astromik/SQM/SQM_verze411/hw/katalogove_listy/čočka-OEHW2030GF.pdf

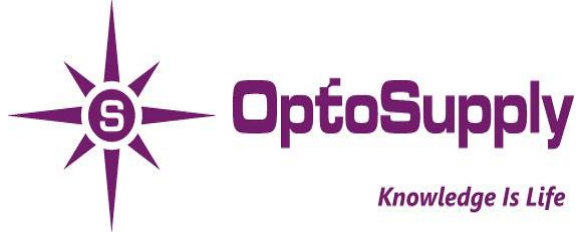
[picture p48: figure]
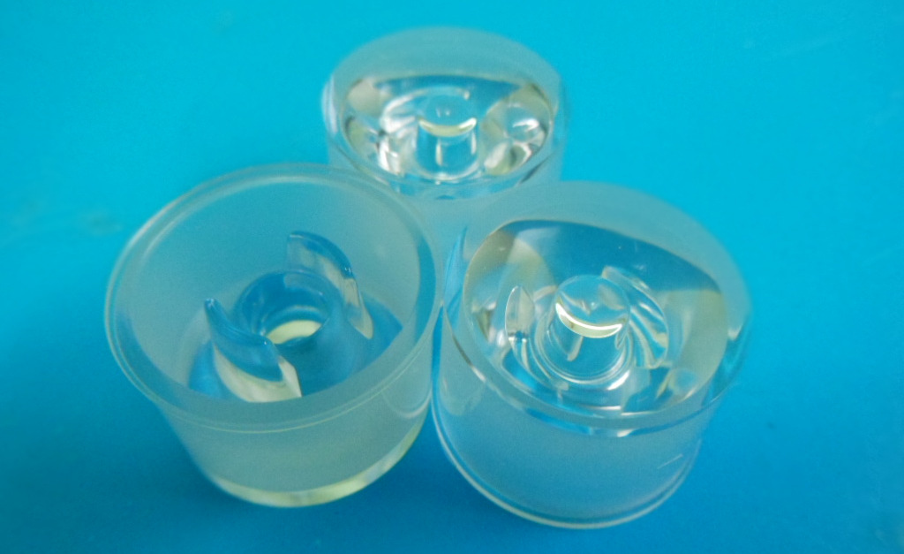
[picture p49: figure]
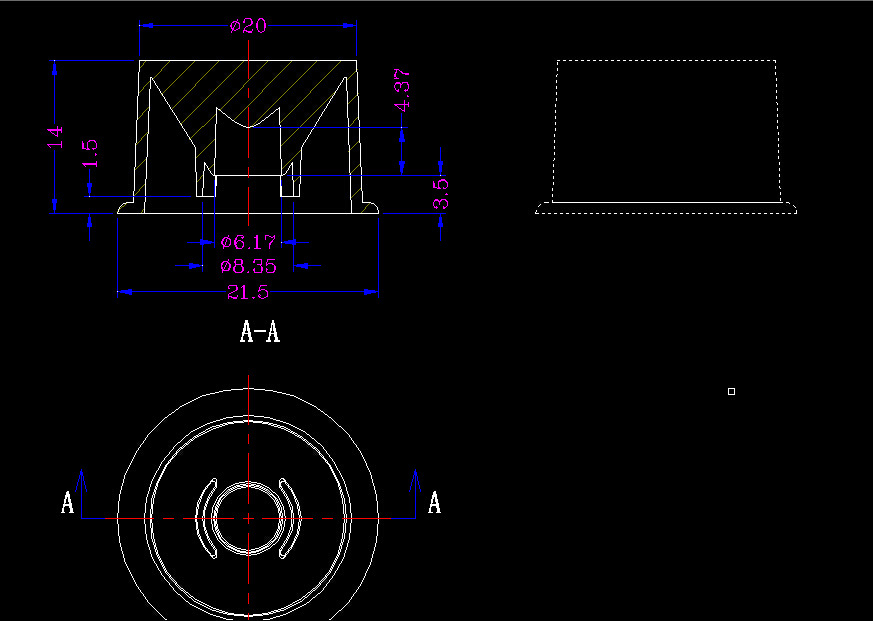
[picture p50: figure]

www.optosupply.hk | 1 | ver.1

Unit:mm
| Tolerance:±0.3mm
Descriptions: | 1
Models | OEHW2030GF
Specification | φ21.5*14mm
Perspective | 30
Wick | 1
Material | PMMA
Transmittance | 93%
Temperature | -35℃-90℃
Tolerance | ±0.3mm
Standard | SGS/ROHS
Surface Treatment | Transparent
Product Picture and Dimensions | s
Model No. | OEHW2030GF
VER. | 1
