astromik/SQM/SQM_verze411/hw/katalogove_listy/KL-switch-ss-12d06l5.pdf

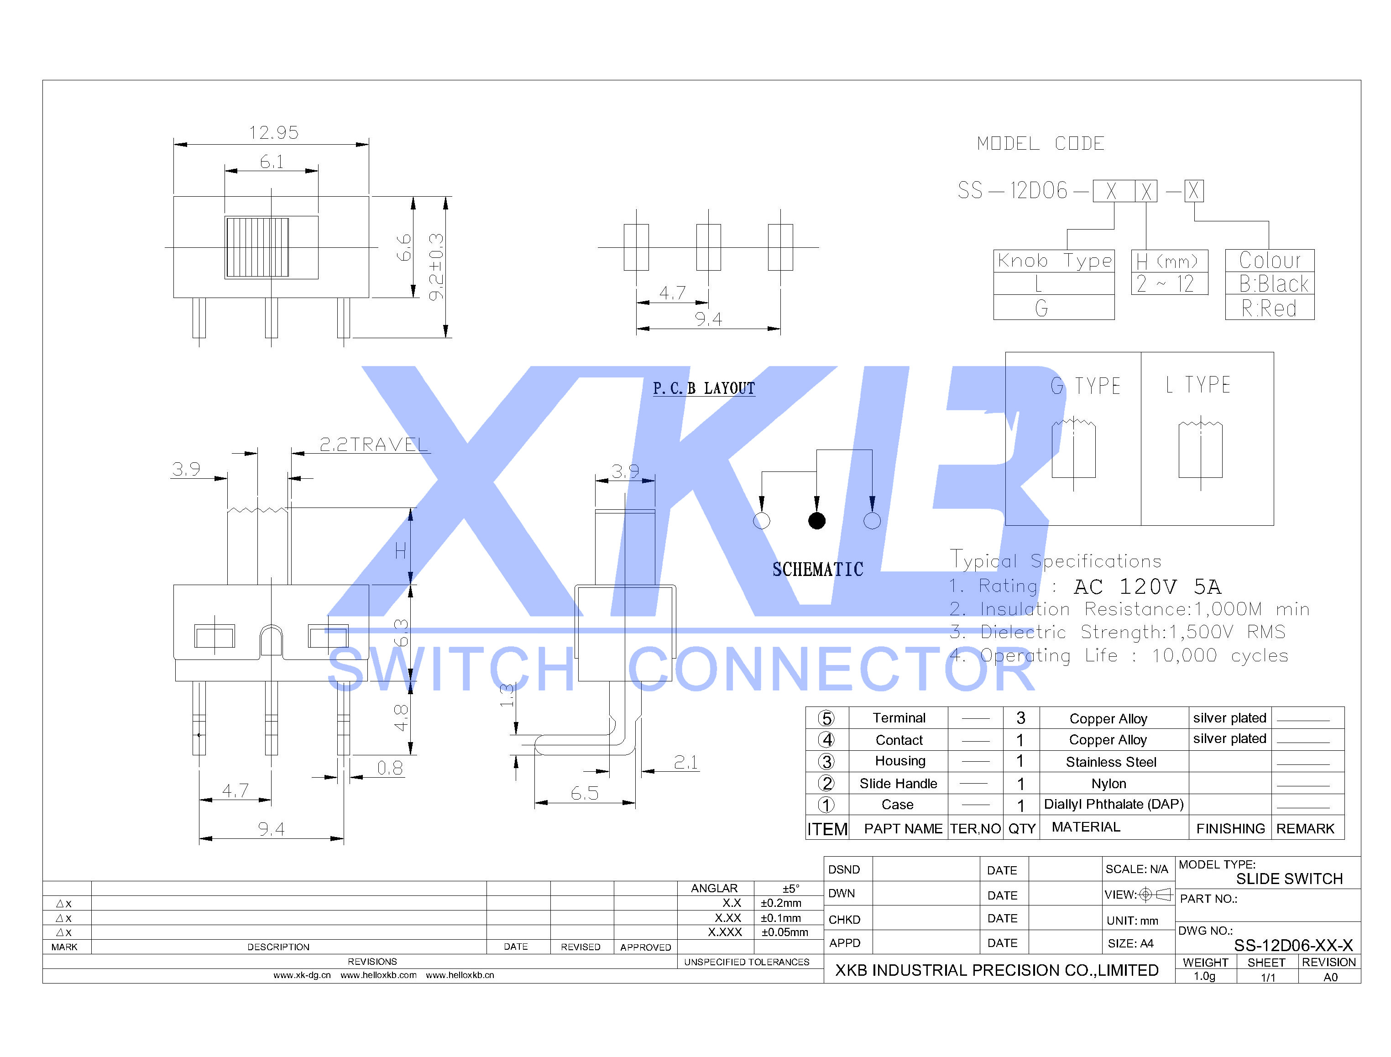
[picture p112: page 1]
