astromik/SQM/SQM_verze411/hw/krabicka/detaily_jlcpcb.gif

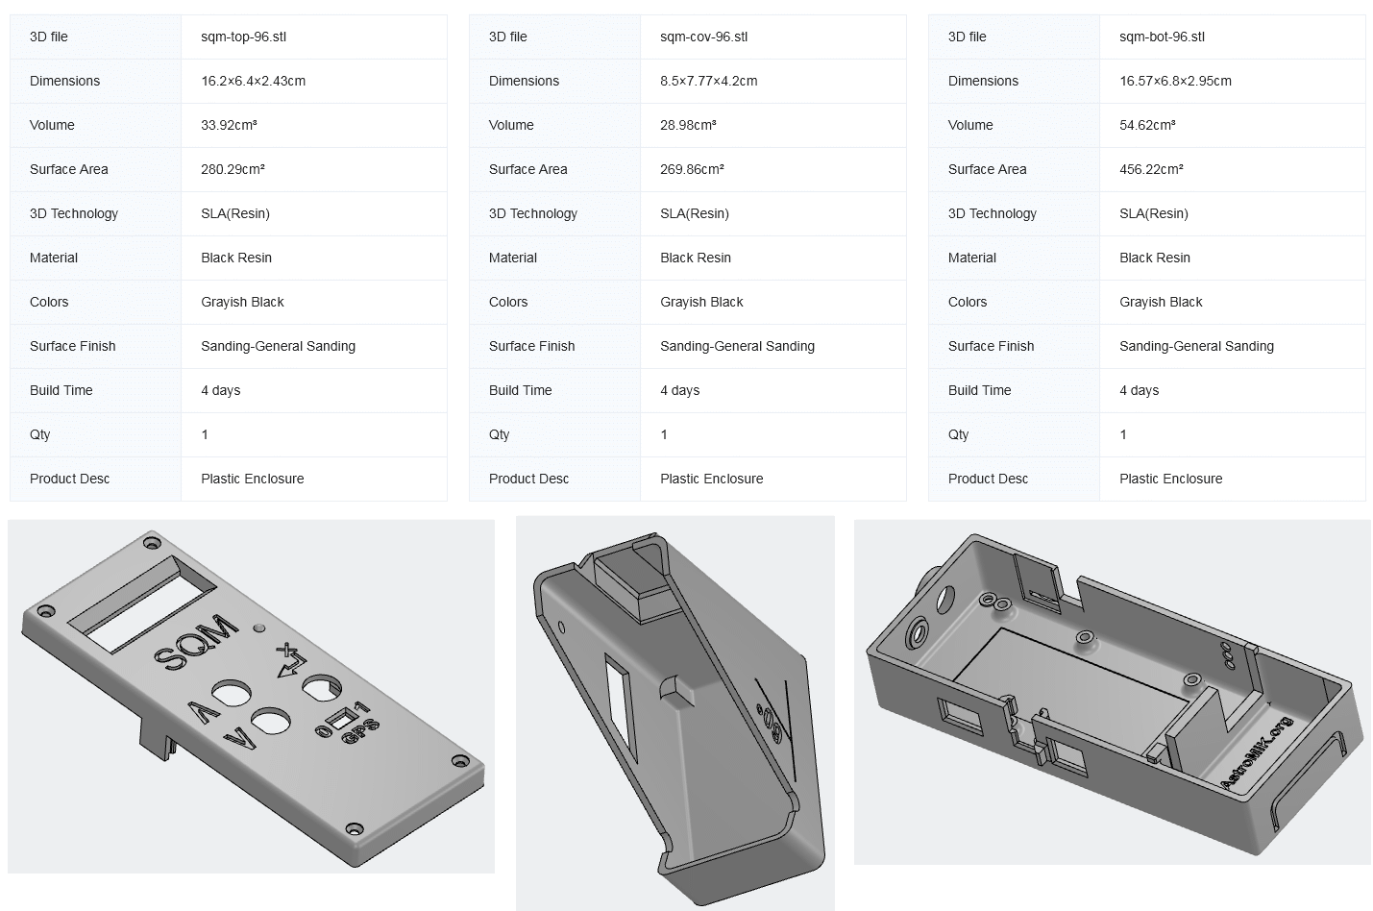
SQM_verze411/hw/krabicka/detaily_jlcpcb.gif
