astromik/SQM/SQM_verze411/hw/krabicka/krabicka_obr1.gif

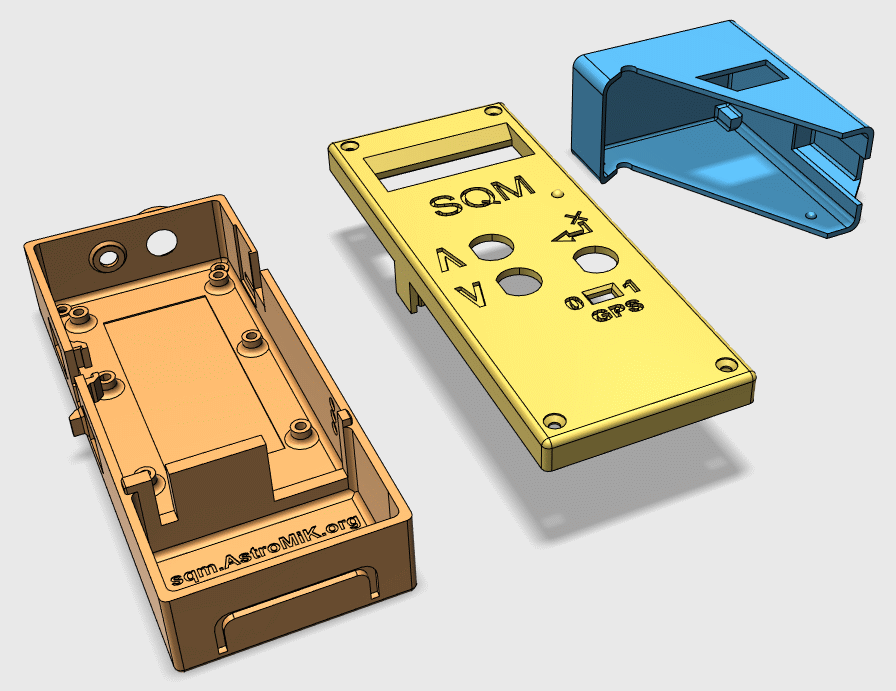
SQM_verze411/hw/krabicka/krabicka_obr1.gif
