astromik/SQM/SQM_verze411/hw/krabicka/krabicka_obr2.gif

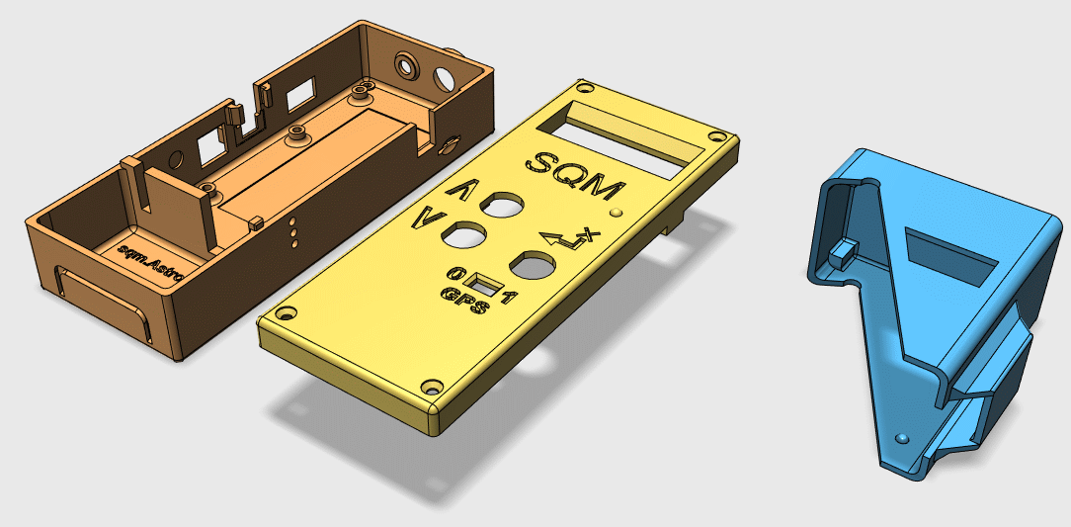
SQM_verze411/hw/krabicka/krabicka_obr2.gif
