astromik/SQM/SQM_verze411/hw/krabicka/krabicka_obr3.gif

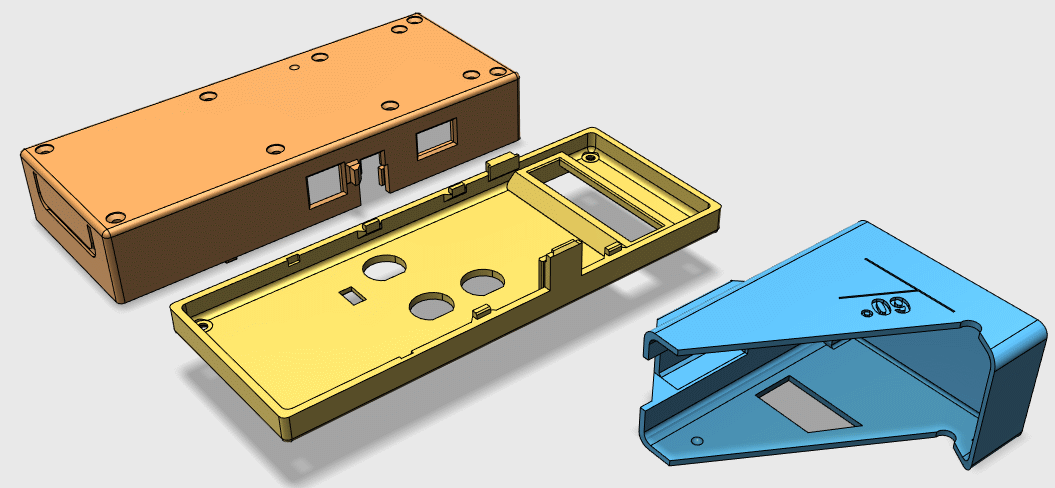
SQM_verze411/hw/krabicka/krabicka_obr3.gif
