astromik/SQM/SQM_verze411/programy/STM32_CubeProgrammer/CubeProg_screen.gif

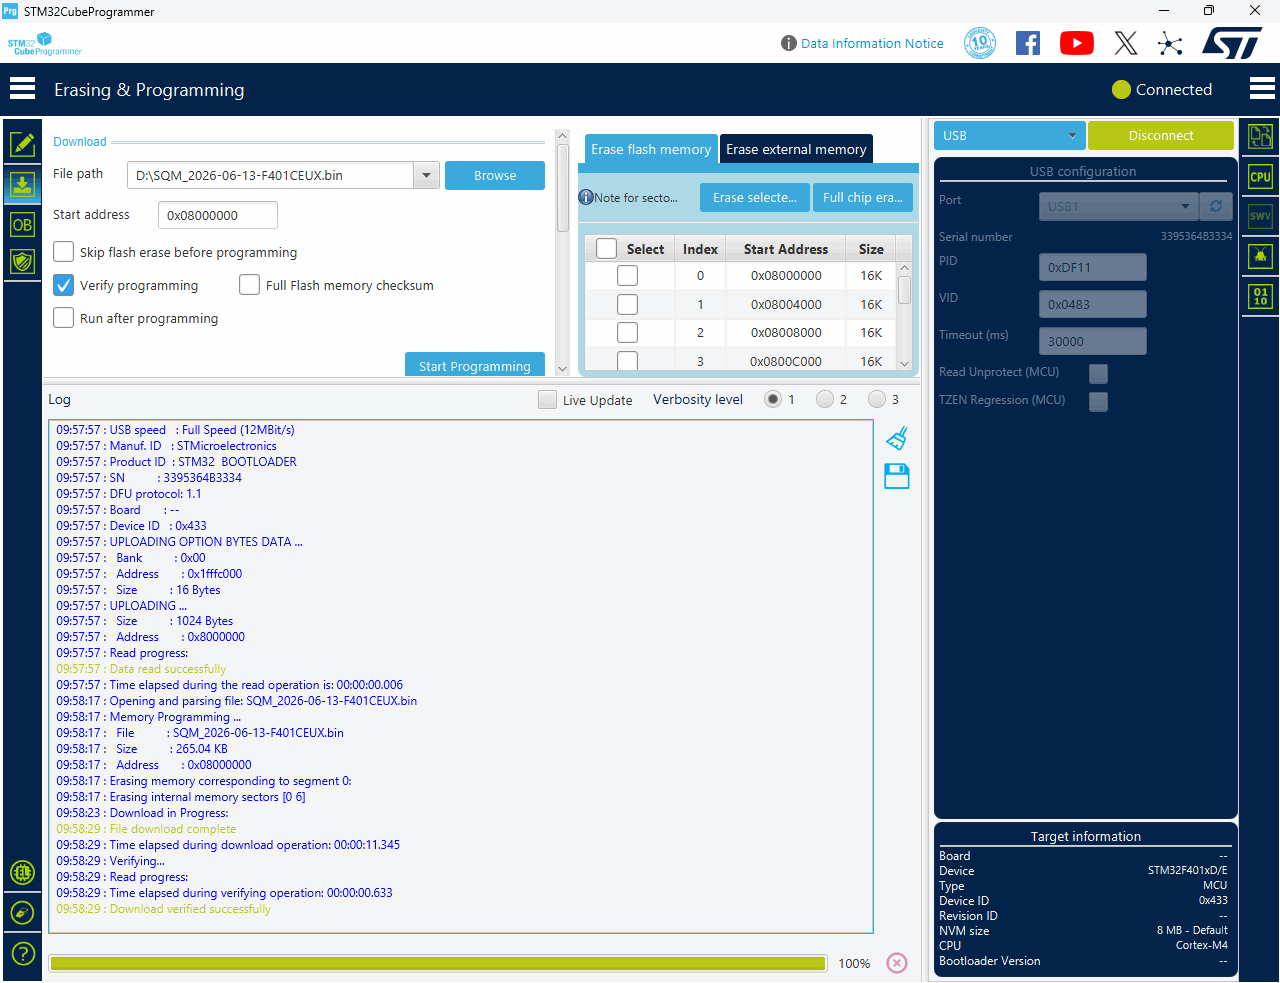
SQM_verze411/programy/STM32_CubeProgrammer/CubeProg_screen.gif
