astromik/SQM/SQM_verze411/webconfig/baterie_top.gif

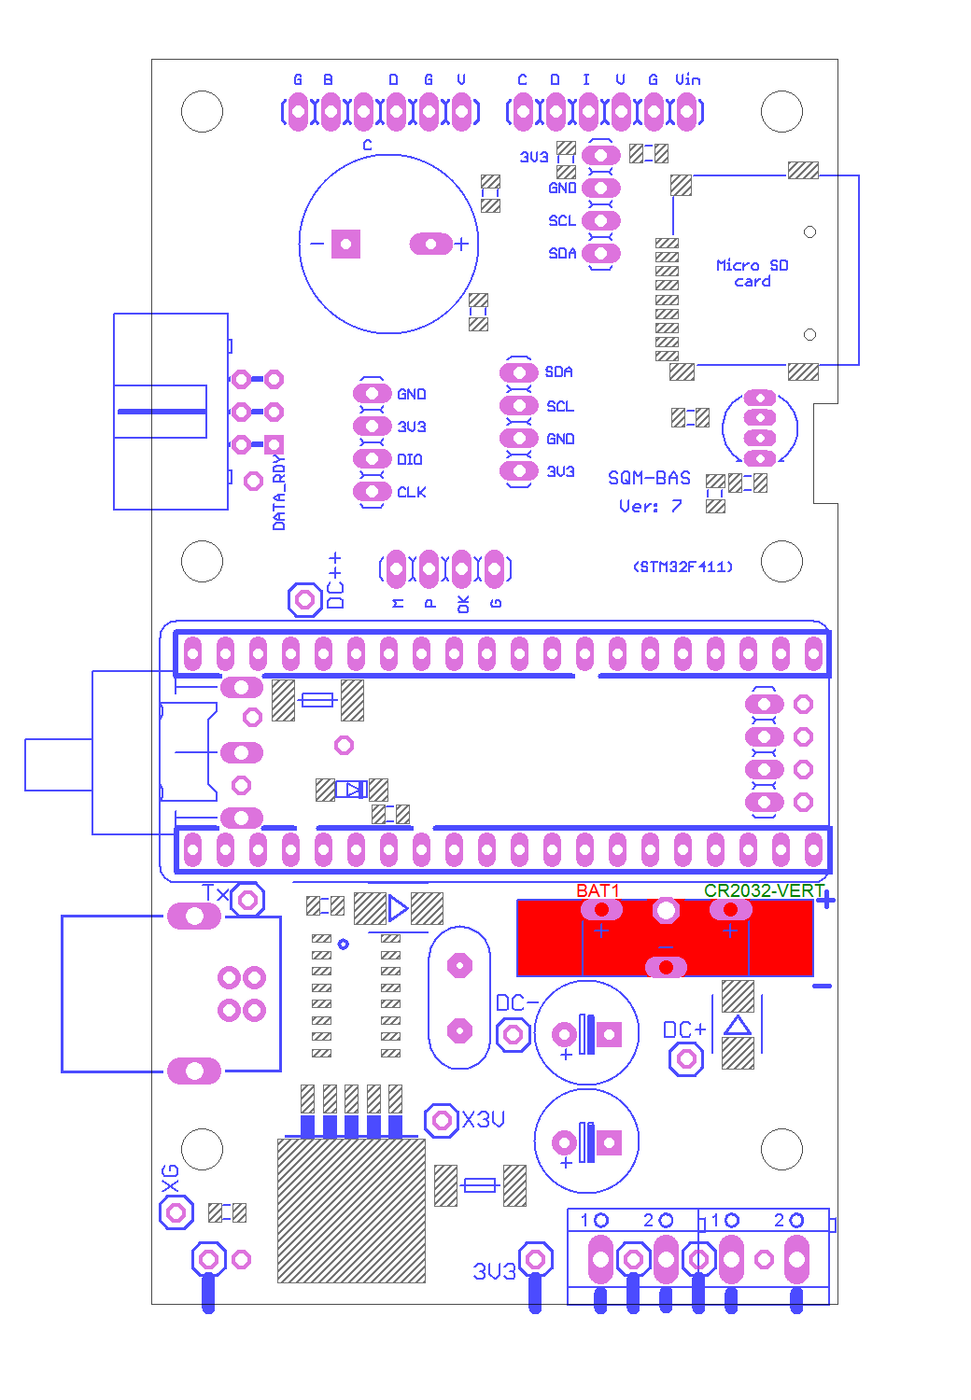
SQM_verze411/webconfig/baterie_top.gif
