astromik/SQM/SQM_verze411/webconfig/batkap_iko.jpg

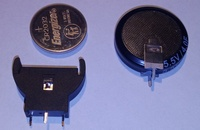
SQM_verze411/webconfig/batkap_iko.jpg
