astromik/SQM/SQM_verze411/webconfig/bme280_bot.gif

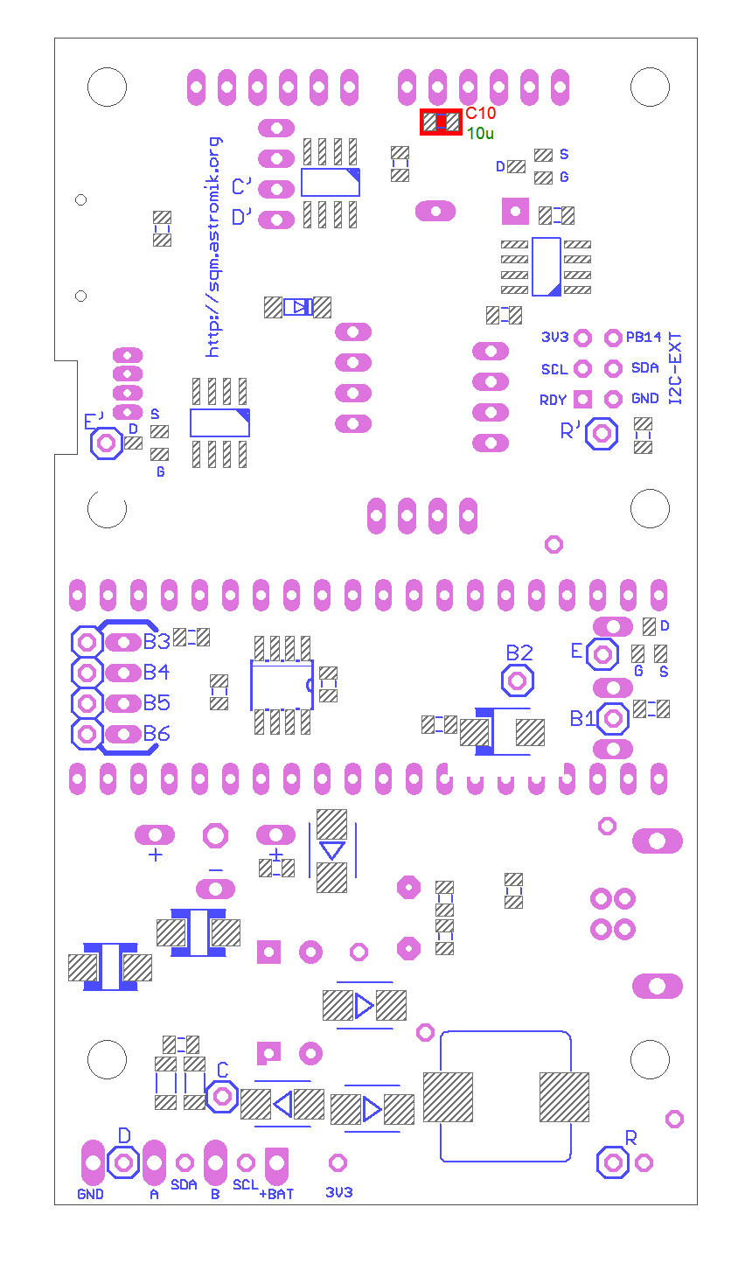
SQM_verze411/webconfig/bme280_bot.gif
