astromik/SQM/SQM_verze411/webconfig/bme280_top.gif

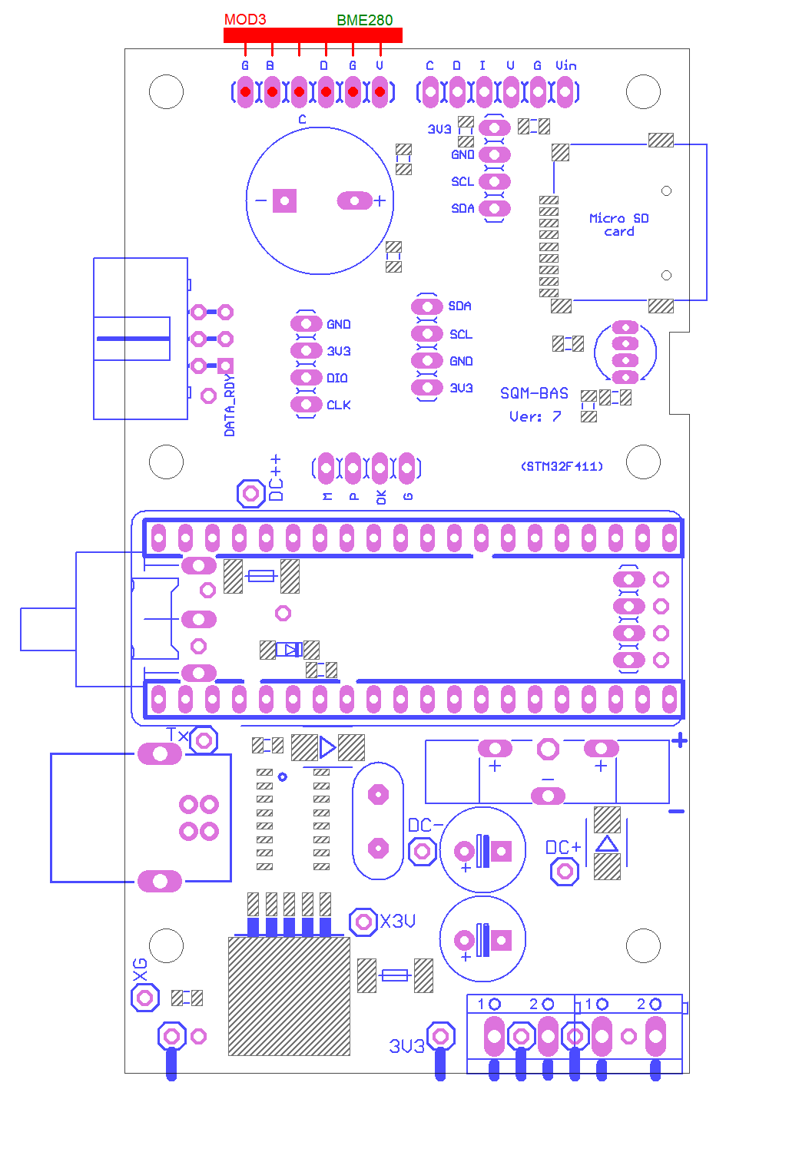
SQM_verze411/webconfig/bme280_top.gif
