astromik/SQM/SQM_verze411/webconfig/bme_iko.jpg

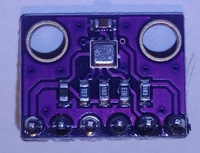
SQM_verze411/webconfig/bme_iko.jpg
