astromik/SQM/SQM_verze411/webconfig/bzuk_iko.jpg

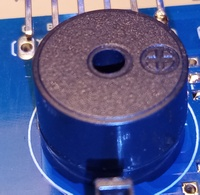
SQM_verze411/webconfig/bzuk_iko.jpg
