astromik/SQM/SQM_verze411/webconfig/bzuk_top.gif

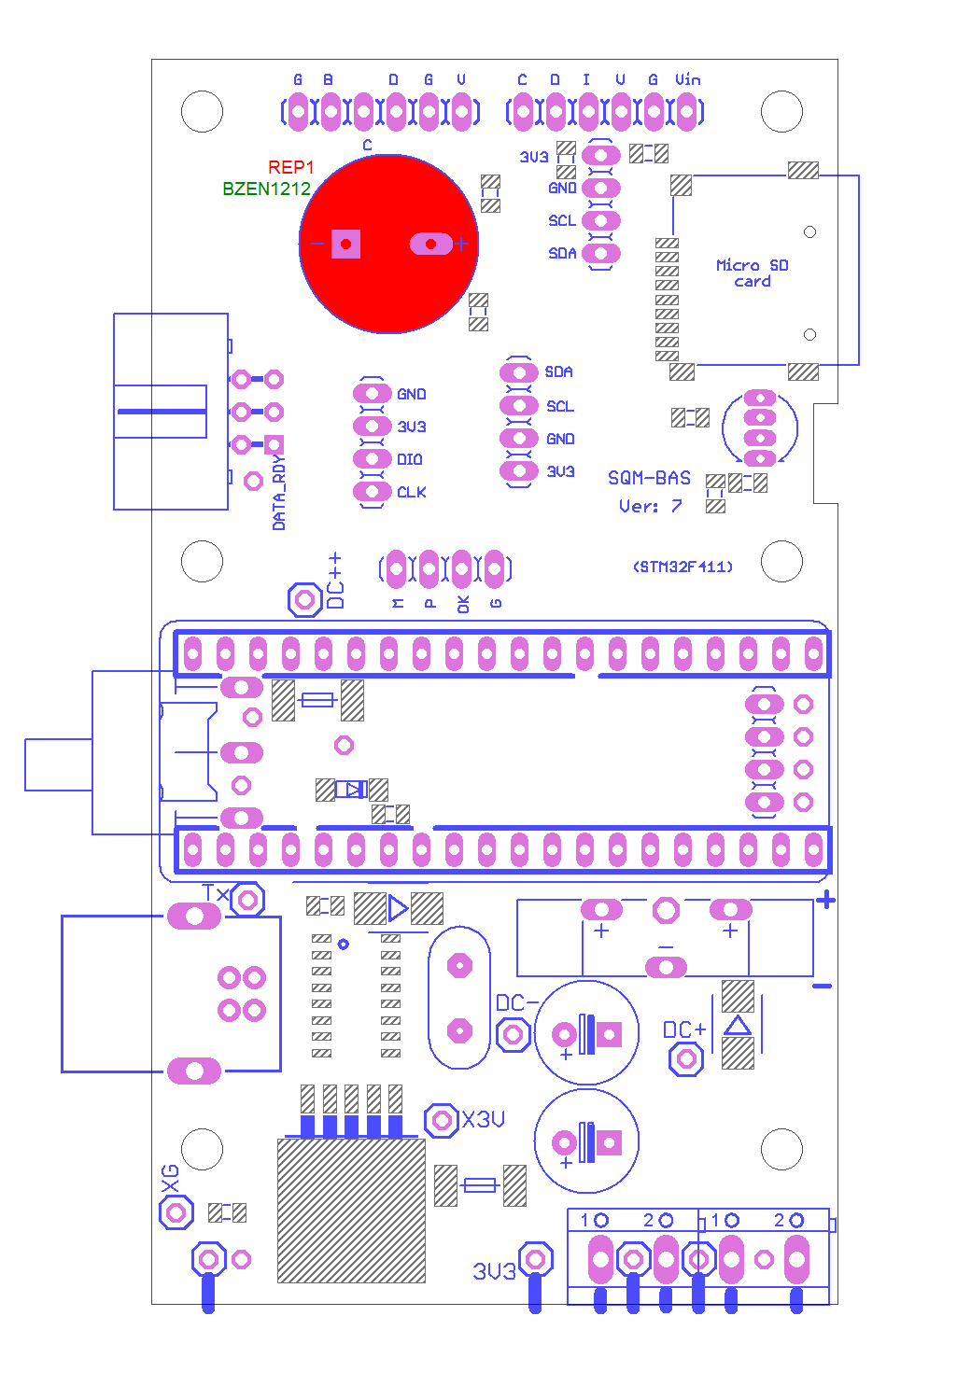
SQM_verze411/webconfig/bzuk_top.gif
