astromik/SQM/SQM_verze411/webconfig/dis_iko.jpg

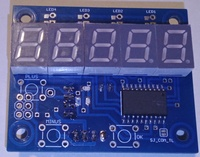
SQM_verze411/webconfig/dis_iko.jpg
