astromik/SQM/SQM_verze411/webconfig/displej_top.gif

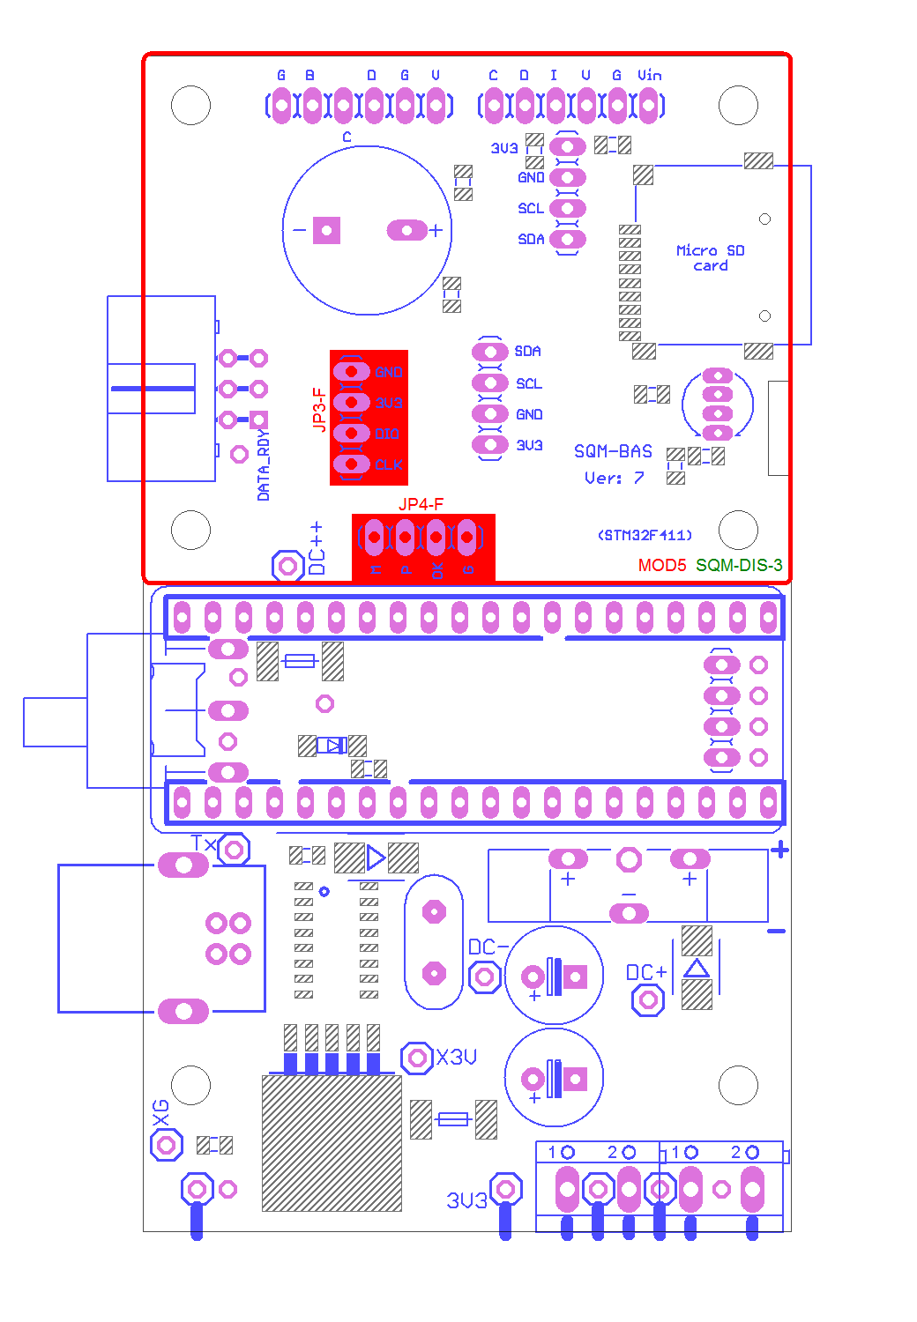
SQM_verze411/webconfig/displej_top.gif
