astromik/SQM/SQM_verze411/webconfig/ext_iko.jpg

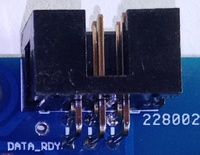
SQM_verze411/webconfig/ext_iko.jpg
