astromik/SQM/SQM_verze411/webconfig/fot_bme_cin.jpg

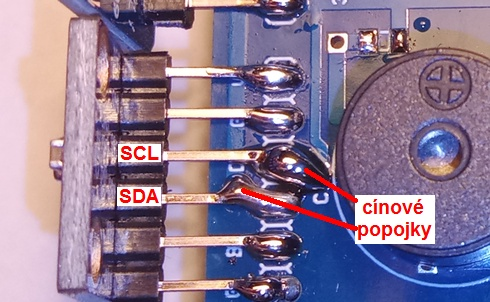
SQM_verze411/webconfig/fot_bme_cin.jpg
