astromik/SQM/SQM_verze411/webconfig/fot_propoj_lsm.jpg

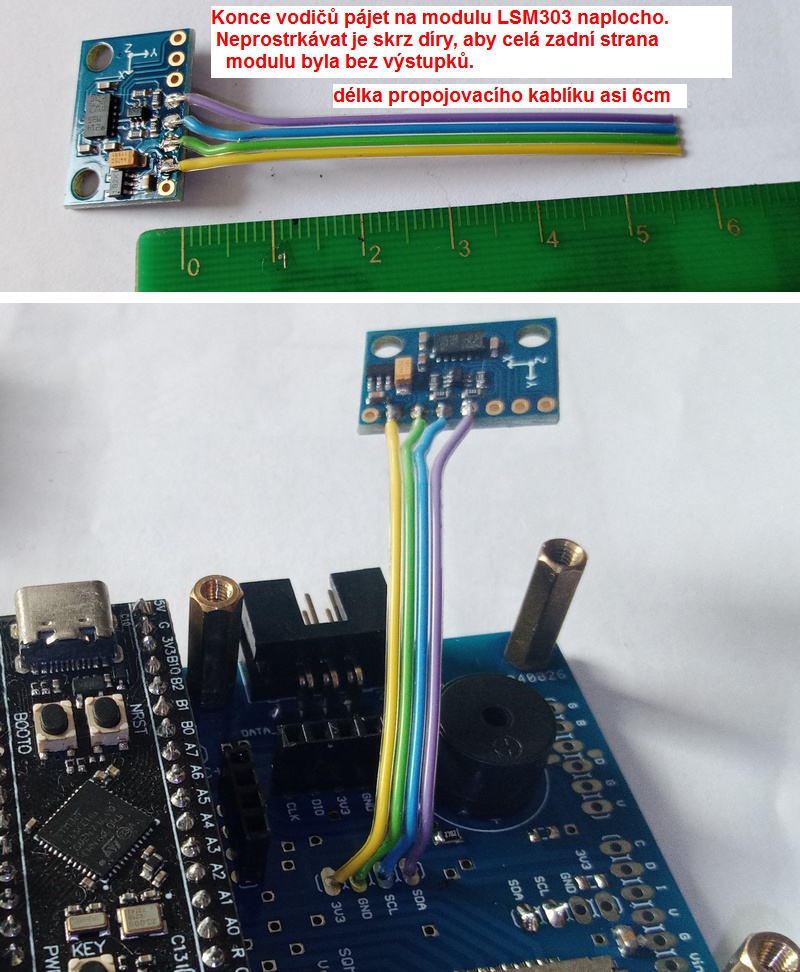
SQM_verze411/webconfig/fot_propoj_lsm.jpg
