astromik/SQM/SQM_verze411/webconfig/fot_propoj_tl_dis.jpg

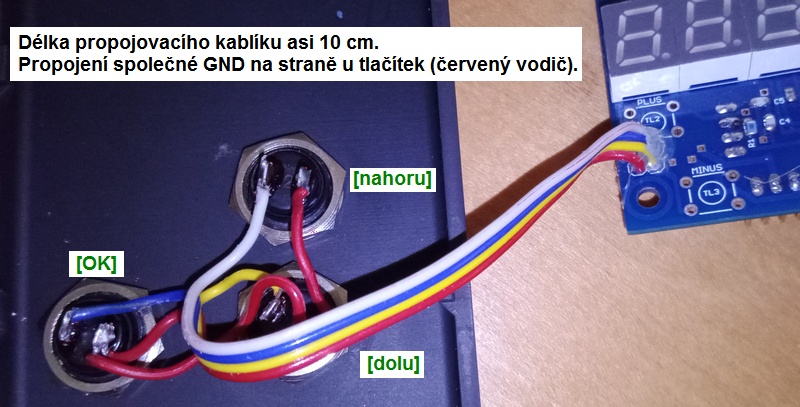
SQM_verze411/webconfig/fot_propoj_tl_dis.jpg
