astromik/SQM/SQM_verze411/webconfig/fot_ts_propoj.jpg

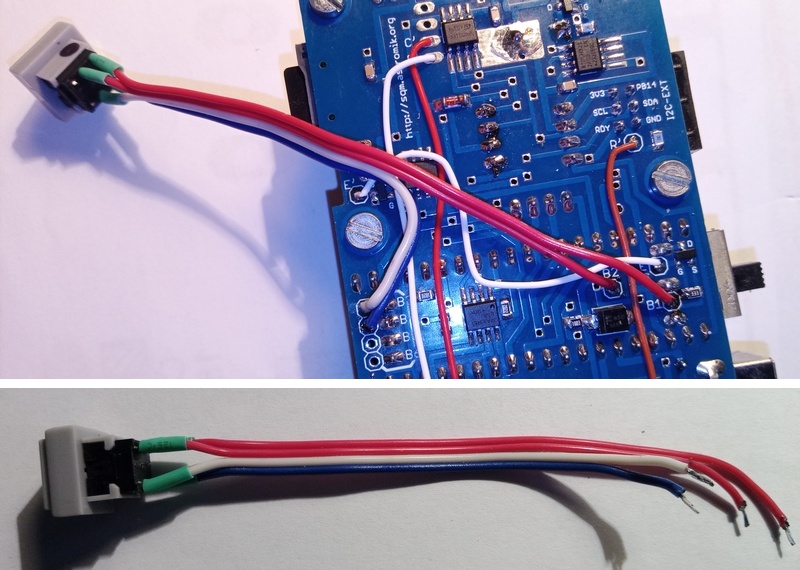
SQM_verze411/webconfig/fot_ts_propoj.jpg
