astromik/SQM/SQM_verze411/webconfig/gps1_iko.jpg

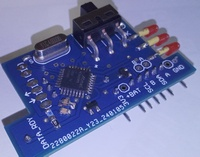
SQM_verze411/webconfig/gps1_iko.jpg
