astromik/SQM/SQM_verze411/webconfig/gps2_iko.jpg

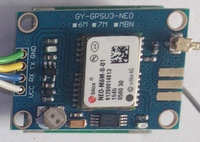
SQM_verze411/webconfig/gps2_iko.jpg
