astromik/SQM/SQM_verze411/webconfig/lsm303_top.gif

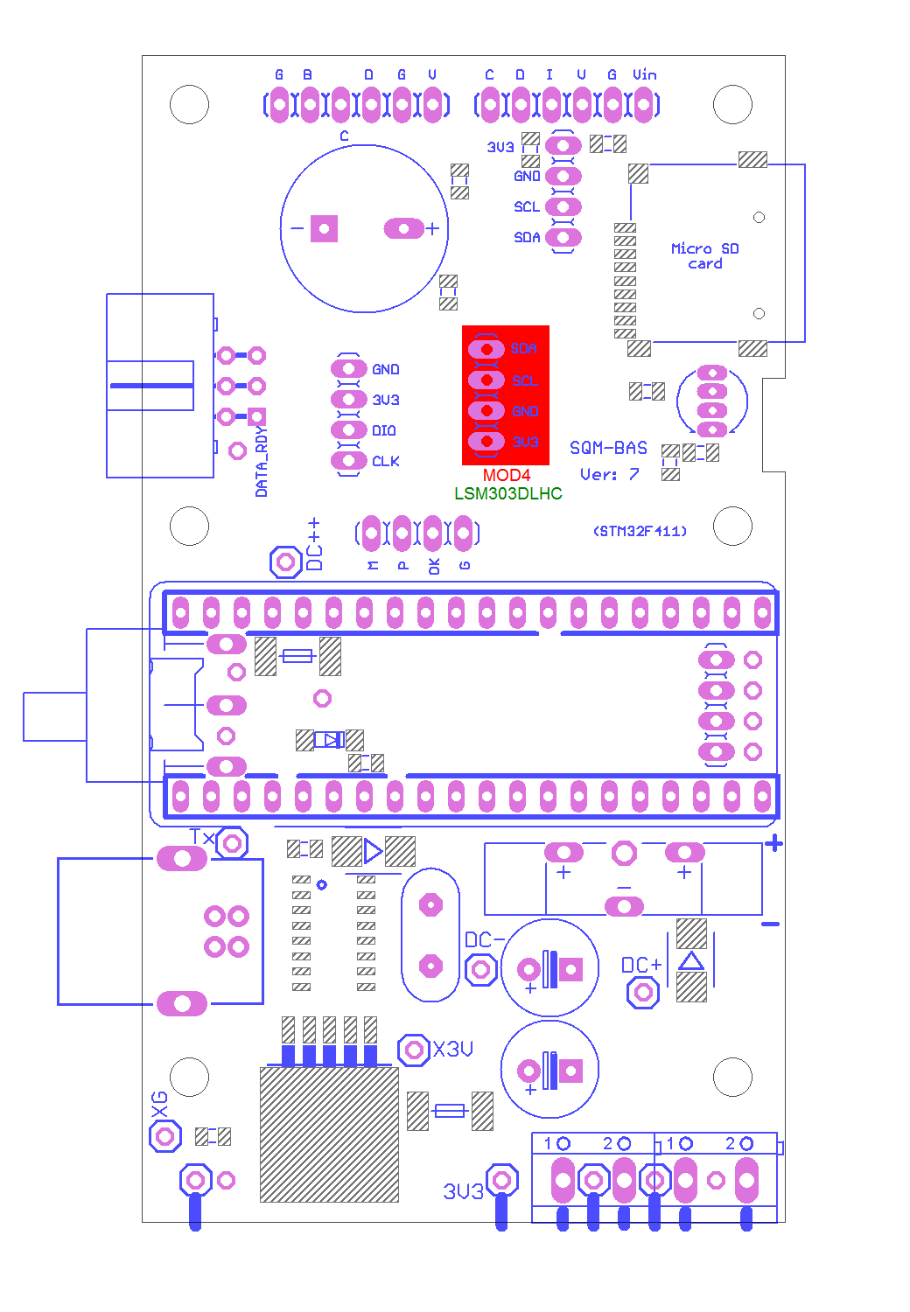
SQM_verze411/webconfig/lsm303_top.gif
