astromik/SQM/SQM_verze411/webconfig/pevne_schema.gif

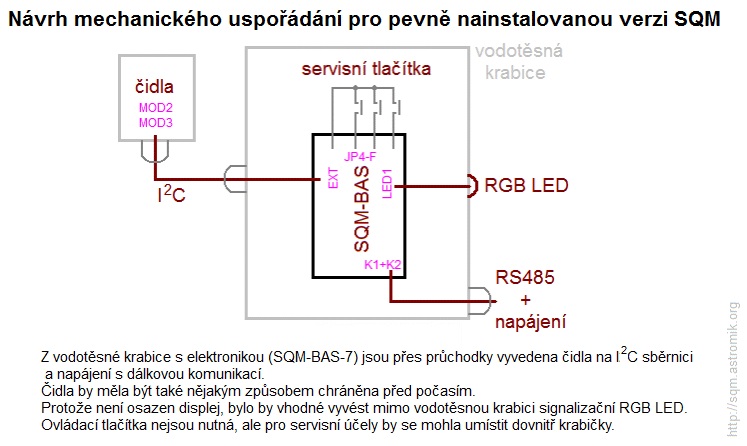
SQM_verze411/webconfig/pevne_schema.gif
