astromik/SQM/SQM_verze411/webconfig/propoj_485_gps.gif

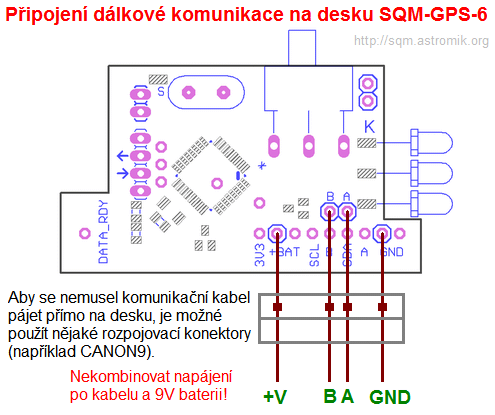
SQM_verze411/webconfig/propoj_485_gps.gif
