astromik/SQM/SQM_verze411/webconfig/propoj_bat_bas.gif

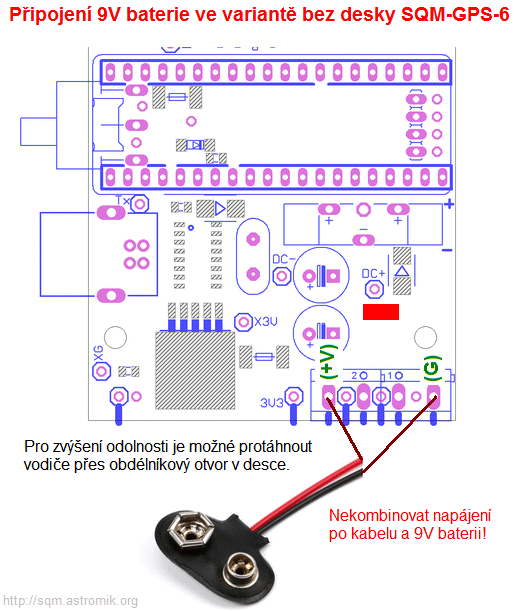
SQM_verze411/webconfig/propoj_bat_bas.gif
