astromik/SQM/SQM_verze411/webconfig/propoj_bat_gps.gif

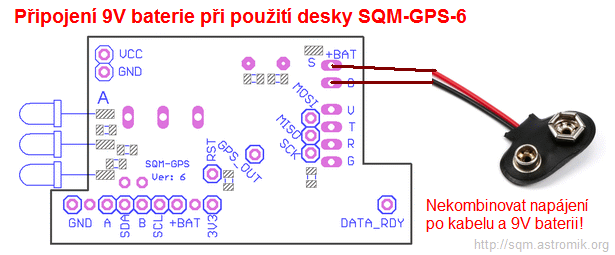
SQM_verze411/webconfig/propoj_bat_gps.gif
