astromik/SQM/SQM_verze411/webconfig/propoj_jack_bas.gif

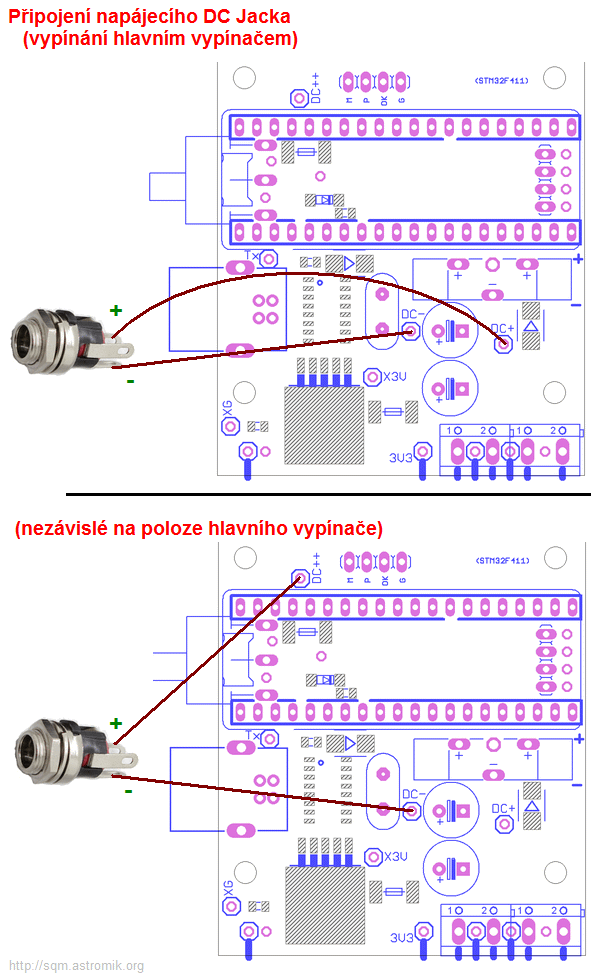
SQM_verze411/webconfig/propoj_jack_bas.gif
