astromik/SQM/SQM_verze411/webconfig/propoj_lsm_bas.gif

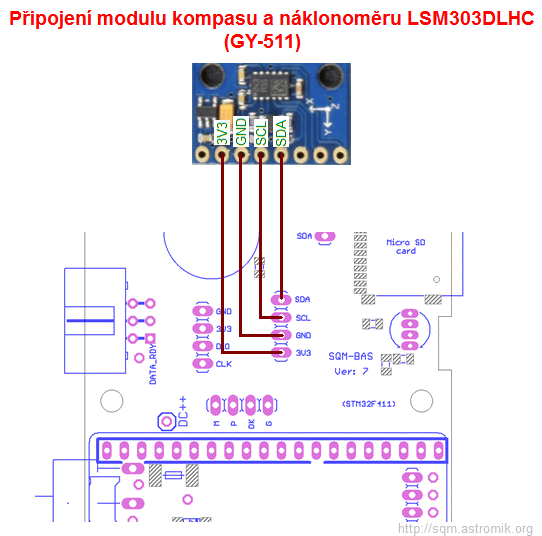
SQM_verze411/webconfig/propoj_lsm_bas.gif
