astromik/SQM/SQM_verze411/webconfig/propoj_neo_gps.gif

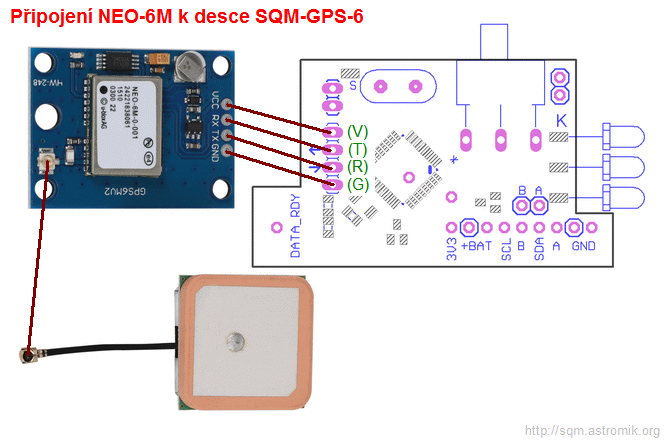
SQM_verze411/webconfig/propoj_neo_gps.gif
