astromik/SQM/SQM_verze411/webconfig/propoj_tl_bas.gif

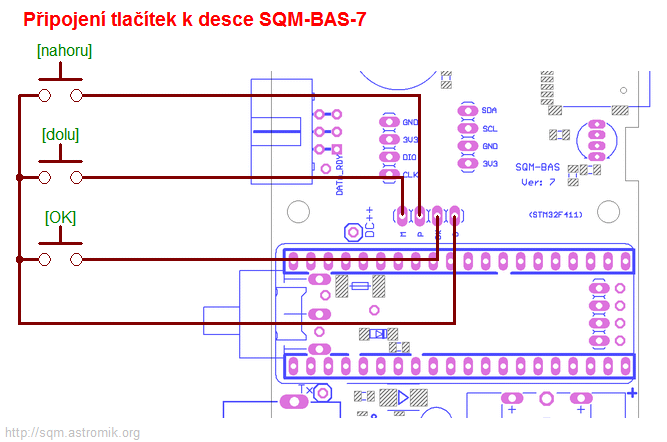
SQM_verze411/webconfig/propoj_tl_bas.gif
