astromik/SQM/SQM_verze411/webconfig/propoj_tl_dis.gif

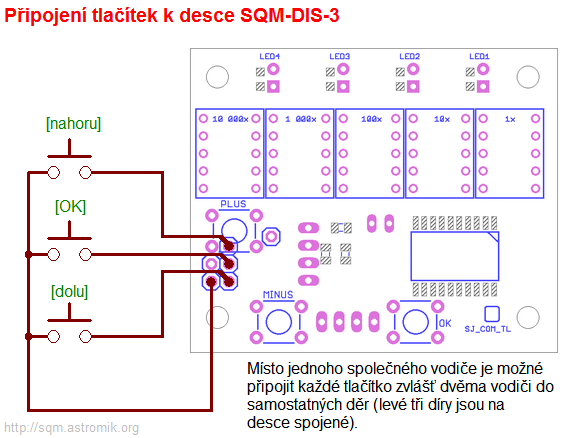
SQM_verze411/webconfig/propoj_tl_dis.gif
