astromik/SQM/SQM_verze411/webconfig/propoj_ts_bas.gif

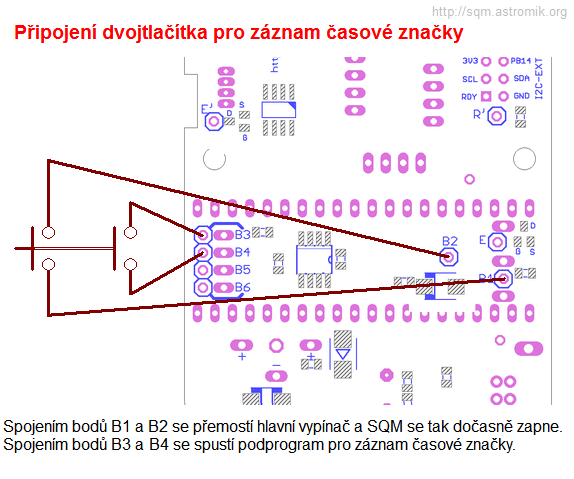
SQM_verze411/webconfig/propoj_ts_bas.gif
