astromik/SQM/SQM_verze411/webconfig/sd_iko.jpg

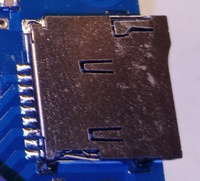
SQM_verze411/webconfig/sd_iko.jpg
