astromik/SQM/SQM_verze411/webconfig/sd_top.gif

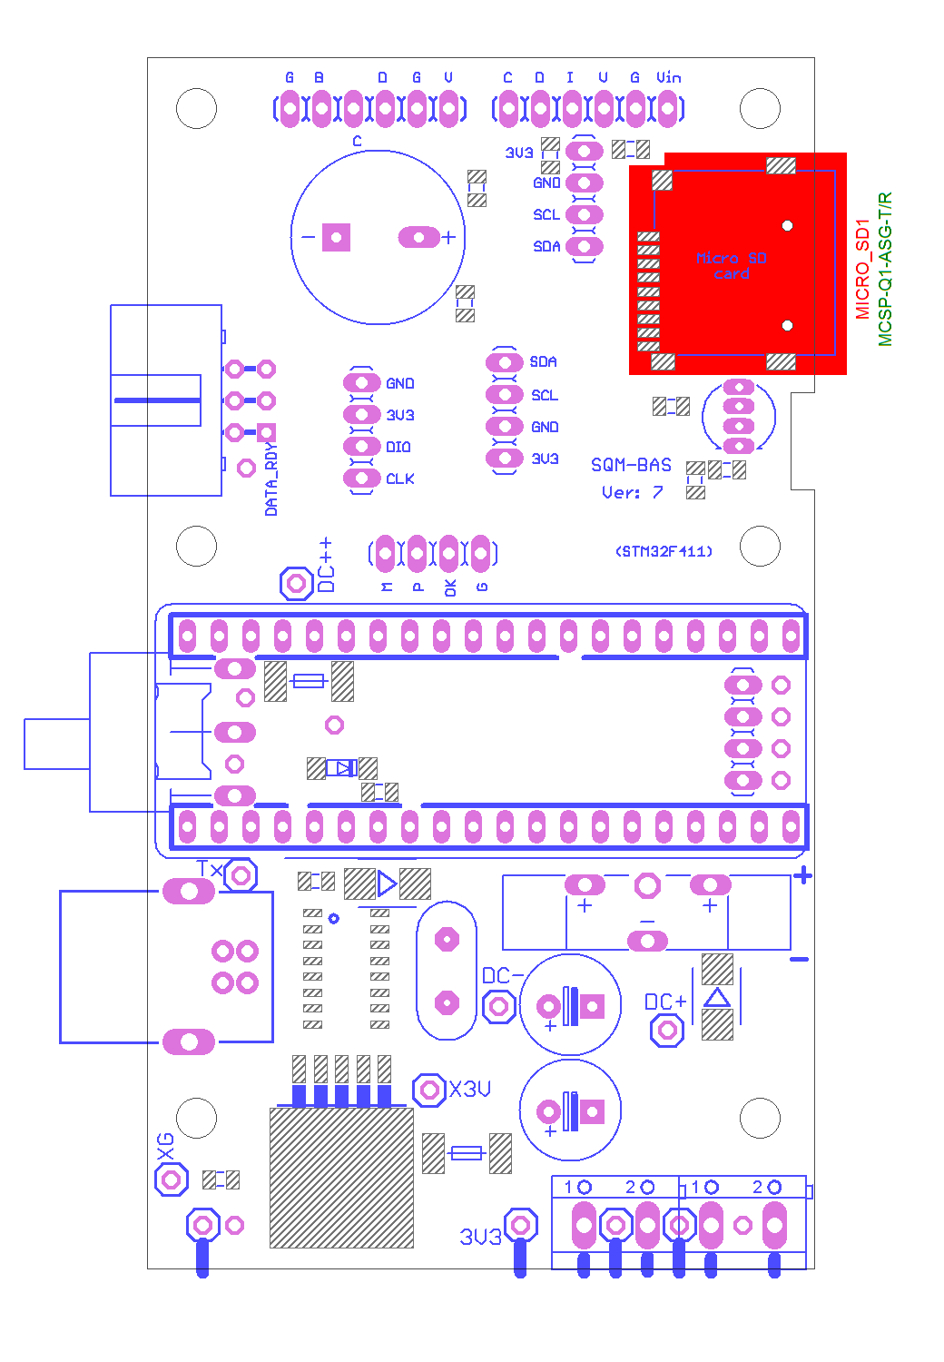
SQM_verze411/webconfig/sd_top.gif
