astromik/SQM/SQM_verze411/webconfig/sqm-dis-3_bot.gif

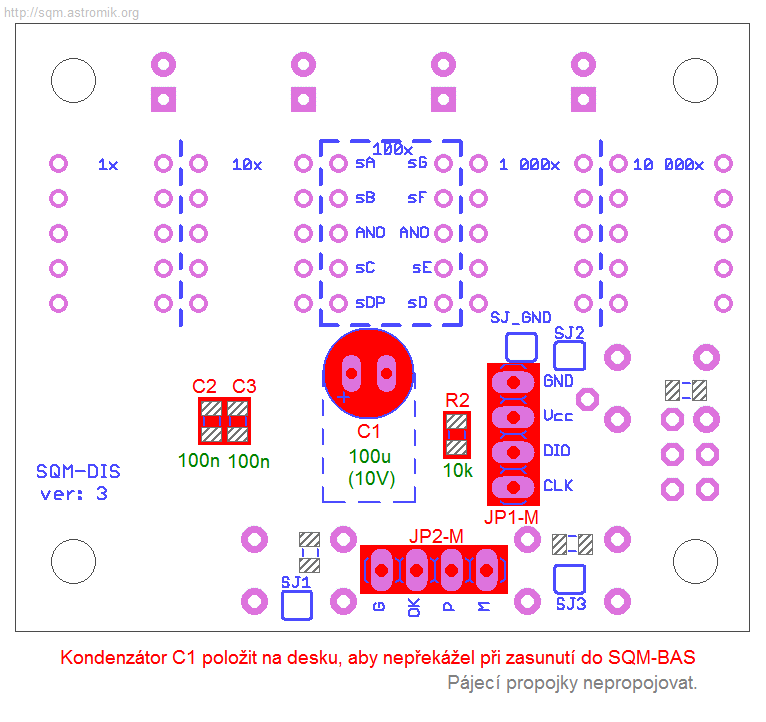
SQM_verze411/webconfig/sqm-dis-3_bot.gif
