astromik/SQM/SQM_verze411/webconfig/sqm-dis-3_top.gif

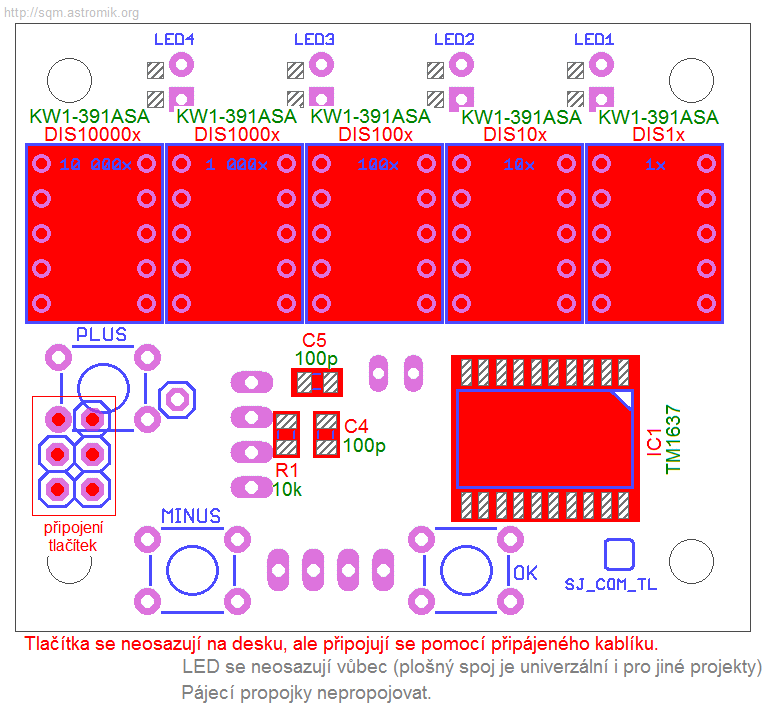
SQM_verze411/webconfig/sqm-dis-3_top.gif
