astromik/SQM/SQM_verze411/webconfig/sqm-gps-6_bot.gif

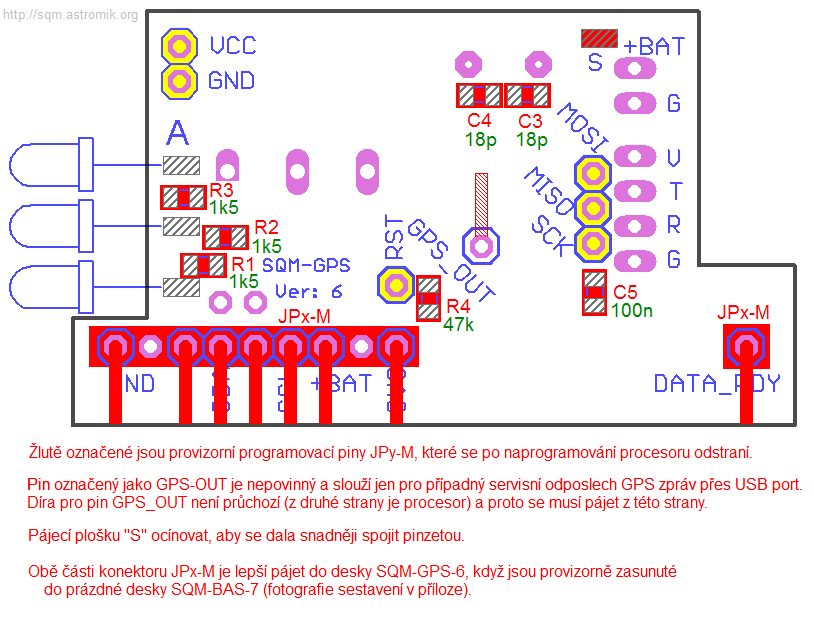
SQM_verze411/webconfig/sqm-gps-6_bot.gif
