astromik/SQM/SQM_verze411/webconfig/sqm-gps-6_top.gif

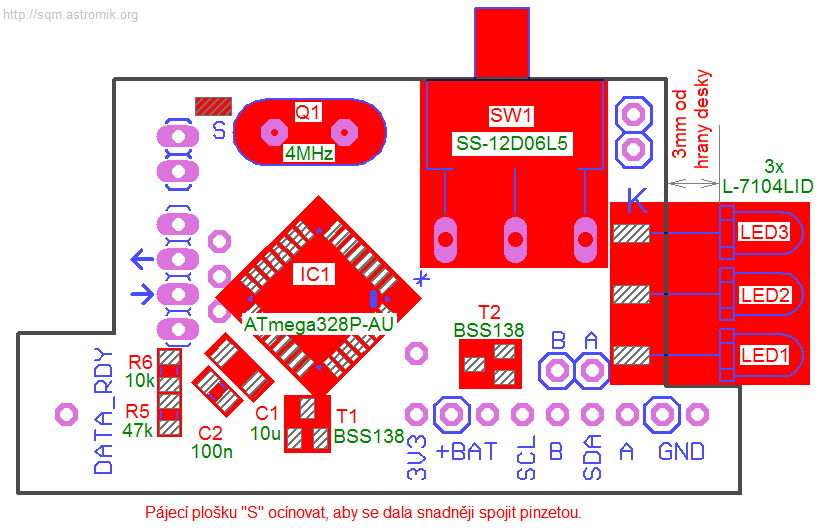
SQM_verze411/webconfig/sqm-gps-6_top.gif
