astromik/SQM/SQM_verze411/webconfig/ts_tl_delky.gif

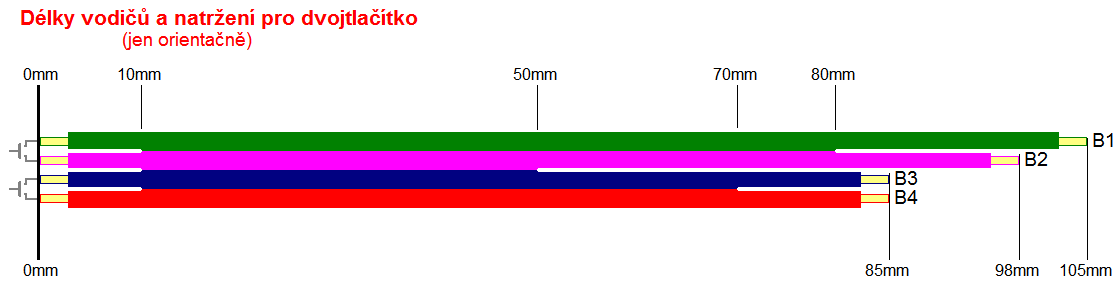
SQM_verze411/webconfig/ts_tl_delky.gif
