astromik/SQM/SQM_verze411/webconfig/vysledek.gif

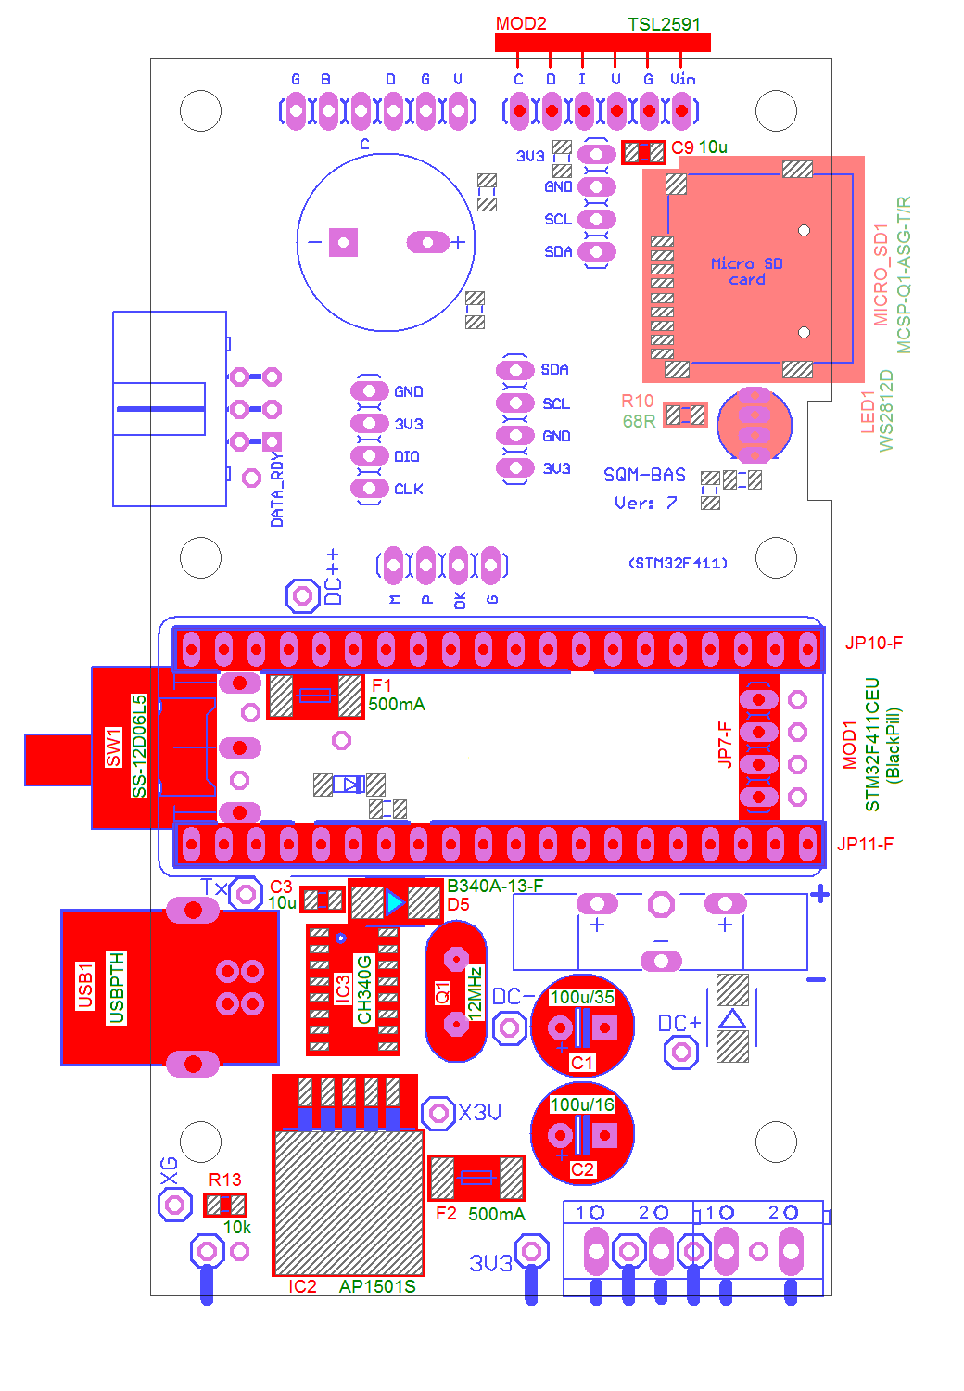
SQM_verze411/webconfig/vysledek.gif
