astromik/SQM/SQM_verze411/webconfig/vysledek_bot.gif

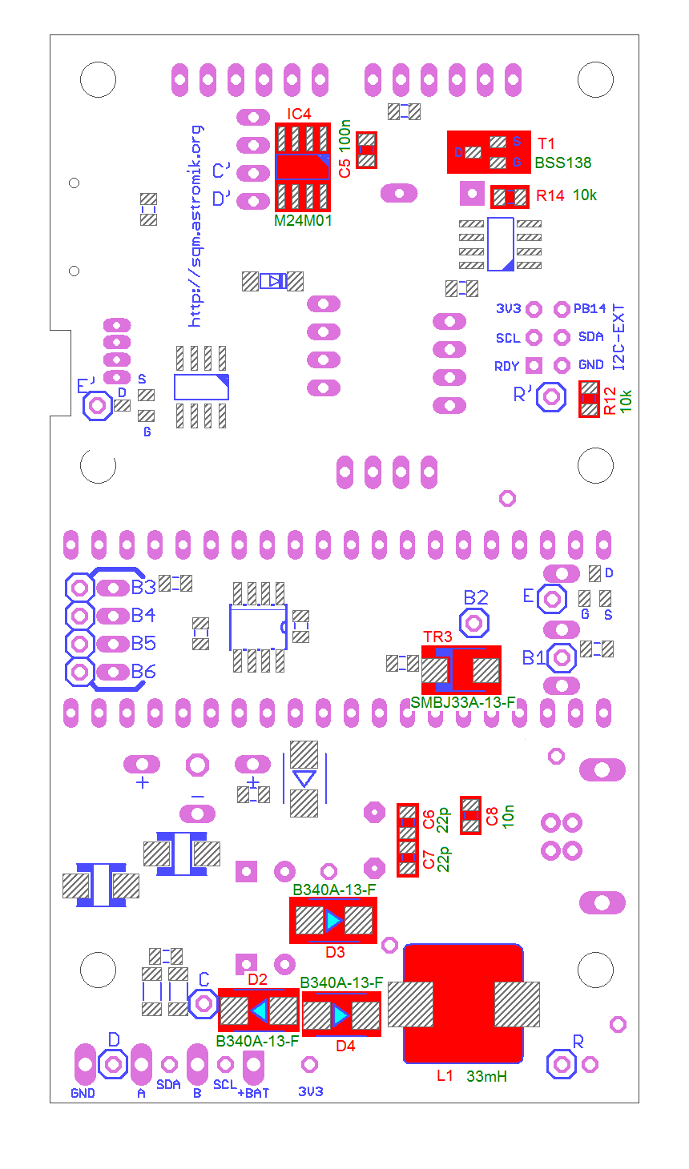
SQM_verze411/webconfig/vysledek_bot.gif
