astromik/SQM/SQM_verze411/webconfig/vysledek_top.gif

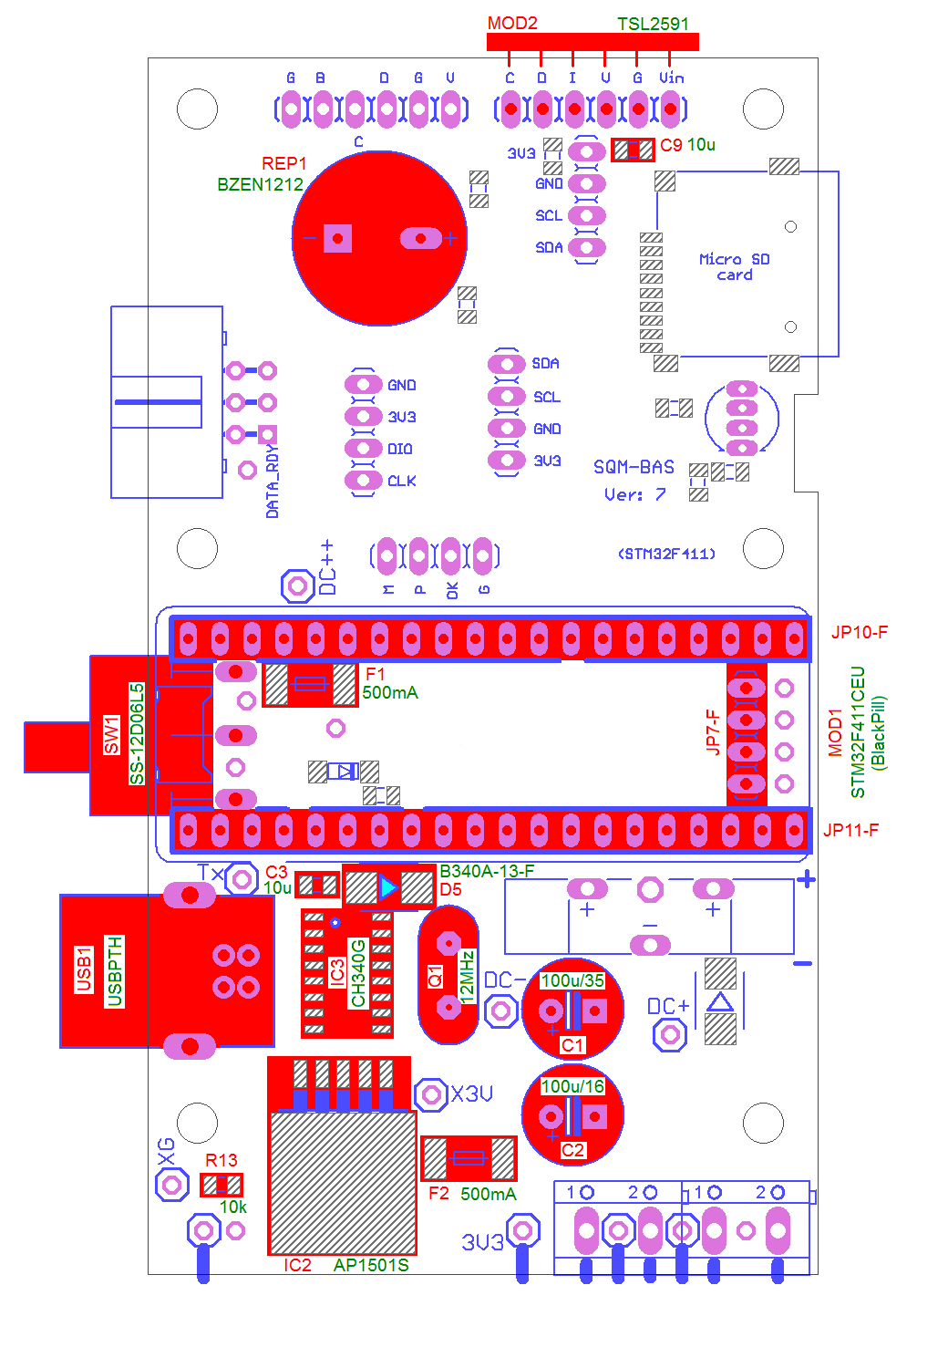
SQM_verze411/webconfig/vysledek_top.gif
