astromik/SQM/SQM_verze411/hw/pcb/sqm-bas/schema_bas.pdf

Nikdy se neosazují všechny součástky najednou. Varianty osazení v přiložených dokumentech.

# Základní deska SQM-BAS-7

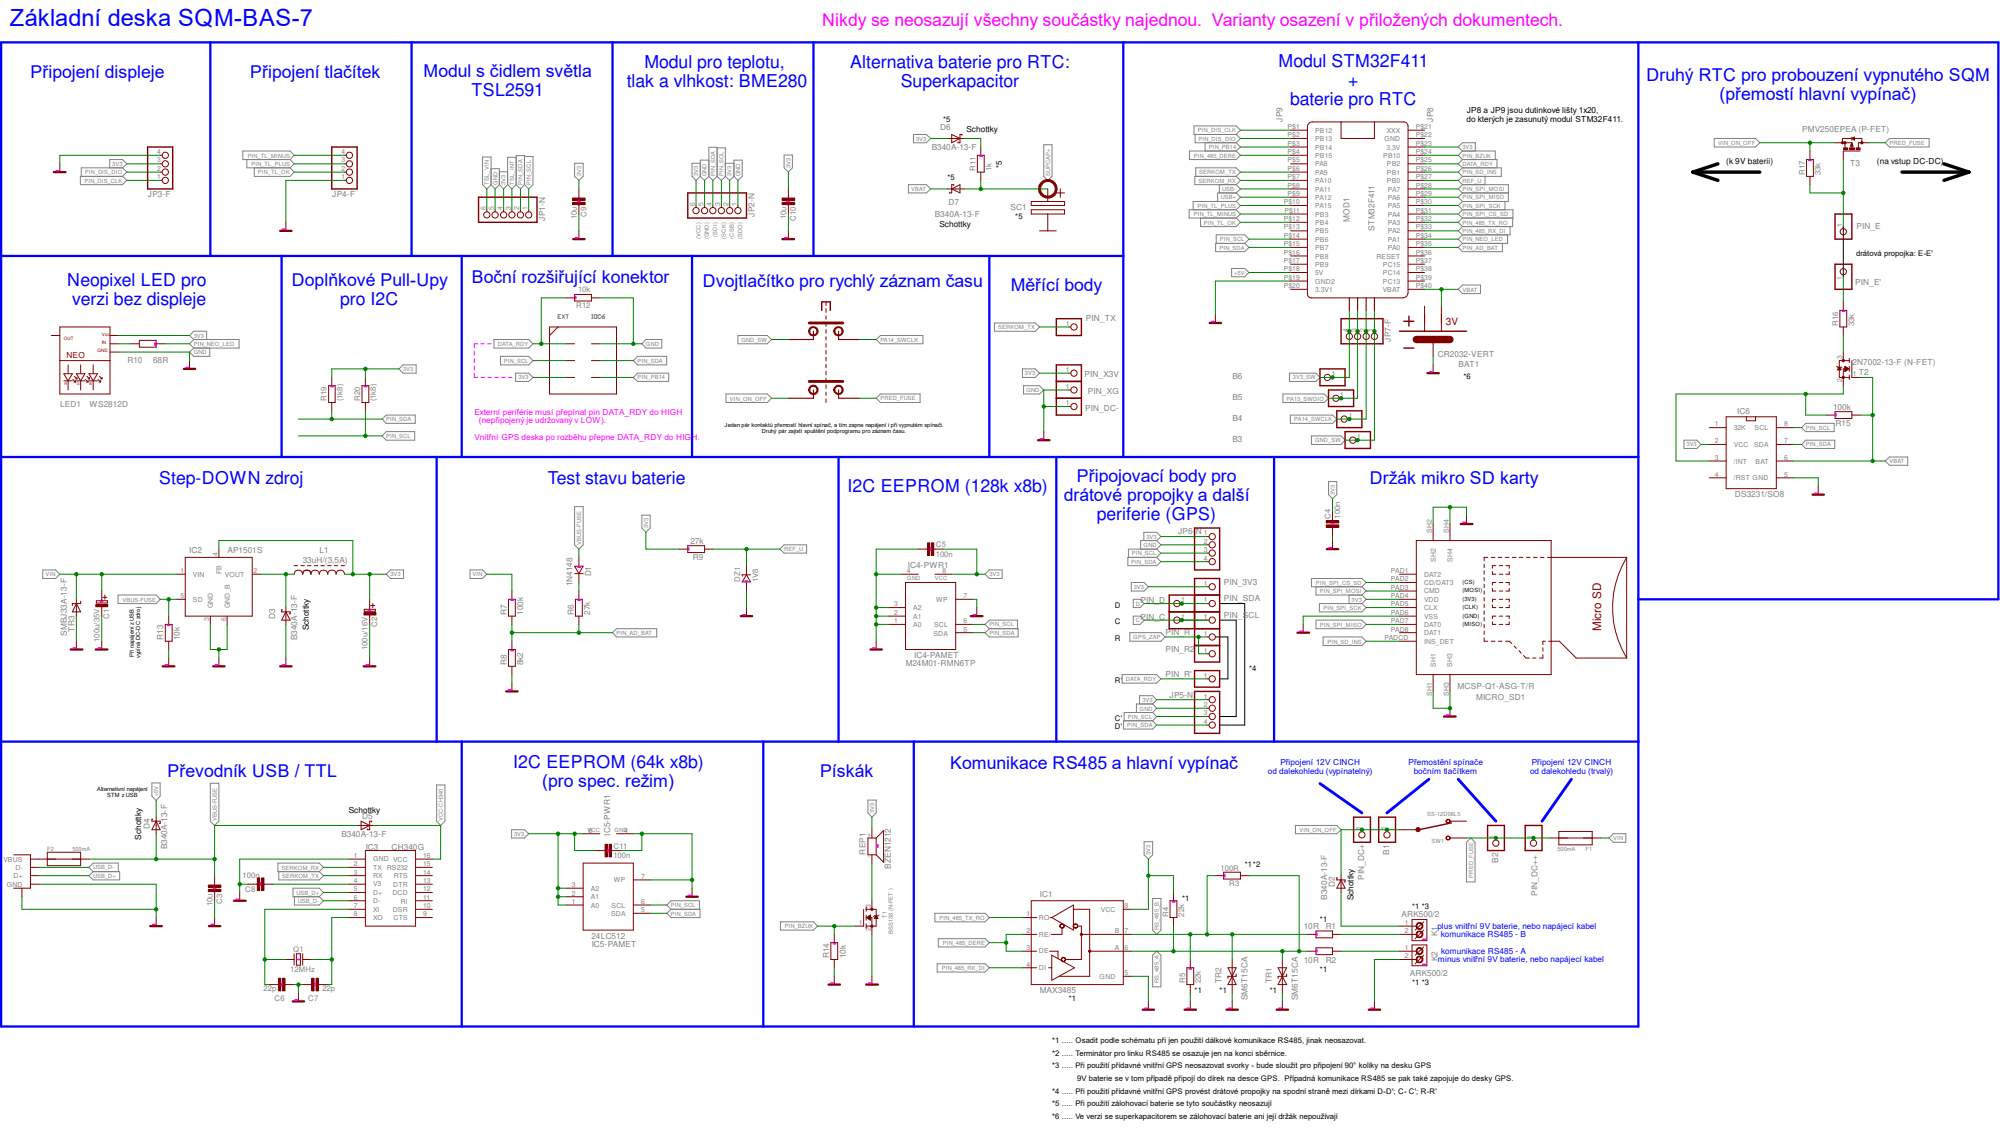
[picture p161: page 1]

Alternativa baterie pro RTC:
Superkapacitor

Druhý RTC pro probouzení vypnutého SQM

Externí periférie musí přepínat pin DATA_RDY do HIGH
(nepřipojený je udržovaný v LOW).

Vnitřní GPS deska po rozběhu přepne DATA_RDY do HIGH.

Jeden pár kontaktů přemostí hlavní spínač, a tím zapne napájení i při vypnutém spínači.

Druhý pár zajistí spuštění podprogramu pro záznam času.

vypíná DC-DC zdroj

plus vnitřní 9V baterie, nebo napájecí kabel
komunikace RS485 - B

komunikace RS485 - A
minus vnitřní 9V baterie, nebo napájecí kabel

*1 ..... Osadit podle schématu při jen použití dálkové komunikace RS485, jinak neosazovat.
*2 ..... Terminátor pro linku RS485 se osazuje jen na konci sběrnice.
*3 ..... Při použití přídavné vnitřní GPS neosazovat svorky - bude sloužit pro připojení 90° kolíky na desku GPS

9V baterie se v tom případě připojí do dírek na desce GPS. Případná komunikace RS485 se pak také zapojuje do desky GPS.

*4 ..... Při použití přídavné vnitřní GPS provést drátové propojky na spodní straně mezi dírkami D-D'; C- C'; R-R'
*5 ..... Při použití zálohovací baterie se tyto součástky neosazují
*6 ..... Ve verzi se superkapacitorem se zálohovací baterie ani její držák nepoužívají
