astromik/SQM/SQM_verze411/hw/pcb/sqm-dis/schema_dis.pdf

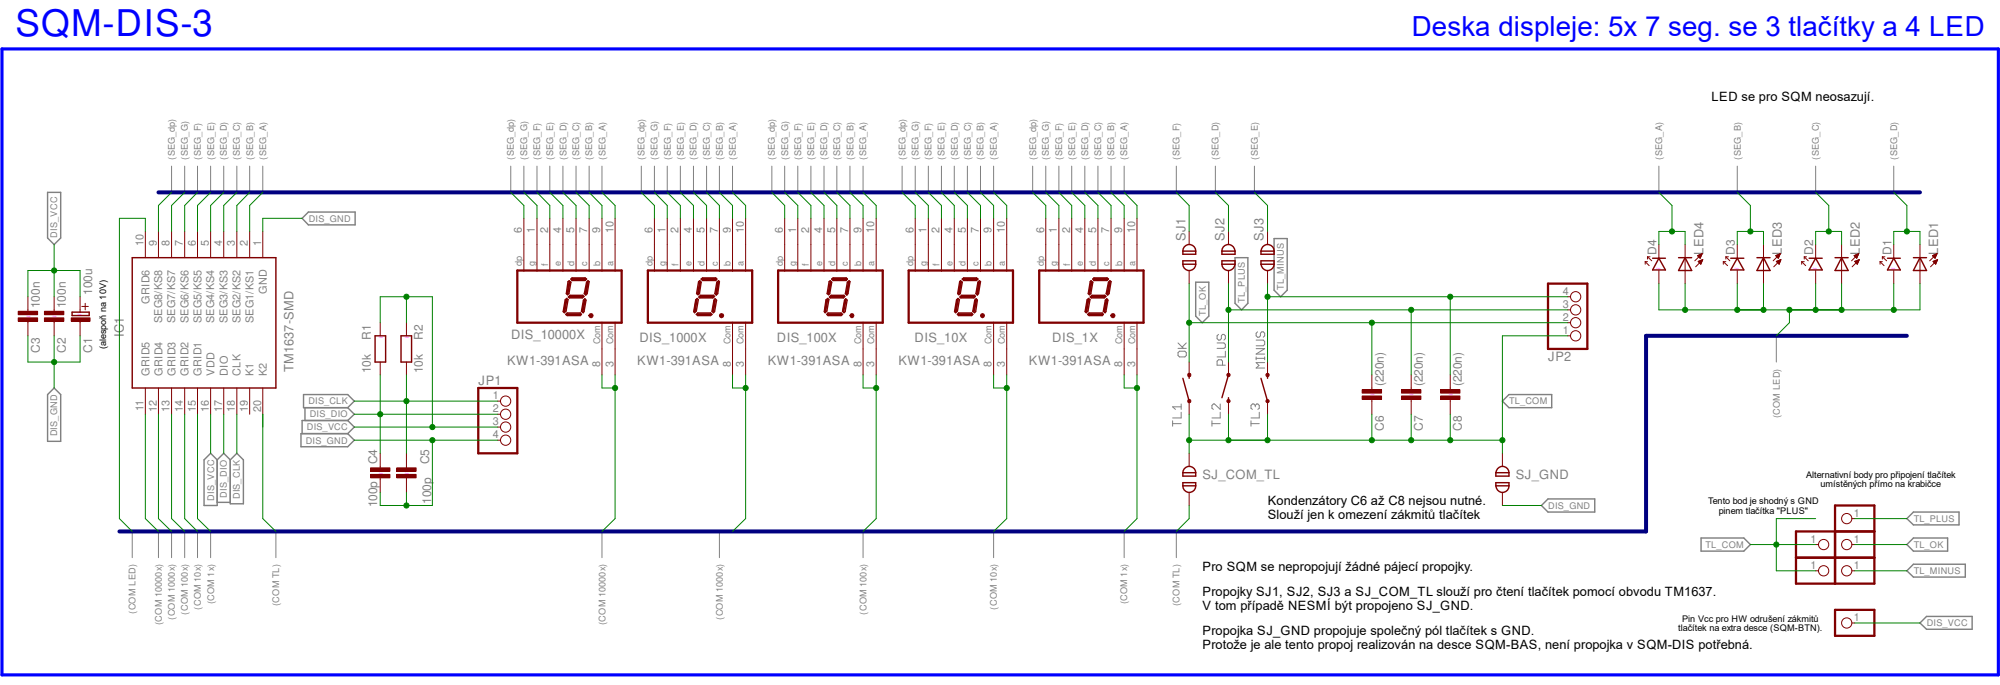
[picture p162: page 1]

LED se pro SQM neosazují.

Alternativní body pro připojení tlačítek
umístěných přímo na krabičce

Kondenzátory C6 až C8 nejsou nutné.
Slouží jen k omezení zákmitů tlačítek

Tento bod je shodný s GND
pinem tlačítka "PLUS"

(COM TL)
Propojky SJ1, SJ2, SJ3 a SJ_COM_TL slouží pro čtení tlačítek pomocí obvodu TM1637. V tom případě NESMÍ být propojeno SJ_GND.

Pro SQM se nepropojují žádné pájecí propojky.

Propojka SJ_GND propojuje společný pól tlačítek s GND.
Protože je ale tento propoj realizován na desce SQM-BAS, není propojka v SQM-DIS potřebná.

Pin Vcc pro HW odrušení zákmitů
tlačítek na extra desce (SQM-BTN).
