astromik/SQM/SQM_verze411/hw/pcb/sqm-gps/schema_gps.pdf

## VCC = 3,3V

SQM-GPS-6 | Vnitřní rozšiřující deska k SQM pro měření GPS souřadnic.

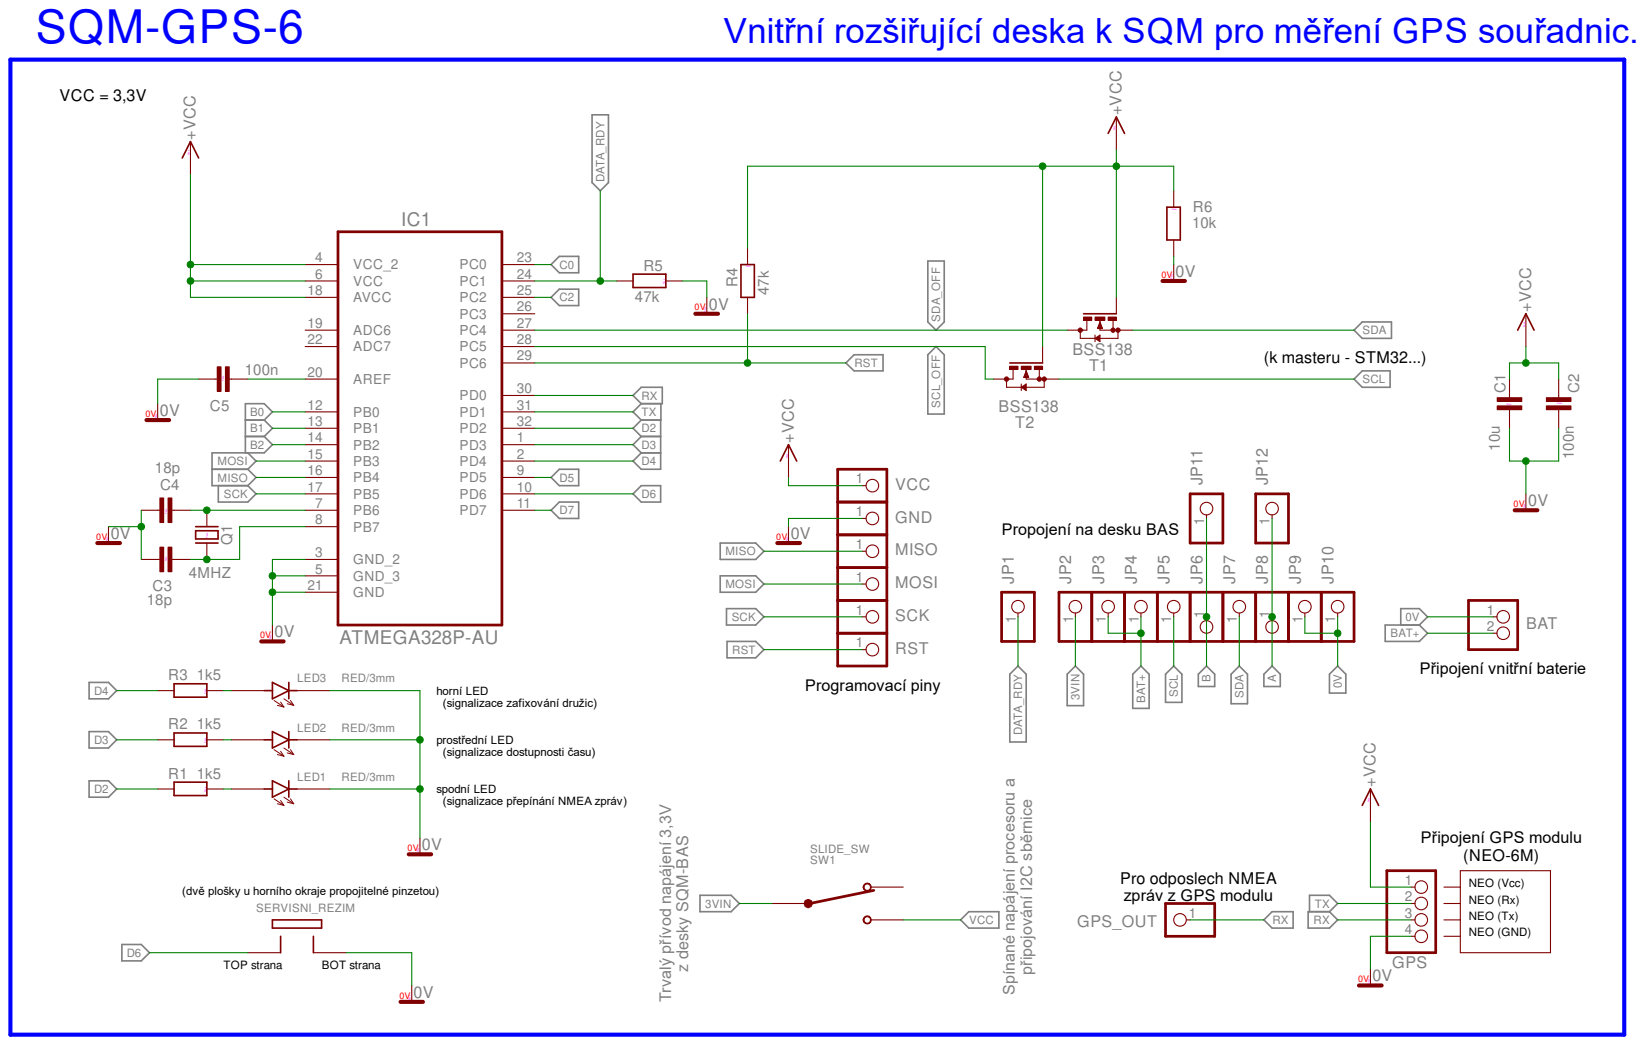
[picture p163: page 1]

Propojení na desku BAS

spodní LED
(signalizace přepínání NMEA zpráv)
