astromik/SQM/SQM_verze411/hw/katalogove_listy/KL-bat_holder.pdf

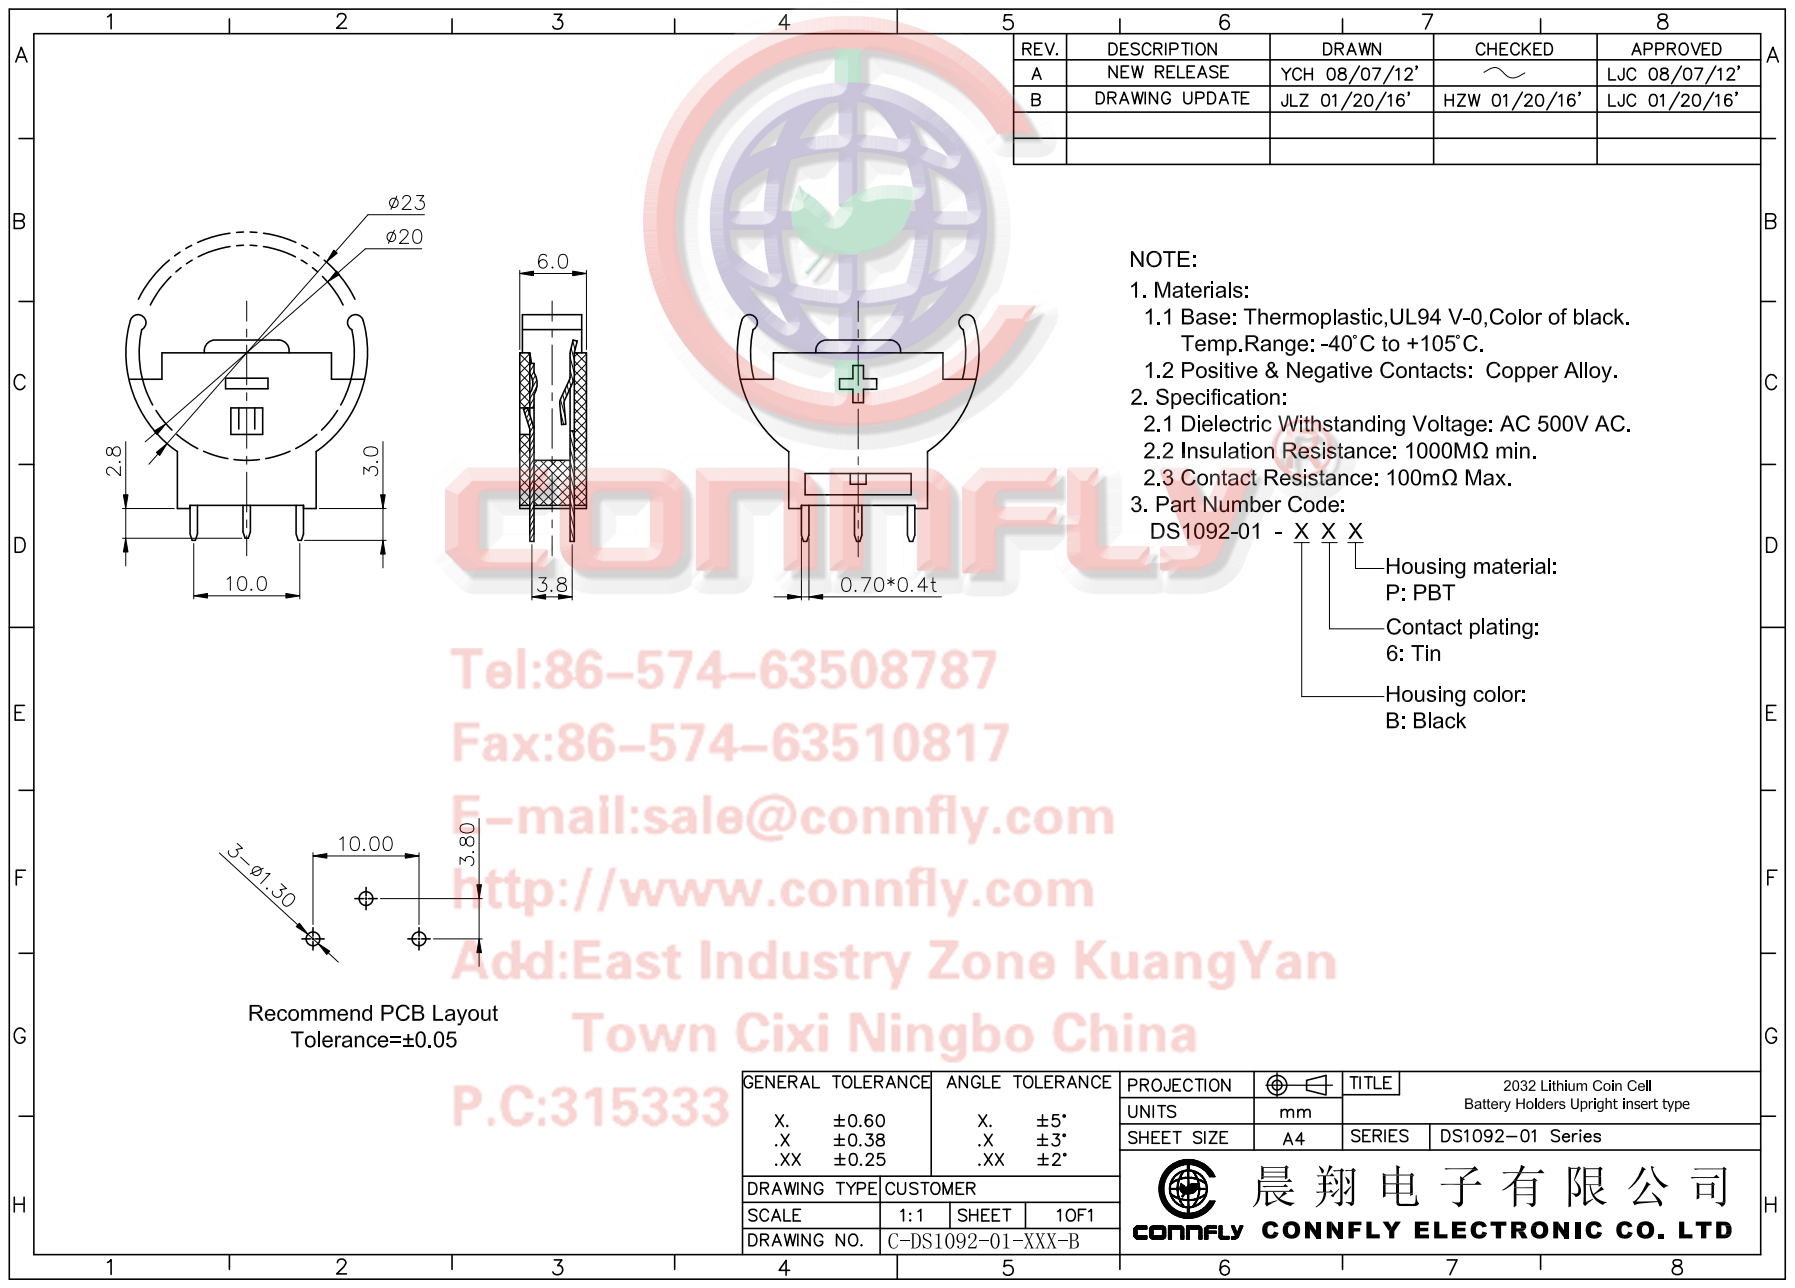
[picture p165: page 1]
