astromik/SQM/SQM_verze411/hw/katalogove_listy/KL-drzak_SD+MCC-SDMICRO3.pdf

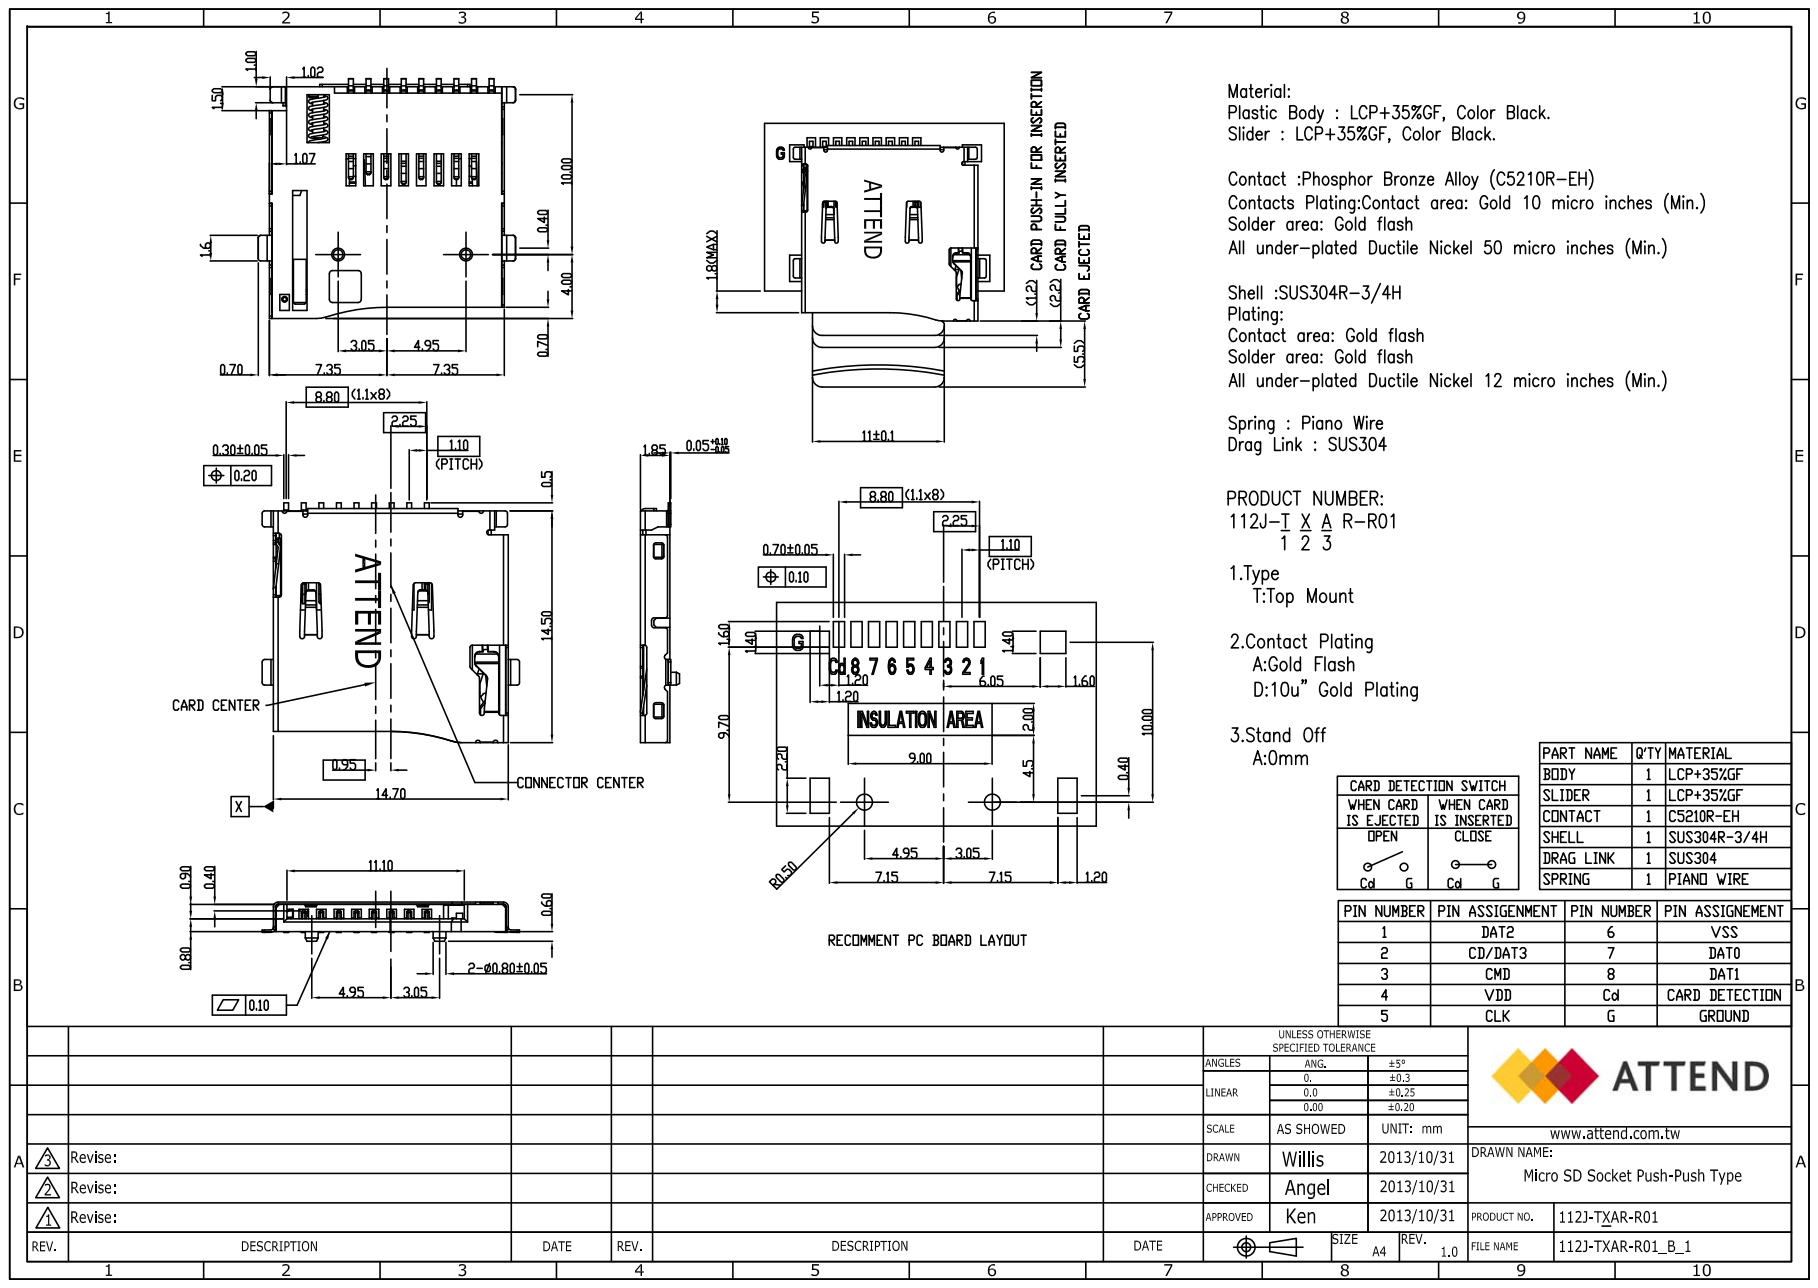
[picture p166: page 1]
