astromik/SQM/SQM_verze411/hw/katalogove_listy/KL-drzak_SD_karty-MCSP-Q1-08-A-SG-TR (20131216)-1.pdf

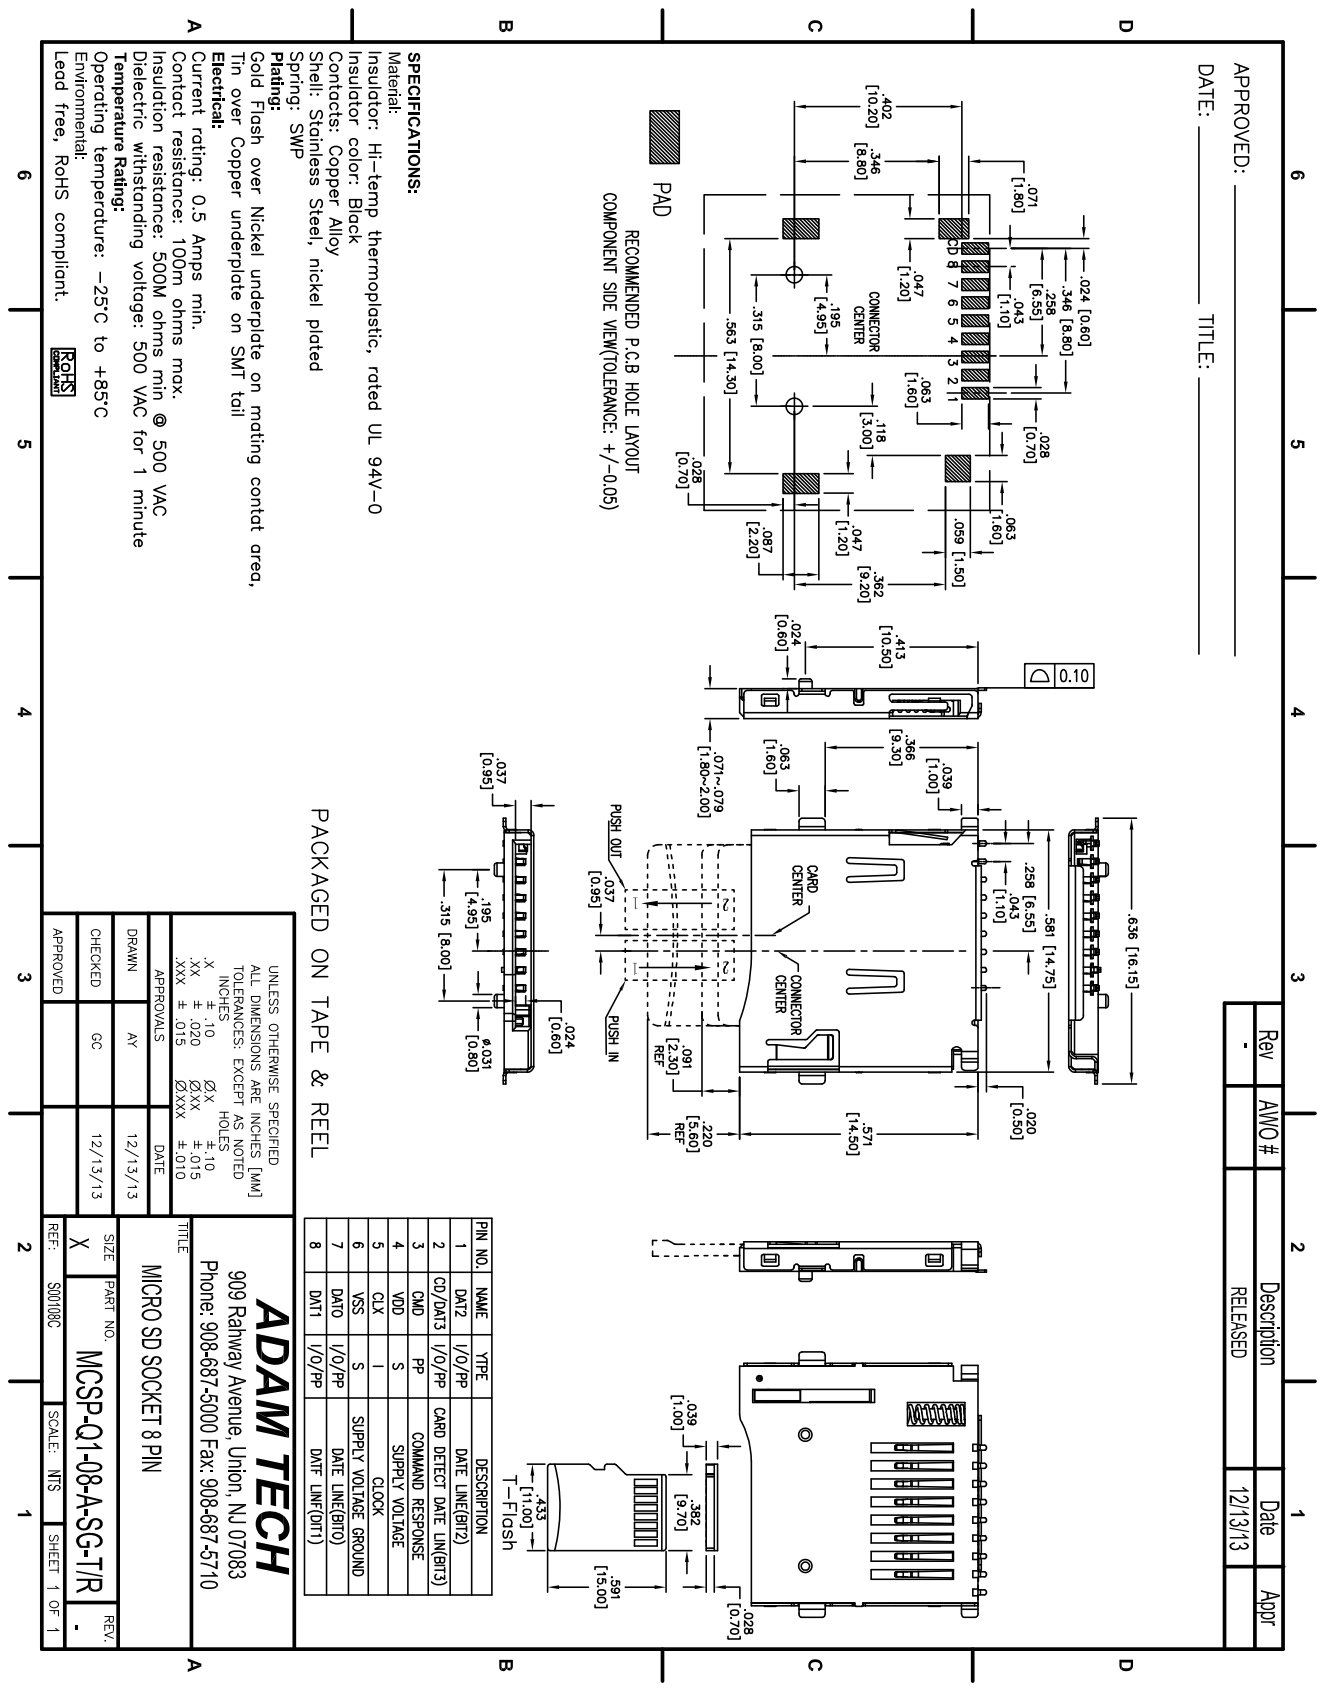
[picture p167: page 1]
