astromik/SQM/SQM_verze411/hw/katalogove_listy/KL-IDC6.pdf

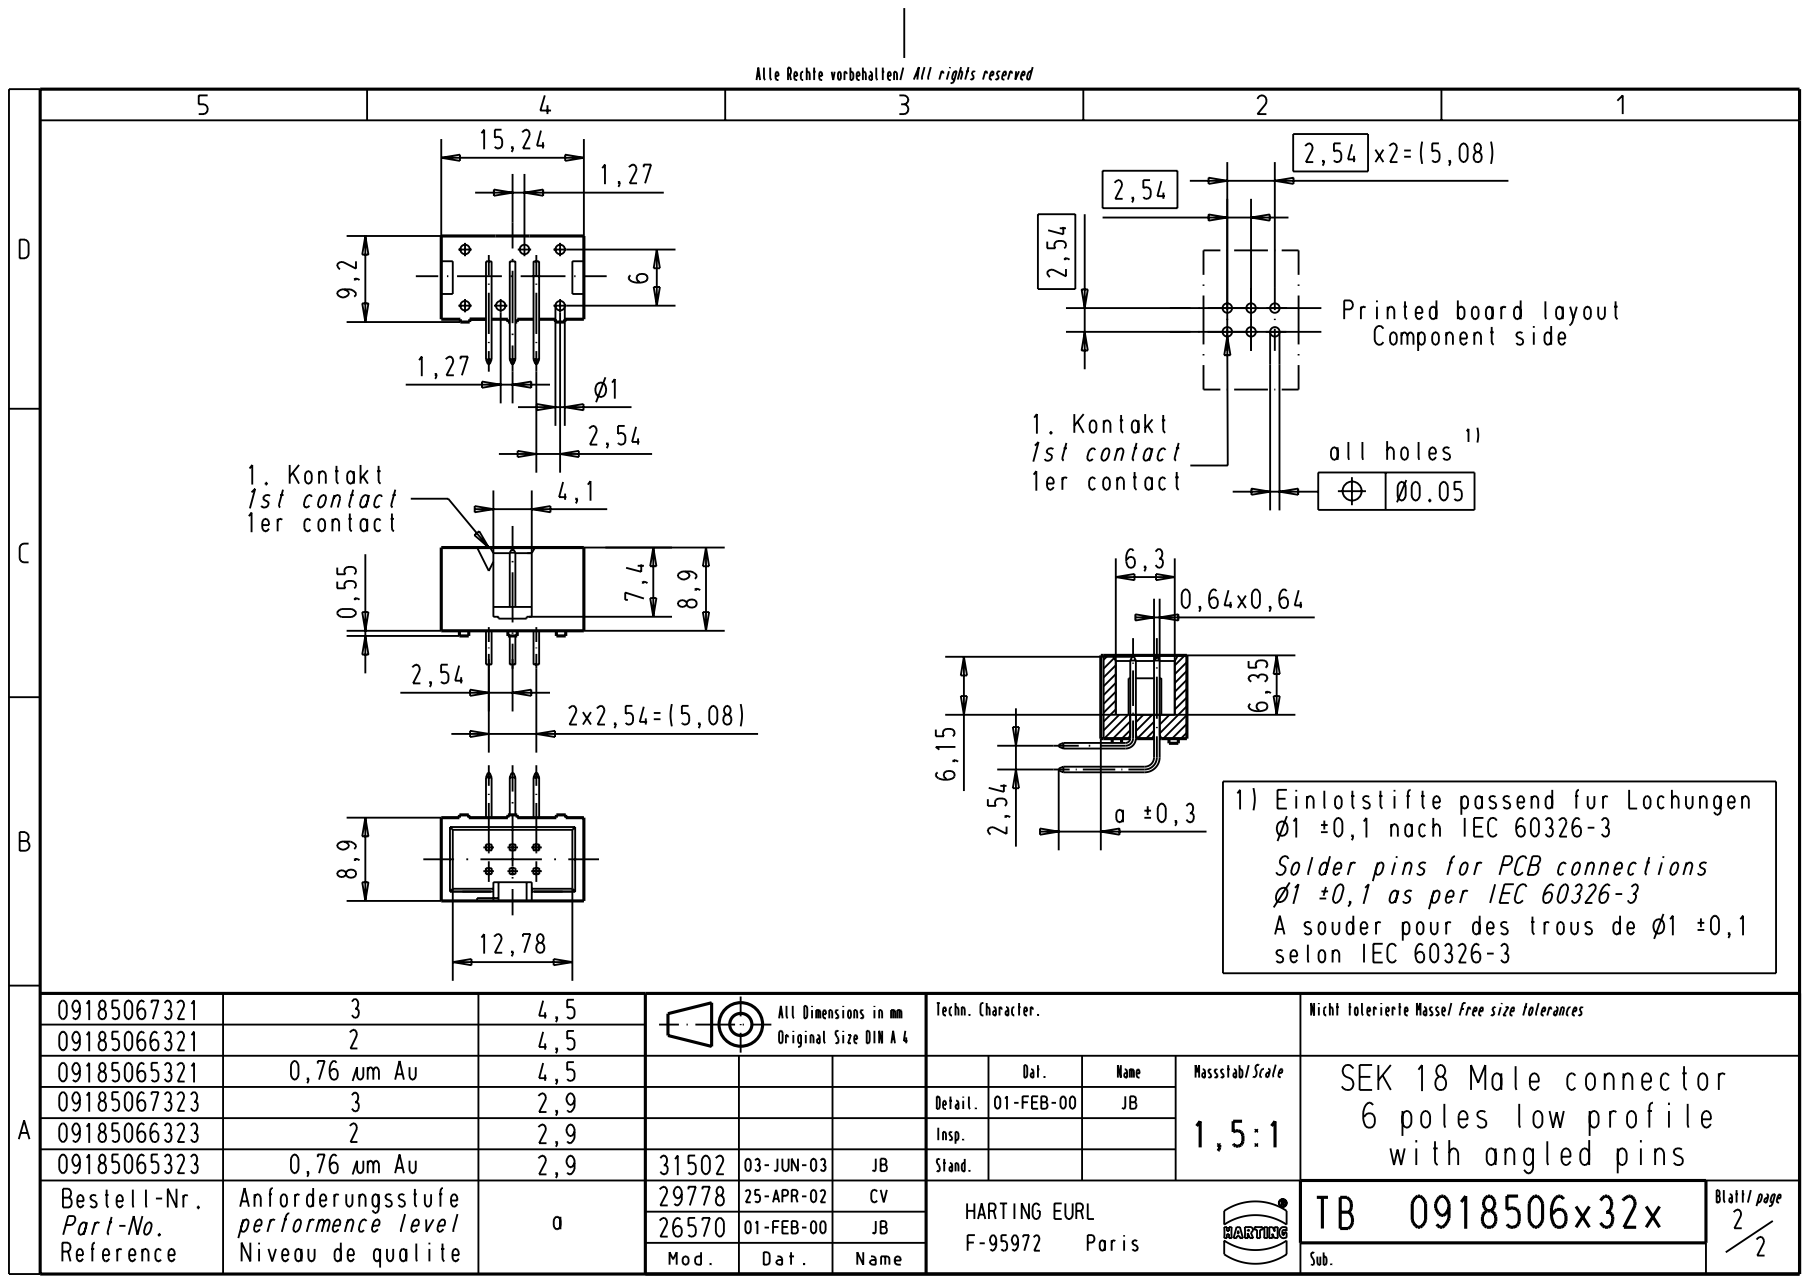
[picture p168: page 1]
