astromik/SQM/SQM_verze411/hw/katalogove_listy/KL-SMD_tlumivka-HPI1040.pdf

# WIFI-ANT405 HPI1040 series

# HIGH POWER INDUCTOR

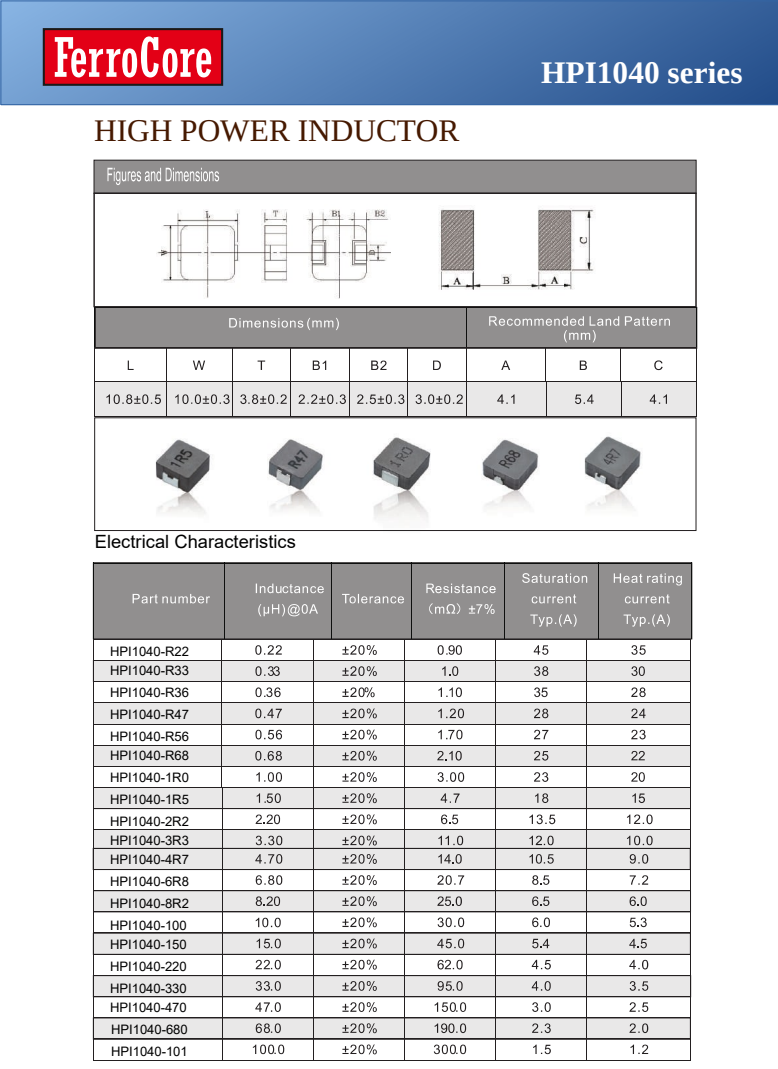
[picture p169: page 1]
Electrical Characteristics

HPI1040-R22
HPI1040-R33
HPI1040-R36
HPI1040-R47
HPI1040-R56
HPI1040-R68
HPI1040-1R0
HPI1040-1R5
HPI1040-2R2
HPI1040-3R3
HPI1040-4R7
HPI1040-6R8
HPI1040-8R2
HPI1040-100
HPI1040-150
HPI1040-220
HPI1040-330
HPI1040-470
HPI1040-680
HPI1040-101

# WIFI-ANT405 HPI1040 series

## Package

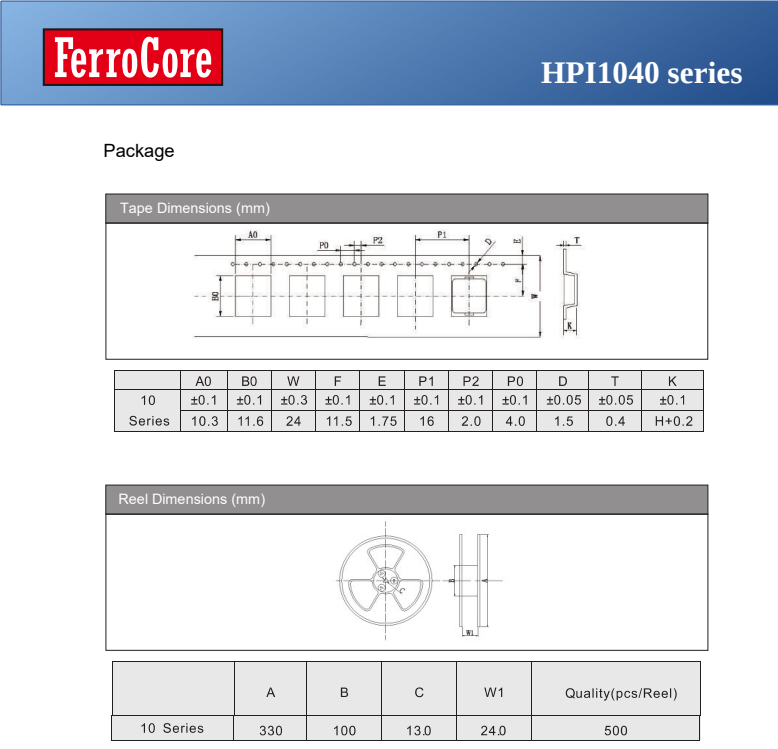
[picture p170: page 2]

Tape Dimensions (mm)

Reel Dimensions (mm)
