astromik/SQM/SQM_verze411/hw/katalogove_listy/KL-USB-B-zasuvka.PDF

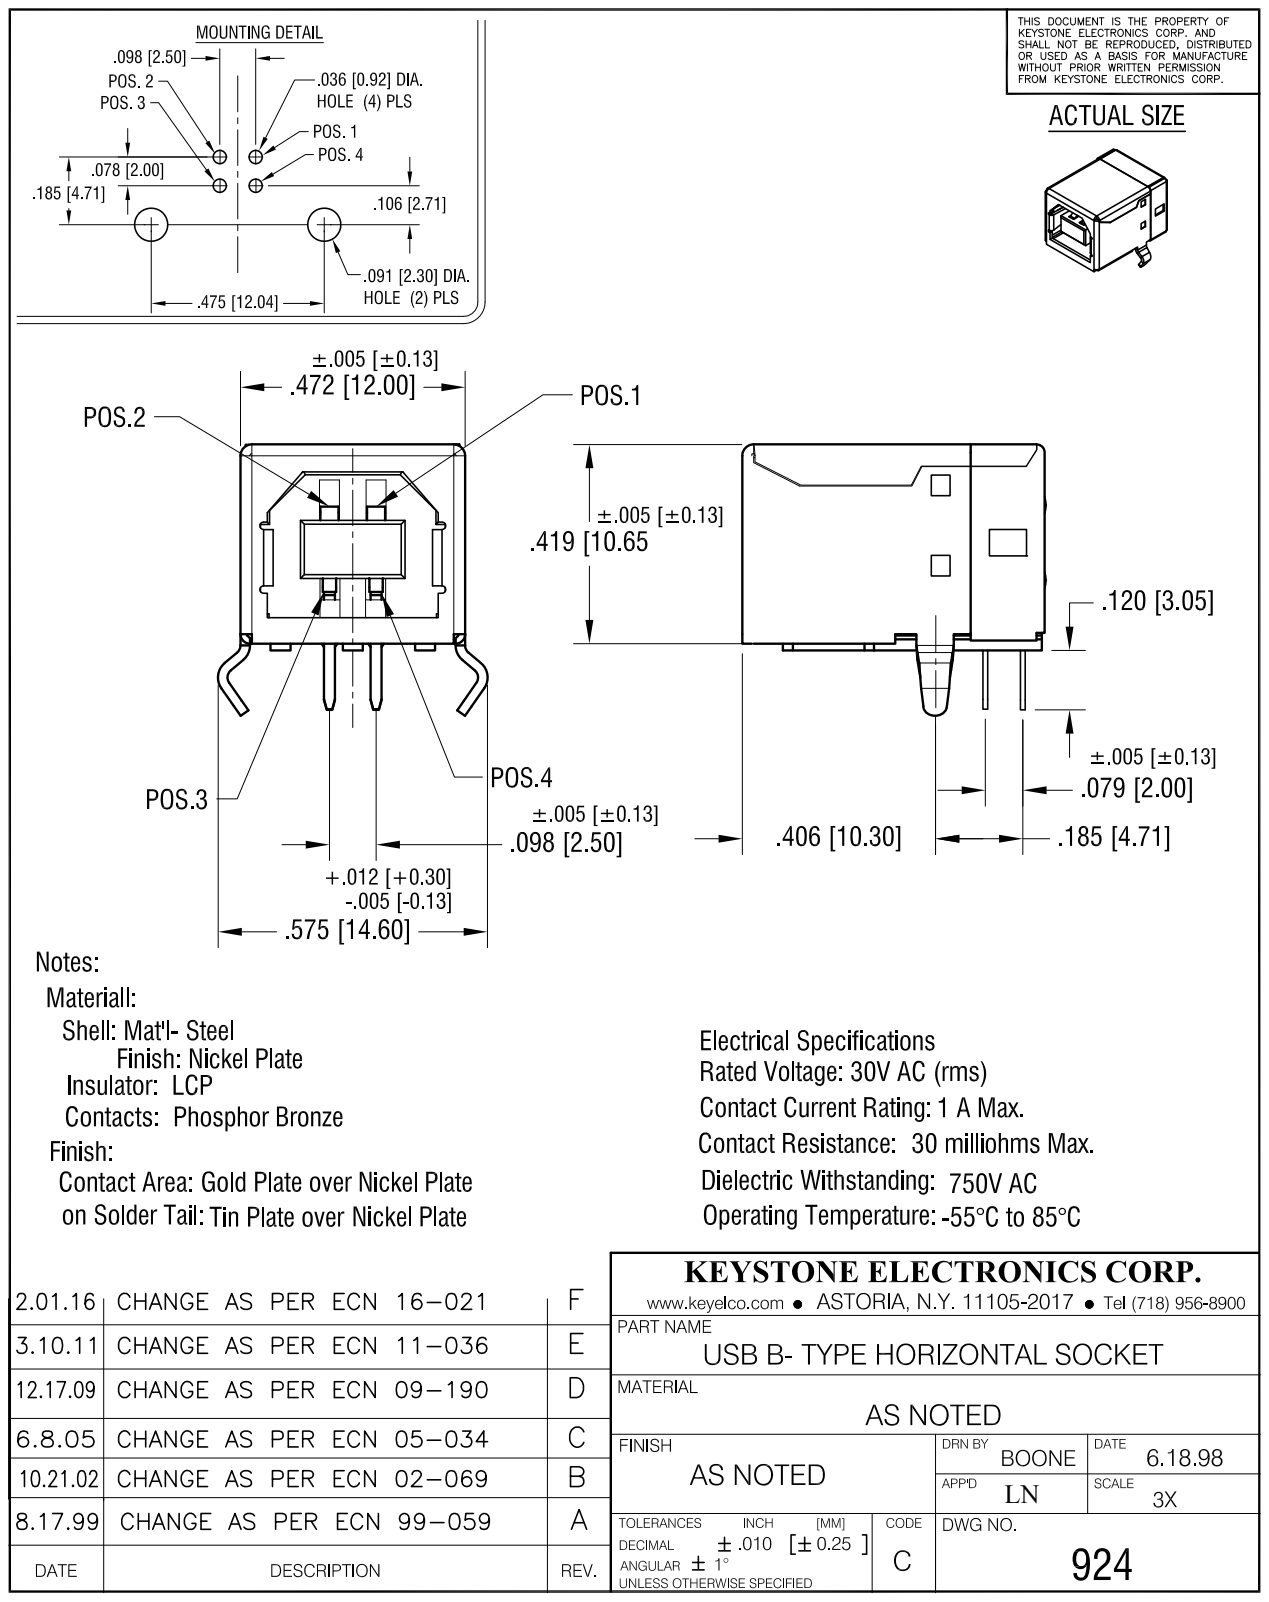
[picture p171: page 1]
