astromik/SQM/SQM_verze411/hw/katalogove_listy/KL-USB-MX-67068-9000.pdf

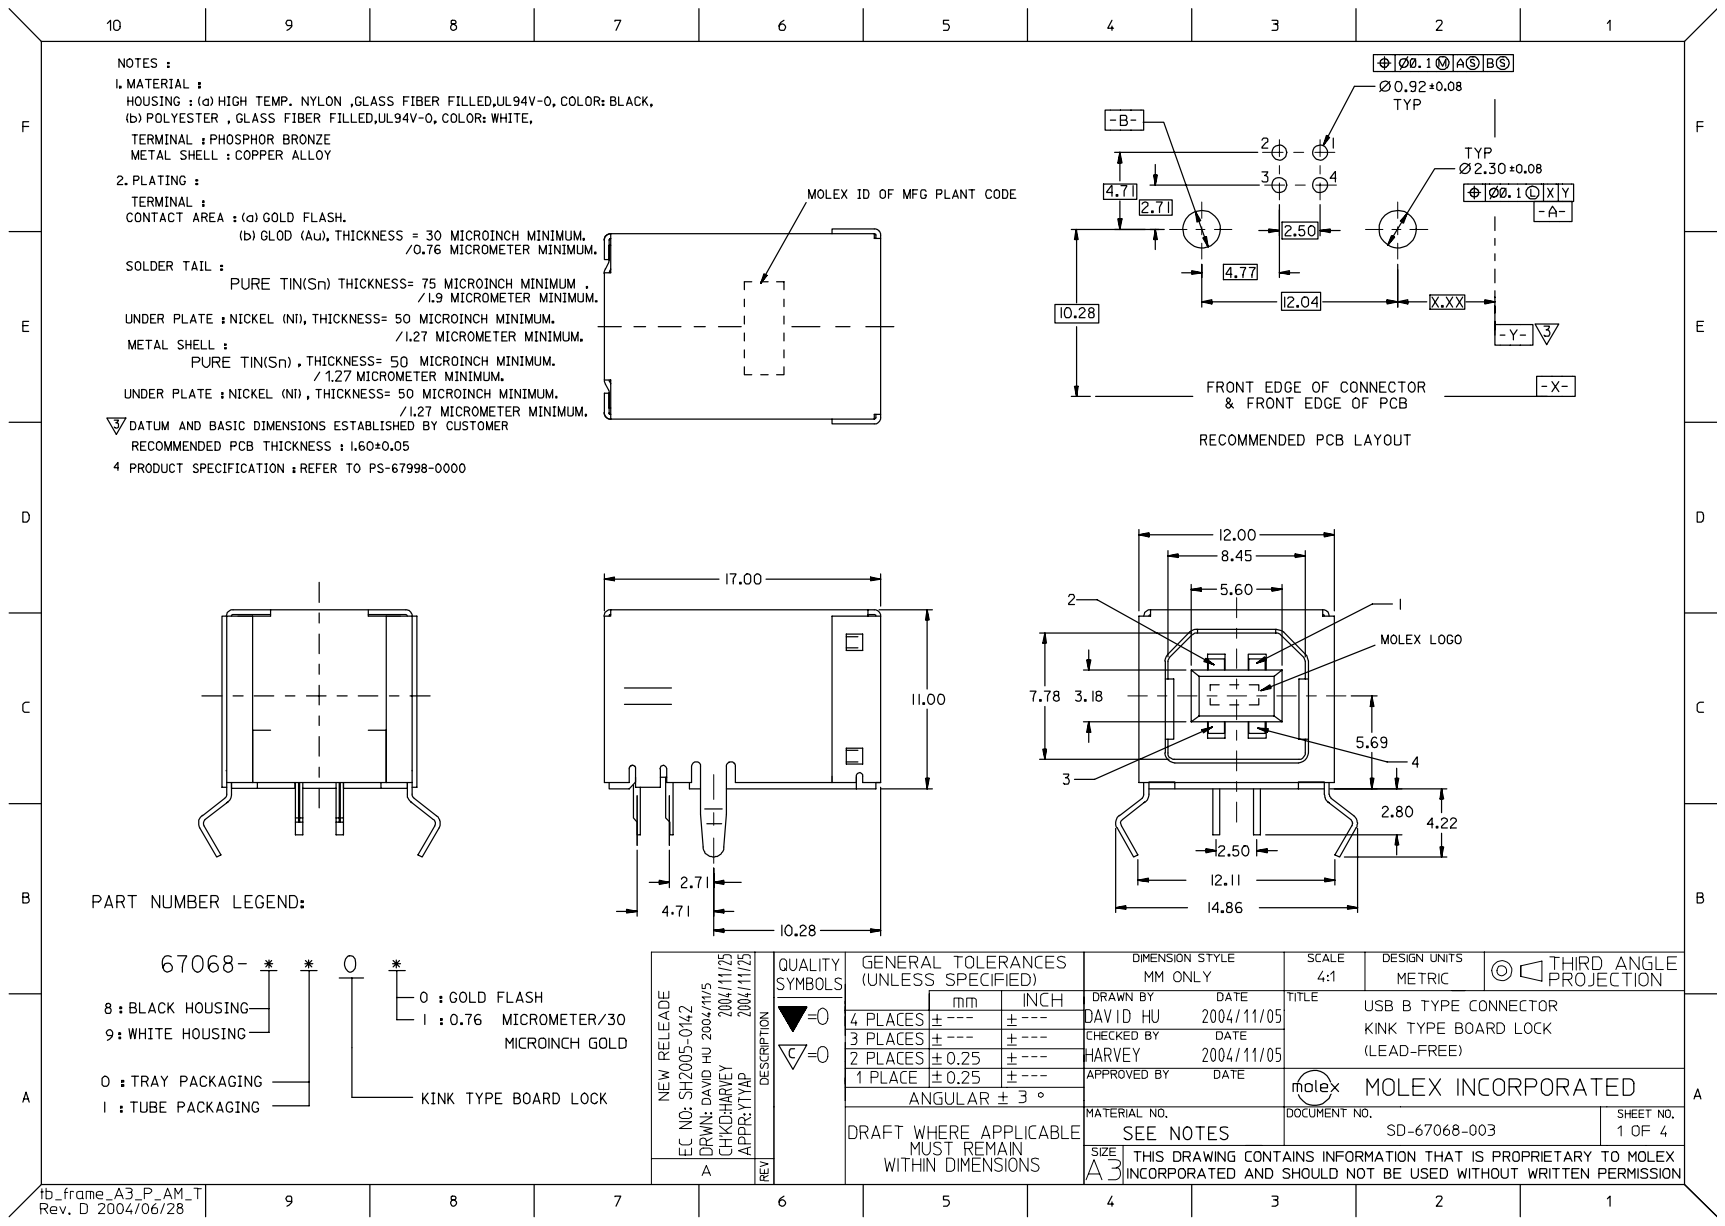
[picture p172: page 1]

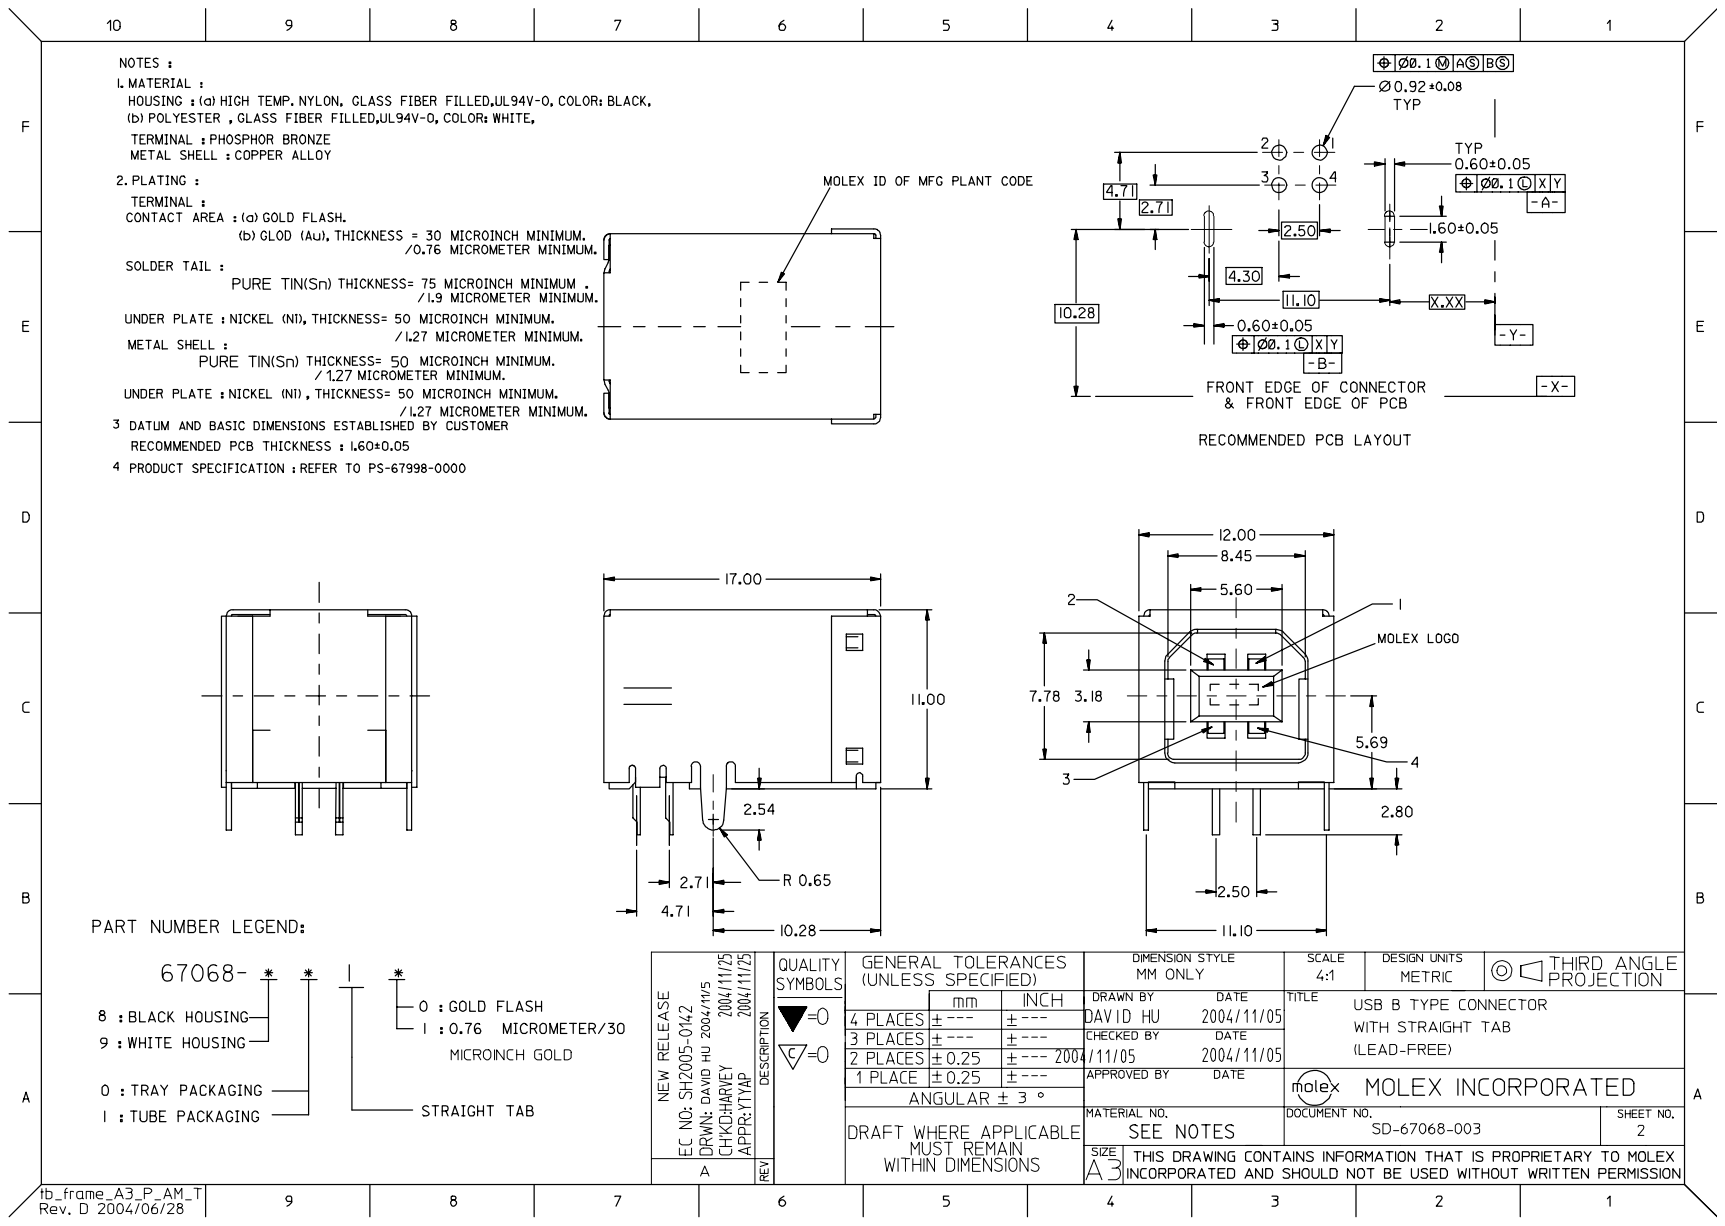
[picture p173: page 2]

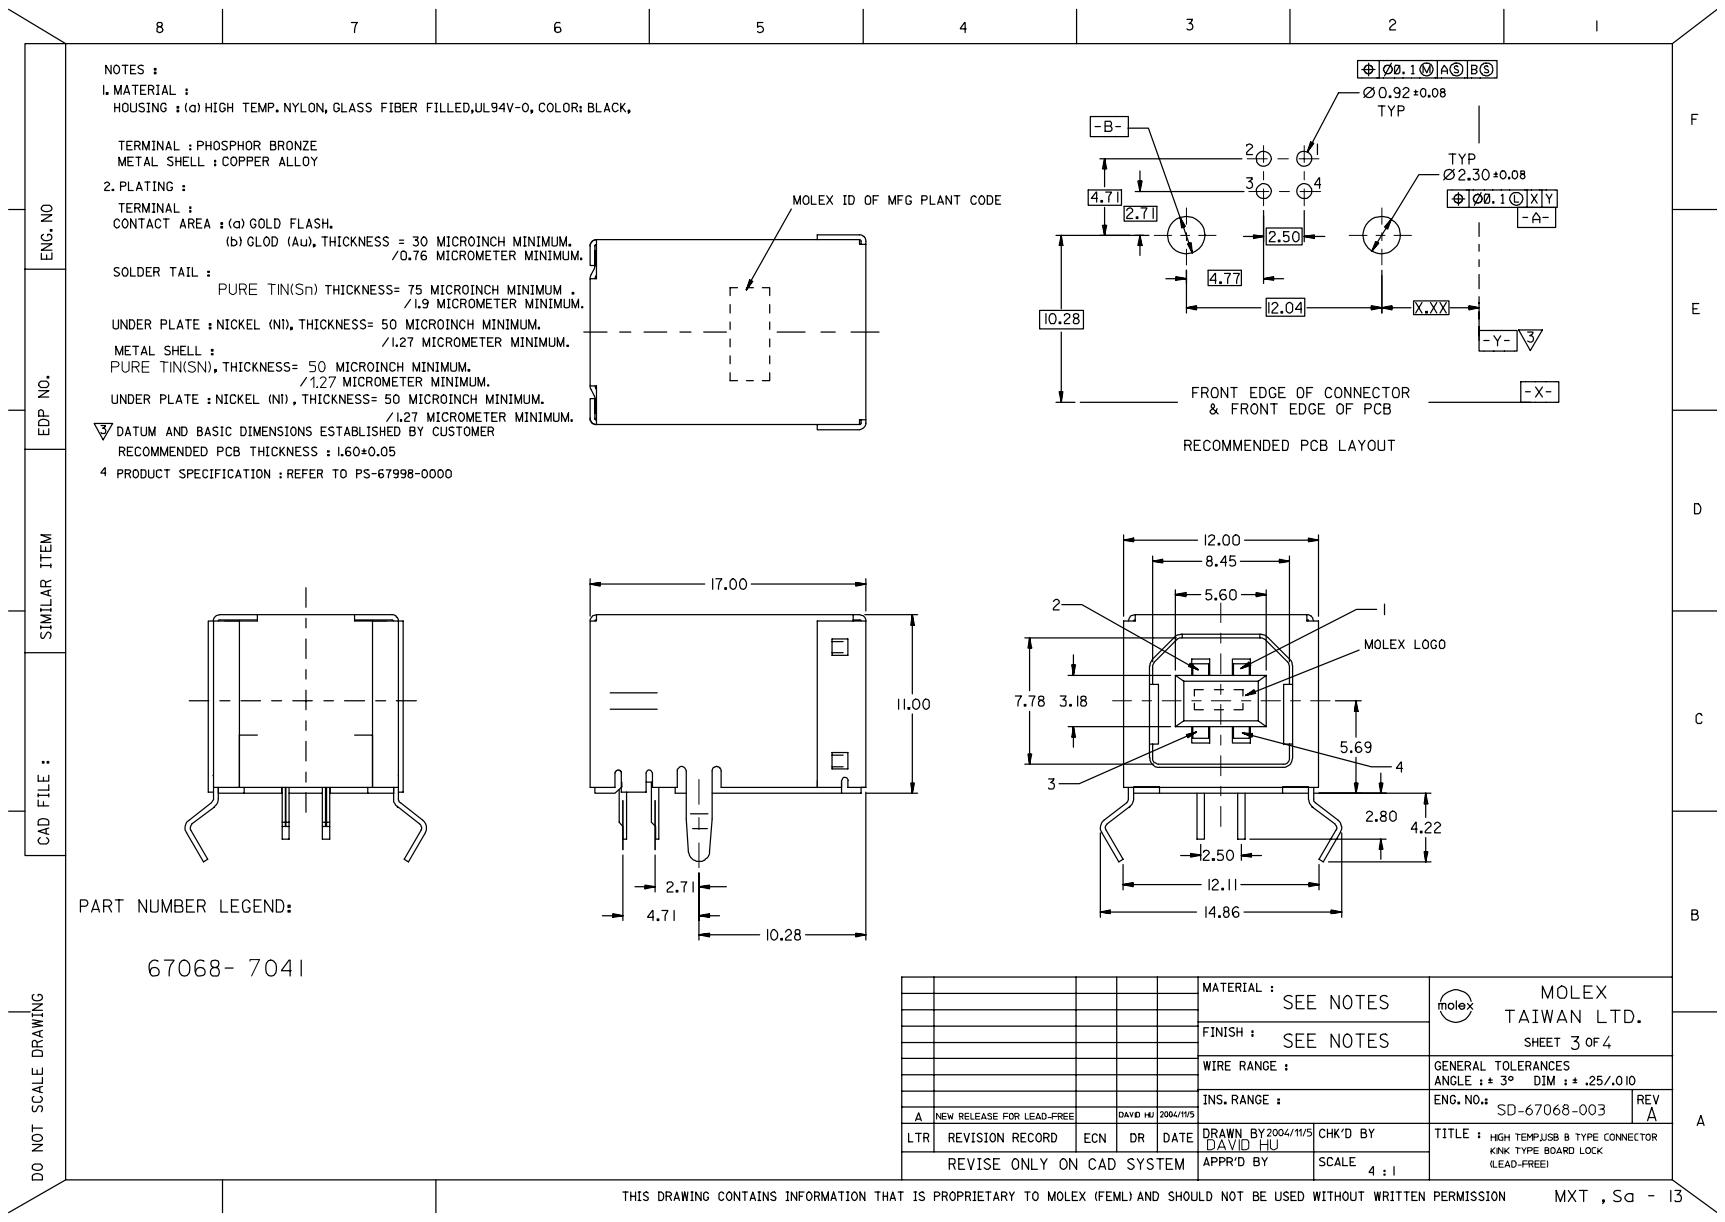
[picture p174: page 3]

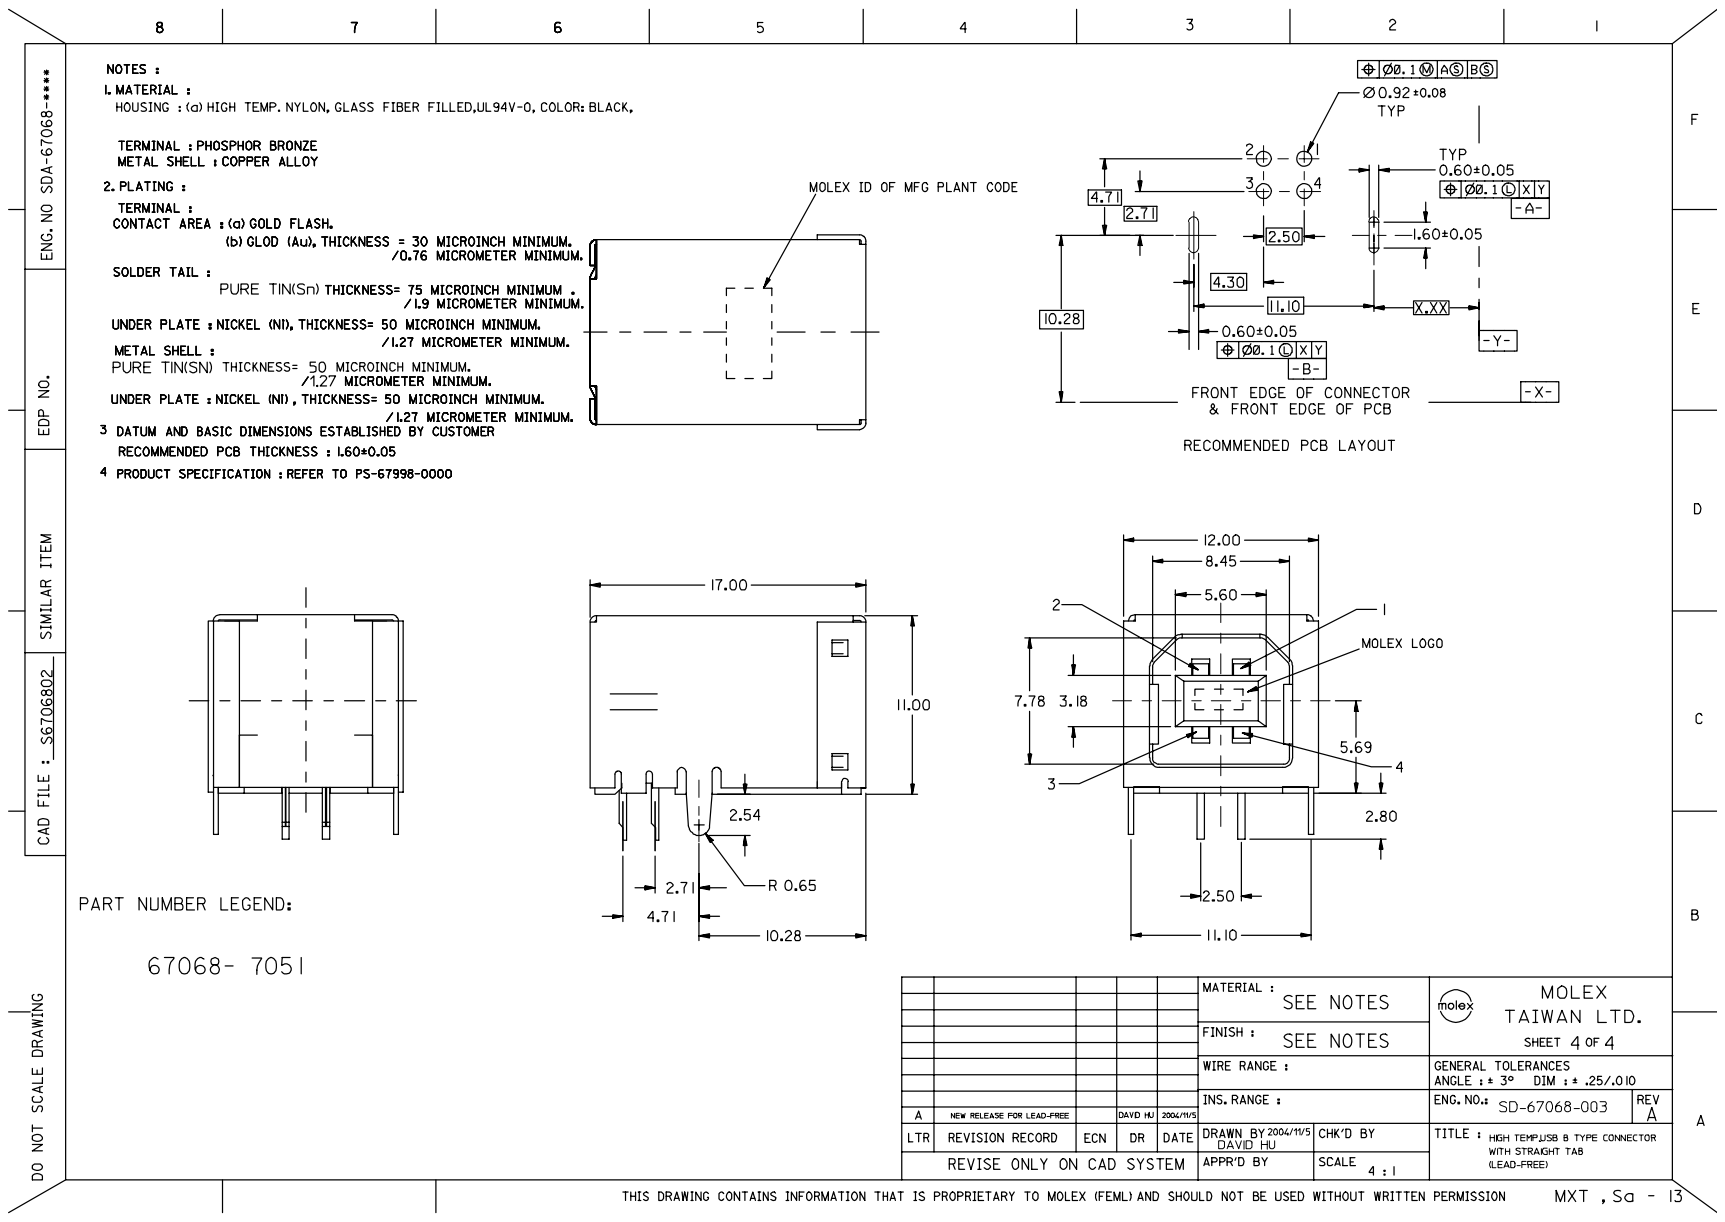
[picture p175: page 4]

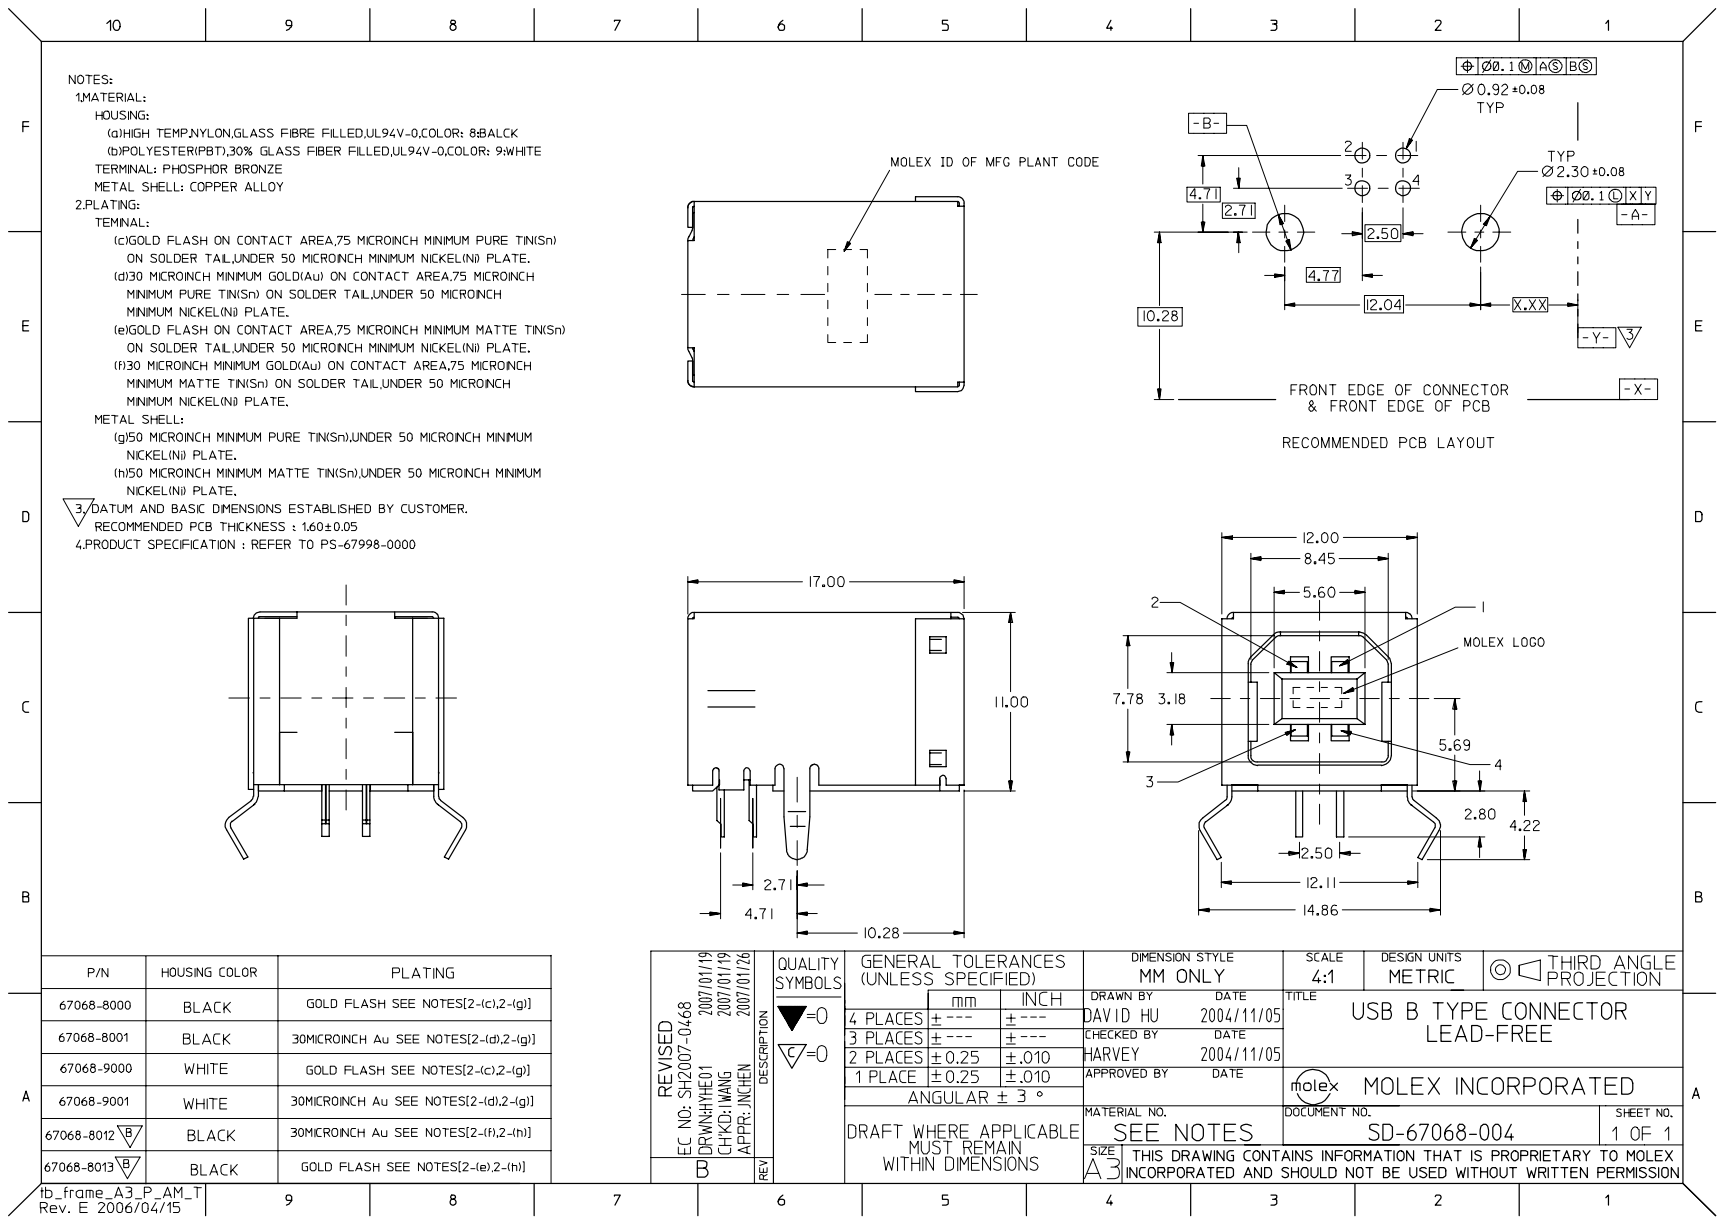
[picture p176: page 5]
