astromik/SQM/SQM_verze411/programy/stm411/stm411.ino

// Amaterske SQM - Sky Quality Meter
//   AstroMiK
//
//
// Detaily (schema, plosnak, navod, fotky):
//           http://sqm.astromik.org
//
#define verzeSW "2026-09-12 (STM32F4x1CEU)"
//        V desce SQM-GPS je nutna verze programu alespon "2026-09-12..INT" (filtrovani GPS souradnic v trackovacim souboru)
//============================================================================
// Odladeno pro Board Manager:
//          https://github.com/stm32duino/BoardManagerFiles/raw/main/package_stmicroelectronics_index.json
//             Pro balik desek "STM32 MCU based boards"
//                by STMicroelectronics verze 2.6.0 !!!
//     V novejsich verzich tam porad neco predelavaji a ja uz nemam silu neustale reagovat na to, ze mi omezuji pouzivane funkce.
//============================================================================


// #doc#01
// Osazene periferie:
//     pokud nejaka periferie neni vubec osazena, nastavi se prislusna promenna na "false"
bool osazeno_DISPLEJ = true;      // pro zobrazeni je pouzity displej
bool osazeno_SD_card = true;      // je osazena SD karta
bool osazeno_BME280  = true;      // je osazene cidlo pro mereni teploty, tlaku a vlhkosti
bool osazeno_LSM303  = true;      // je osazeno cidlo naklonu s kompasem
bool osazeno_r30s    = true;      // je osazena pridavna EEPROM pro rychle (30-sekundove) zaznamy teploty, tlaku a vlhkosti
bool osazeno_DS3231  = true;      // je osazen pridavny RTC obvod pro spousteni SQM i pri vypnutem napajeni
bool osazeno_uref    = true;      // jsou osazeny casti pro mereni napeti hlavniho zdroje
bool osazeno_gps     = true;      // je osazena vnitrni deska SQM-GPS-6


// #doc#02
// pridavna I2C cidla - zatim nepouzita - jen pripravene rezervy - kazde cidlo by mohlo ukladat dva bajty do EEPROM
//   v budoucnu to muze byt vyuzito napriklad na cidlo UV zareni nebo cidlo snehu, vetru ....
//#define cidlo_rezerva_1                                  // cidlo _____
//#define cidlo_rezerva_2                                  // cidlo _____
//#define cidlo_rezerva_3                                  // cidlo _____
//#define cidlo_rezerva_4                                  // cidlo _____


// #doc#03
// vybrat jazyk
#define CZ_language                                      // cestina
//#define EN_language                                    // anglictina jeste neni uplne dokonale prelozena (texty jsou v souboru "jazyky.h")     //!!


// #doc#04
// nastaveni analogovych urovni pro test baterie (meri se za odporovym delicem R7, R8, R6)
//     merici rozsah je 0 az 3,3V a to odpovida cislu 0 az 4095.
//  Uvedene meze vychazi ze skutecne zjistenych hodnot - v priloze je dokument "test_baterie.xls"
#define bat_level_3     620                              // (7V) nad level_3 je vyborny stav baterie                        (blika   1 tecka na displeji)
#define bat_level_2     528                              // (6V) mezi level_3 a level_2 (7V az 6V)je dobry stav baterie     (blikaji 2 tecky na displeji)
#define bat_level_1     441                              // (5V) mezi level_2 a level_1 (6V az 5V) je stredni stav baterie  (blikaji 3 tecky na displeji)
                                                         // pod mezi level_1 (pod 5V)                                       (blikaji 4 tecky na displeji)
#define ref_level      2401                              // kdyz je napajeni tak nizke, ze referencni napeti prekroci tuto uroven, rozblika se vsech 5 tecek


// #doc#05
// V minimalni variante se do EEPROM uklada techto 8 bajtu:
//     1. bajt       - znacka obsazeneho nebo volneho mista, znacka SEC/SELC, index prepnuteho cidla na rozsirujici desce
//     2. az 5. bajt - casovy udaj v sekundach od 1.1.1970
//     6. a 7. bajt  - udaj o namerenem plosnem jasu v tisicinach mag/arcsec2
//     8. bajt       - popis co zpusobilo spusteni mereni (tlacitko, seriova linka, automat, kalibrace), znacka stability mereneho jasu, adresa zarizeni pro komunikaci

// volitelne polozky, ktere se budou ukladat do EEPROM pri kazdem zaznamu (vice polozek znamena, ze se do EEPROM vejde mene zaznamu)
// --- PO ZMENE UKLADANYCH POLOZEK JE NUTNE PROVEST "HARD" FORMAT EEPROM (funkce "#FH" pres seriovou linku) ---
#define ukladat_teplotu             // do EEPROM se bude ukladat informace o teplote                                                           (plus  2 bajty na zaznam)
#define ukladat_tlak                // do EEPROM se bude ukladat informace o tlaku                                                             (plus  2 bajty na zaznam)
#define ukladat_vlhkost             // do EEPROM se bude ukladat informace o vlhkosti                                                          (plus  2 bajty na zaznam)
#define ukladat_infra               // do EEPROM se bude ukladat informace o INFRA slozce svetla                                               (plus  2 bajty na zaznam)
#define ukladat_full                // do EEPROM se bude ukladat informace o FULL slozce svetla                                                (plus  2 bajty na zaznam)
#define ukladat_contr_reg           // do EEPROM se bude ukladat informace o nastaveni Control registru cidla svetla (zesileni, doba snimani)  (plus  1  bajt na zaznam)
#define ukladat_GPS                 // do EEPROM se bude ukladat informace o zemepisnych souradnicich (nutny pridavny hardware)                (plus 10 bajtu na zaznam)
#define ukladat_naklon              // do EEPROM se bude ukladat informace o naklonu (nutny pridavny hardware)                                 (plus  2 bajty na zaznam)
#define ukladat_azimut              // do EEPROM se bude ukladat informace o naklonu (nutny pridavny hardware)                                 (plus  2 bajty na zaznam)
#define ukladat_astro               // do EEPROM se bude ukladat informace o elevaci Slunce a Mesice a o jeho osvetleni                        (plus  3 bajty na zaznam)

// #doc#06
// zatim nepouzita 4 rezervni cidla (z kazdeho cidla bude mozne ukladat 16-bitovou hodnotu)
//#define ukladat_rezerva_1           // do EEPROM se bude ukladat informace o _____ REZERVA 1 ____                                              (plus  2 bajty na zaznam)
//#define ukladat_rezerva_2           // do EEPROM se bude ukladat informace o _____ REZERVA 2 ____                                              (plus  2 bajty na zaznam)
//#define ukladat_rezerva_3           // do EEPROM se bude ukladat informace o _____ REZERVA 3 ____                                              (plus  2 bajty na zaznam)
//#define ukladat_rezerva_4           // do EEPROM se bude ukladat informace o _____ REZERVA 4 ____                                              (plus  2 bajty na zaznam)



// priklad: Pro uplne ukladani vsech polozek bude 1 zaznam dlouhy 44 bajtu. Do 128kB EEPROM se tak vejde asi 2900 zaznamu.
//          Pro minimalni verzi ukladani (uklada se jen nezbytne minimum informaci a svetlo) je jeden zaznam dlouhy 8 bajtu a do stejne EEPROM se tak vejde pres 16000 zaznamu

// #doc#07
#define zobraz_rezervy           0                       // zobrazi nebo skryje rezervni cidla ze "sys_info()" a z textove hlavicky "hlavicka[]"
                                                         // pri hodnote 0 se skryji vsechny 4 rezervy
                                                         // pri hodnote 1 se zobrazi rezerva 1 a ostatni se skryji
                                                         // pri hodnote 2 se zobrazi rezervy 1 a 2 a ostatni se skryji
                                                         // pri hodnote 3 se zobrazi rezervy 1, 2 a 3 a rezerva 4 se skryje
                                                         // pri hodnote 4 se zobrazi vsechno (nic se neskryva)
uint16_t velikost_hlavicky;                              // podle skrytych rezerv rozsiri/smrskne velikost hlavicky a textovyxh zaznamu

#define pocet_polozek_v_menu    29                       // pocet polozek v menu -1  (index nejvyssi polozky) polozky se pocitaji od indexu 0
#define pocet_periferii          4                       // pocet periferii -1 , ktere se daji vypnout v terenu pres specialni hmat OK+TS+PWRon (5 polozek se zadava jako pocet 4)

// #doc#19 - ZRUSENO - Nove se funkce zapina zmenou hodnoty v EEPROM  na adrese 'eeaddr_autokalibrator'
uint8_t pouzivat_kalibrator;                             // Experimentalni funkce pro pridavny kalibrator ktere umozni pri zapnuti napajeni automaticky zmerit smerove charakteristiky cidla a odezvu na ruzne kombinace jasu dvou LED.
bool zrychlena_kalibrace;                                //     Pridavny kalibrator se sklada z procesoru STM32F103 na desce BluePill a serva (pozdeji mozna krokoveho motoru) a komunikuje s SQM pres bocni konektor I2C.
int16_t cyk_uhel;                                        //     Dale obsahuje dve LED (infra a bilou) vzdelene asi 2m od serva, na kterych se da nezavisle nastavit jas.
                                                         //     Kalibracni pripravek ma i displej a ovladaci joystick, pomoci kterych se da smer a jas LED nastavovat rucne.
                                                         //     Rucne nastaveny jas se pak muze snimat originalnim SQM od Unihedronu a porovnavat zmerene hodnoty obou zarizeni
                                                         //     Funkce sice muze zustat trvale zapnuta, ale jejim vypnutim se zkrati cas startu SQM, protoze se nebude muset kontrolovat pritomnost kalibratoru na I2C lince.
                                                         //     Zrychlena kalibrace je pro rychle otestovani smerove charakteristiky cocky s vynechanim mereni tmy, a jen jednou infra urovni. Vynechava se test kombinaci LED


float lux_kal_a, lux_kal_b, lux_kal_c;                   //   kalibracni parametry pro prevod hodnoty z cidla luxmetru na zobrazovanou hodnotu v luxech (zatim vubec netusim, jaky tvar bude mit prevodni krivka)
                                                         //      (v pripade linearniho posunuti budou pouzity pouze 2 parametry, jestli bude nejake prohnuti, pouzije se i treti parametr)
// #doc#08                                                       
#define AGING          0                                 //  pripadne jemne doladeni casovani DS3231

// #doc#09                                                       
#define posun_tlaku         60000                        // kolik Pa se odecita od zmerene hodnoty tlaku, aby se ukladany vysledek vesel do 2 bajtu (0 az 65535)
                                                         //          (obvykla zmerena hodnota je 100000Pa, po odecteni cisla 60000 je vysledek 40000 a to uz se vejde do 2 bajtu)

// #doc#14
#define BAT_USB             130                          // napeti v desetinach voltu, ktere je zmerene pri samostatne zapojenem, plne nabitem 12V akumulatoru
                                                         // pri vyssi hodnote, nez je tady uvedeno, se predpoklada napajeni pres USB, nebo kombinovane napajeni USB + nejaky zdroj
                                                         //  V tom pripade se tato hodnota neuklada pro pristi zobrazeni v "sys_info" do RTC zalohovane pameti.

bool napajeno_z_USB = false;                             //  znacka, jestli je aktualne zapojeny USB kabel (pri hrane true->false dochazi ke zvukove signalizaci)

bool menu_enable[33];                                    // 32 bitu pro zapinani a vypinani jednotlivych polozek v menu
bool perif_enable[17];                                   // 16 bitu pro zapinani a vypinani jednotlivych jednotlivych periferii

uint8_t delka_zaznamu;                                   // podle zvolenych polozek pro ukladani do EEPROM se nize vypocte delka jednoho zaznamu
uint32_t adr_dalsiho_zaznamu;                            // aby nebylo nutne pred kazdym ukladanim do EEPROM hledat volne misto, zapamatuje se do teto promenne adresa pristiho volneho prostoru
uint32_t adr_posl_zaznamu;                               // adresa, kam byl ulozen posledni zaznam (pro jednodussi ziskavani dat z EEPROM)

uint32_t max_zaznam_EEPROM;                              // adresa, na ktere je ulozeny prvni bajt z posledniho zaznamu (vypocitava se z velikosti pouzitelne EEPROM a z delky zaznamu)

// #doc#10
// definice adres v systemove casti EEPROM
char EEPROM_verze[] = "ver:009\r\n";         //  PRI  KAZDE  ZMENE  ROZLOZENI  DAT  V  EEPROM  ZMENIT  VERZI ! nutno dodrzet pocet znaku vcetne CRLF
#define eeaddr_RTC_set                0UL    // (4 bajty)   adresa v EEPROM pro cas posledniho serizeni RTC v sekundach od 1.1.1970
#define eeaddr_RTC_korekce            4UL    // (4 bajty)   adresa v EEPROM s informaci, za jak dlouho se ma pridavat autokalibracni sekunda  
#define eeaddr_leto_zima              8UL    // (1 bit)     adresa v EEPROM se znackou aktualni casove zony (0=zima; 1=leto)
#define eeaddr_oddelovace             9UL    // (5 bitu)    adresa v EEPROM s informacemi o oddelovacich v CSV souborech
#define eeaddr_automat               10UL    // (1 bajt)    adresa v EEPROM s intervalem automatickeho spousteni mereni v minutach
#define eeaddr_prumerovani           11UL    // (5 bitu)    adresa v EEPROM s poctem prumerovani mereni svetla
#define eeaddr_modbus_LED            12UL    // (2 bity)    adresa v EEPROM s informacemi o zapnuti a vypnuti modbusu a LED nebo displejovem menu
#define eeaddr_LED                   13UL    // (1 bajt)    adresa v EEPROM s informacemi o vypinani jednotlivych LED funkci
#define eeaddr_SLAVE_baud            14UL    // (6 bitu)    adresa v EEPROM s informacemi o adrese a rychlosti komunikace
#define eeaddr_CRC_tset_lock         15UL    // (5 bitu)    adresa v EEPROM s informacemi o testovani CRC, blokovani debug zapisu o serizeni casu a blokovani bocniho tlacitka
#define eeaddr_stab                  16UL    // (1 bajt)    adresa v EEPROM s urovni pro urceni nestabilniho jasu
#define eeaddr_pocet_cidel           17UL    // (3 bity)    adresa v EEPROM s poctem cidel svetla na pridavne desce
#define eeaddr_10kB_znacka           18UL    // (1 bajt)    adresa v EEPROM se znackou zaplneni pameti pro zaznamy (zvysuje se po kazdych 10kB zaplneni)
#define eeaddr_uroven_EEPROM         19UL    // (1 bajt)    adresa v EEPROM s urovni svetla pod kterou se uklada zaznam do EEPROM (pri vetsi tme, nez je nastaveno)
#define eeaddr_teplotni_kalibrace    20UL    // (28 bajtu)  adresa v EEPROM s kalibracni tabulkou pro teplotu (2 sloupce * 7 dvojbajtovych hodnot)
#define eeaddr_TS_stanoviste         48UL    // (2 bajty)   adresa v EEPROM se znackou pro nulovani poradi v zaznamech casovych razitek a aktualnim prednastavenym stanovistem
#define eeaddr_svetelna_kalibrace    50UL    // (420 bajtu) adresa v EEPROM s kalibracnimi tabulkami pro svetlo (7 cidel * 2 sloupce * 15 dvojbajtovych hodnot)
#define eeaddr_TS_aktual            470UL    // (1 bajt)    adresa v EEPROM s aktualnim cislem casove znacky 
#define eeaddr_kompas_offset        471UL    // (1 bajt)    adresa v EEPROM s ulozenou hodnotou dokalibrovani kompasu
#define eeaddr_perif_bity           472UL    // (2 bajty)   adresa v EEPROM s informacemi o deaktivovanych periferiich
#define eeaddr_beep_bity            474UL    // (2 bajty)   adresa v EEPROM s nastavenim funkci, ktere jsou signalizovany pipanim
#define eeaddr_elevace_soumrak      476UL    // (1 bajt)    adresa v EEPROM s elevaci Slunce pod horizontem, pri ktere se hlasi uzivatelsky nastavitelny soumrak
#define eeaddr_GPS_track_id         477UL    // (2 bajty)   adresa v EEPROM, do ktere se uklada stav GPS trasovani (bit15) a poradove cislo trasovaciho souboru (bity 14 az 0)
#define eeaddr_GPS_track_interval   479UL    // (1 bajt)    adresa v EEPROM, do ktere se uklada pocet sekund mezi zaznamy do trasovaciho GPX souboru (1 az 255)
#define eeaddr_AUTOkom              480UL    // (1 bajt)    adresa v EEPROM, do ktere se uklada zpusoob automatickeho odesilani dat do seriove linky
#define eeaddr_CALIB_znacka         481UL    // (1 bajt)    adresa v EEPROM s aktualnim cislem kalibracniho souboru (datum se meni kazdy den, ale tato znacka az po 256 kalibracich)
#define eeaddr_MOD_autoupdate       482UL    // (1 bajty)   adresa v EEPROM s volbou pro automaticke nastavovani modbusovych registru po ukonceni mereni
#define eeaddr_bortle               483UL    // (1 bajt)    adresa v EEPROM pomoci ktere je mozne zapnout nebo vypnout zobrazovani polozky "BortL" v menu "Jas" (pro zapnuti je nutne precist upozorneni v navodu)
#define eeaddr_servis               484UL    // (1 bajt)    adresa v EEPROM pouzivana pri vyvoji k ruznym testum a simulacim. Ve verejne verzi nepouzito, ale pro dalsi vyvoj ponechat bez zasahu.
#define eeaddr_GEO_lat              485UL    // (2 bajty)   adresa v EEPROM se zemepisnou sirkou pro astronomicke vypocty
#define eeaddr_GEO_lon              487UL    // (2 bajty)   adresa v EEPROM se zemepisnou delkou pro astronomicke vypocty
#define eeaddr_zima_hod             489UL    // (1 bajt)    adresa v EEPROM s casovym posunem proti UTC pri zimnim case
#define eeaddr_leto_hod             490UL    // (1 bajt)    adresa v EEPROM s casovym posunem proti UTC pri letnim case
#define eeaddr_menu_bity            491UL    // (4 bajty)   adresa v EEPROM s povolenymi nebo zakazanymi polozkami v menu
#define eeaddr_posledni_den         495UL    // (4 bajty)   posledni den, kdy probihal nejaky zaznam. Pouziva se pro vypis posledniho souboru se zaznamy do seriove linky.
#define eeaddr_AfD                  499UL    // (1 bajt)    adresa v EEPROM s hodnotou jasu pro Alarm for Darkness
#define eeaddr_stanoviste           500UL    // (75 bajtu)  adresa v EEPROM s 5 prednastavenymi pozorovacimi stanovisti (10 znaku pro nazev a 5 bajtu pro displejovou grafiku)
#define eeaddr_txt_zony             575UL    // (8 bajtu)   adresa v EEPROM s oznacenim casovych zon v textovem formatu (napr: "SEC " a "SELC")
#define eeaddr_luxmetr              583UL    // (6 bajtu)   adresa v EEPROM s kalibracnimi konstantami pro luxmetr
#define eeaddr_AFD_styl             589UL    // (1 bajt)    adresa v EEPROM s nastavenim chovani AFD
#define eeaddr_autokalibrator       590UL    // (1 bajt)    adresa v EEPROM s moznosti zapinani a vypinani autokalibracnich funkci
#define eeaddr_rezerva_2            591UL    // (8 bajtu)   rezerva v EEPROM
#define eeaddr_test_write           599UL    // (1 bajt)    testovaci zapis na kontrolu, ze EEPROM funguje
#define eeaddr_kompas               600UL    // (12 bajtu)  adresa v EEPROM s kalibracnimi konstantami pro kompas
#define eeaddr_naklon_horiz         612UL    // (6 bajtu)   adresa v EEPROM s kalibracnimi konstantami pro naklonomer (horizontalni poloha)
#define eeaddr_naklon_vert          618UL    // (6 bajtu)   adresa v EEPROM s kalibracnimi konstantami pro naklonomer (vertikalni poloha)
#define eeaddr_alarmy               624UL    // (12 bajtu)  adresa v EEPROM s casy 6 alarmu pro DS3231 (posledni dvojbajt je pro funkci "odpocet").
#define eeaddr_TEST_alarm           636UL    // (1 bajt)    adresa v EEPROM se znackou pro testovaci alarm.
#define eeaddr_DSO_setup            637UL    // (2 bajty)   adresa v EEPROM pro uchovani nastavenych parametru pro vypocet viditelnosti DSO (schopnosti, prumer, ohnisko dalekohledu) - 3x4 bity
#define eeaddr_DSO_prumery          639UL    // (6 bajtu)   adresa v EEPROM pro tabulku prednastavenych prumeru dalekohledu           (3x 2 bajty v [mm])
#define eeaddr_DSO_ohniska          645UL    // (6 bajtu)   adresa v EEPROM pro tabulku prednastavenych ohniskovych delek dalekohledu (3x 2 bajty v [mm])
#define eeaddr_DSO_okulary          651UL    // (5 bajtu)   adresa v EEPROM pro tabulku prednastavenych ohniskovych delek okularu     (5x 1 bajt  v [mm])
#define eeaddr_DSO_normal_MSA       656UL    // (1 bajt)    normalovy jas oblohy pro urcovani viditelnosti otevrenych hvezdokup v desetinach mag/arcsec2
#define eeaddr_rezerva_3            657UL    // (33 bajtu)  rezerva v EEPROM
#define eeaddr_MIN_EEPROM           700UL    // Na jake adrese v EEPROM zacina oblast pro namerena data
#define eeaddr_MAX_EEPROM       0x1FFFFUL    // maximalni mozna adresovatelna bunka v EEPROM  (pro 128k x 8b EEPROM )


#include <Wire.h>                                        // knihovna pro I2C komunikaci
#include <IWatchdog.h>                                   // podpora pro Watchdog
#include "jazyky.h"

HardwareSerial Serial1(PA10, PA9);
#define Serial Serial1                                   // prejmenovani Serial1.xxx na Serial.xxx

#define ID1 (*(uint32_t *)0x1FFF7A10)                    // unikatni identifikace procesoru
#define ID2 (*(uint32_t *)0x1FFF7A14)
#define ID3 (*(uint32_t *)0x1FFF7A18)
char ID_char[] = "xxxxxxxxxxxxxxxxxxxxxxxx\0";

#define VELIKOST_FLASH (*(uint16_t *)0x1FFF7A22)        // velikost PROGMEM v procesoru 

#include <Adafruit_BME280.h>                            // knihovna pro cidlo vlhkosti, teploty a tlaku
Adafruit_BME280 cidlo_BME;                             

#include <STM32RTC.h>
/* Get the rtc object */
STM32RTC& rtclock = STM32RTC::getInstance();


//-------------------
// prevzato z puvodni knihovny pro STM32F103
//  pouziva se pro prevody mezi poctem sekund od 1.1.1970 a strukturovanou promennou nadefinovanou jako 'tm_t'
typedef struct tm_t {
  uint8_t  year;    // years since 1970
  uint8_t  month;   // month of a year - [ 1 to 12 ]
  uint8_t  day;     // day of a month - [ 1 to 31 ]
  uint8_t  weekday; // day of a week (first day is Monday) - [ 0 to 6 ]
  uint8_t  pm;      // AM: 0, PM: 1
  uint8_t  hour;    // hour of a day - [ 0 to 23 ]
  uint8_t  minute;  // minute of an hour - [ 0 to 59 ]
  uint8_t  second;  // second of a minute - [ 0 to 59 ]
} tm_t;


#define SECS_PER_MIN  (60UL)
#define SECS_PER_HOUR (3600UL)
#define SECS_PER_DAY  (SECS_PER_HOUR * 24UL)
#define LEAP_YEAR(Y)  ( ((1970+Y)>0) && !((1970+Y)%4) && ( ((1970+Y)%100) || !((1970+Y)%400) ) )
#define SECS_YR_2000  (946684800UL)

#if !defined(__time_t_defined) // avoid conflict with newlib or other posix libc
  #warning "Using private time_t definintion"
  typedef uint32_t time_t;
#endif

static  const unsigned char monthDays[]={31,28,31,30,31,30,31,31,30,31,30,31}; // API starts months from 1, this array starts from 0

//-------------------



time_t tt;
time_t tt_file;
tm_t mtt;
tm_t mtt_file;
tm_t mtt_EEPROM;



#define pin_SD_CS           PA4                          // CS na SD karte

#define pin_tl_up          PA15                          // ovladaci tlacitka
#define pin_tl_dn           PB3
#define pin_tl_ok           PB4

#define pin_bzuk           PB10                          // pin pro piskak (pasivni)
#define pin_DERE           PB15                          // pin pro prepinani smeru vysilani 


#define pin_dis_CLK        PB12                          // piny pro komunikaci s displejem
#define pin_dis_DIN        PB13

#define pin_NEO            PA1                           // ovladaci pin pro NeoPixel LED

#define pin_karta_IN       PB1                           // pin pro test zasunute karty
#define pin_refu           PB0                           // pin pro referencni napeti pro kontrolu stavu baterie

#define pin_AD_BAT         PA0                           // pin pro testovani napeti baterie
#define pin_TS            PA14                           // specialni pin pro zaznam casoveho razitka (TimeStamp)

#define pin_TEST_HW       PA13                           // spusteni testu bez pripojene komunikace


#define pin_DATA_RDY       PB2                           // pin pro zjistovani pripojeneho EXT zarizeni, nebo dostupnosti dat ve vnitrnim GPS modulu
#define pin_bok_out       PB14                           // pin na bocnim konektoru, ktery se ovlada funkci "Alarm for darkness"


#define pin_SDA            PB7                           // u procesoru STM32F411 se musi nadefinovat, na kterych pinech je komunikace I2C
#define pin_SCL            PB6

#define pin_MISO           PA6                           // u procesoru STM32F411 se musi nadefinovat, na kterych pinech je komunikace SPI
#define pin_MOSI           PA7
#define pin_SCLK           PA5


#define I2C_ADDR_EEPROM_RW_0     0b1010000               // I2C adresa EEPROM pro cteni a zapis dat pro bunky 0 az 65535 (adresovaci piny v LOW)
#define I2C_ADDR_EEPROM_RW_1     0b1010001               // I2C adresa EEPROM pro cteni a zapis dat pro bunky nad 65535  (adresovaci piny v LOW)
uint8_t I2C_ADDR;                                        // podle aktualni adresy zapisovane, nebo ctene bunky se nastavuje I2C adresa EEPROM

#define I2C_ADDR_EXPA    0x20                            // I2C adresa expanderu 0x20 (vsechny adresovaci piny v LOW)
#define I2C_ADDR_GPS     0x17                            // I2C adresa pridavneho modulu pro GPS
#define I2C_ADDR_KALIB   0x33                            // I2C adresa kalibratoru (2 x LED + krokovy motor s procesorem ATmega328)


#define I2C_ADDR_KOMPAS       0b0011110
#define I2C_ADDR_NAKLON       0b0011001
#define  OUT_X_L_A            0x28
#define  CTRL_REG1_A          0x20
#define  CTRL_REG4_A          0x23
#define  CRA_REG_M            0x00
#define  CRB_REG_M            0x01
#define  MR_REG_M             0x02
#define  DLHC_OUT_X_H_M       0x03


// Modbus
#include <ModbusRtu_AstroMiK.h>                         // knihovna pro Modbus komunikaci (upravena puvodni knihovna )
Modbus MBslave(1, Serial2, pin_DERE);                   // ID = 1 (bude dale nastaven), ser.port, ridici pin (pin_DERE)
uint16_t MODdata[111];                                  // tabulka hodnot parametru Modbus
uint8_t stav_MOD = 0;
uint8_t posledni_funkce;
bool pouzit_modbus;                                     // misto puvodni verze predavani dat pres RS485 se muze pouzit klasicky modbus
uint16_t index_posledniho_zaznamu;                      // index posledniho zaznamu se prubezne aktualizuje v modbusovem registru [40040]
uint8_t MOD_autoupdate;                                 // informace, jestli se maji registry 30001 az 30031 nastavovat automaticky po kazdem mereni

uint16_t ser_out_data[31];                              // tabulka hodnot, ktere se odesilaji v uspornem formatu do obsluzneho programu 


bool leto =  false;                                     // letni cas

uint8_t data;
bool open_OK; 

uint8_t prumery;                                        // globalni promenna pro pocet mereni hodnot svetla, ze kterych se vypocte prumer
uint8_t automat;                                        // globalni promenna pro nastaveni intervalu mezi automatickym merenim svetla v minutach (0=automat vypnuty)
uint8_t selc;                                           // globalni promenna pro nastaveni casove zony (0=SEC, 1=SELC)
uint8_t slave_addr;                                     // SLAVE adresa pro komunikaci                     
int16_t list;                                           // listovani v poslednich zmerenych hodnotach
uint8_t hranice_ukladani;                               // hodnota svetla v desetinach mag/arcsec2 pod kterou se nebudou ukladat zaznamy do EEPROM ani na kartu

uint32_t posledni_autospusteni;                         // pomocna promenna pro cas posledniho automatickeho spusteni

char prijato[16];                                       // pole, do ktereho se ukladaji znaky, prijate pres seriovou linku (nastaveni casu, zadost o informace, korekce ....)
uint16_t i;                                             // pomocna globalni promenna pro ruzne smycky

uint8_t prijimaci_pole[16];                             // pole, do ktereho se ukladaji pozadavky od MASTERa pri komunikaci RS485
uint8_t vysilaci_pole[50];                              // pole, do ktereho se pripravuji data k odeslani do MASTERa pri komunikaci RS485

uint8_t dokoncene_mereni = 2;                           // na zacatku mereni se tato promenna vynuluje a po dokonceni mereni (ktere muze trvat treba i 20 sekund) se nastvi zpatky na 2
uint8_t prubeh_mereni;                                  // Kdyz prijde dotaz na posledni namerene hodnoty ( pres seriovou linku RS485), ale mereni jeste nebude ukoncene, odesle se zbyvajici pocet mereni

bool probiha_mereni_svetla;                             // pri rezimu 30s umozni zablokovat konkurencni mereni svetla z menu

uint32_t casova_znacka;                                 // pouzito pro zjisteni doby, jak dlouho se ma ignorovat komunikace pres RS485
uint16_t ignor_cas = 3000;

uint8_t pouzij_CRC;                                     // podle parametru v EEPROM[15] je mozne vypnout kontrolu CRC pri prijmu pozadavku pres RS485
uint8_t index_cidla_svetla = 1;                         // v pripade rozsirujici desky pro vice cidel je v teto promenne ulozene cislo prave aktivniho cidla 1 az 7 - (specialni pripad 0)
uint8_t pocet_cidel_svetla;                             // pocet cidel svetla na expanzni desce

uint8_t afd;                                            // nastavena hodnota "Alarm for Darkness"
uint32_t predchozi_cas_afd = 0;                         // casova znacka predchoziho rychleho testu AFD
bool status_afd;                                        // vysledek porovnani nastavene hodnoty 'afd' a zmereneho jasu pro modbusovy status registr
bool afd_bzuk;                                          // znacka, jestli je povolene nebo blokovane zobrazeni napisu "-AFd-" na displeji a bzukani pri AFD
uint32_t posledni_blik_afd = 0;                         // pri aktivnim AFD muze blikat RGB LED 2x za sekundu
bool afd_log;                                           // do syslogu se odesila prvni spusteni AfD po dosazeni tmy
bool afd_nabito;
uint8_t afd_desetiny;                                   // zmerena hodnota jasu v desetinach mag/arcsec2 zaokrouhlena na desetiny pro zaznam do syslogu
uint8_t afd_styl;                                       // nastaveni chovani AFD

uint16_t JAS_log_full;                                  // pri logovani jasu (pri spustenem menu JAS bez korekce) se nove do logu zapisuji hodnoty obou svetelnych registru a config registr cipu TSL
uint16_t JAS_log_ir;
uint8_t  JAS_log_cnf;

bool int_po_kalibraci;                                  // zvlastni pripad, kdy se do interruptu odskakuje z trvale zobrazene hodnoty po kalibraci pres menu
                                                        //    kdyz v tom pripade dojde k nejakemu podprogramu se signalizaci na displeji, zobrazi se po navratu z interruptu opet zmerena kalibracni hodnota 

uint8_t lap_count;                                      // pocitadlo mezicasu od spusteni stopek (1 az 99)

bool blokuj_TS;                                         // zaznam casove znacky je blokovan az do uvolneni tlacitka (aby pri drzeni tlacitka nebylo mozne neustale ukladani casovych znacek)
bool TS_lock;                                           // znacka, ze je bocni tlacitko zamcene proti nechtenemu sepnuti

uint8_t alarm_bat_pamet = 1;                            // pouzito pro varovne akusticke signaly pri poklesu napeti pod nastavene meze

uint8_t pole_EEPROM[55];                                // globalni promenna, do ktere se pri kazdem mereni ukladaji namerena data. Toto pole se nasledne zapisuje do EEPROM a na SD kartu
uint8_t pole_GPS_I2C[60];                               // pole, do ktereho se stahuji data z GPS modulu pres I2C
uint8_t pole_KALIB_I2C[12];                             // pole, do ktereho se ctou data z pridavneho kalibratoru
uint8_t pole_proudy_kalib[64];                          // sem se stahuji kalibracni proudove udaje z kalibratoru (hodnoty proudu LED pro 0.5, 1, 1.5 ... 10mA)

char pole_GPS_NMEA[] = "$GPRMC,110109.00,A,4926.67723,N,01421.99214,E,0.521,,311220,,,A*72   + nejaka rezerva    @\0";   // pole, do ktereho budou stahovat neupravene NMEA zpravy z GPS modulu

int16_t lat_alt_lon = 0;                                // pro listovani v podmenu "GPS"  (LAT->ALT->LON->trASA a opacne)
bool dorotovano;                                        // znacka, ze rotace souradnic na displeji probehla az do konce a od priste uz se rotovat nebude, ale bude se zobrazovat jen poslednich 5 cifer

uint16_t  int_svetlo;                                   // globalni promenne, ktere uchovavaji posledni zmerene hodnoty
uint16_t  int_teplota;
uint16_t  int_vlhkost;
uint16_t  int_tlak;
uint16_t  int_infra;
uint16_t  int_full;
uint16_t  int_naklon;
uint16_t  int_azimut;
uint32_t  int_luxy;
uint8_t   byte_cnf;
uint32_t  GPS_lat;                                      // prumer z poslednich 10 souradnic (ARITMETICKY PRUMER! - v okoli polu by to mohl byt problem)
uint32_t  GPS_lon;                                      //                                   Aritmeticky prumer s osetrenim zemepisne delky kolem hranice 180 stupnu 
uint16_t  GPS_alt;
uint32_t  GPS_lat_akt;                                  // posledni nezprumerovane souradnice
uint32_t  GPS_lon_akt;
uint16_t  GPS_alt_akt;
uint8_t   GPS_SOG;                                      // logaritmizovana rychlost z registru 'pole_GPS_I2C[20]'
uint8_t   GPS_PDoP10;                                   // informace o kvalite GPS souradnic. Ziskavaji se pres I2C z registru: 'pole_GPS_I2C[17]'
uint8_t   GPS_HDoP10;                                   //                                                                      'pole_GPS_I2C[18]'
uint8_t   GPS_VDoP10;                                   //                                                                      'pole_GPS_I2C[19]'


uint16_t  int_rezerva_1;                                // zatim nepouzita rezervni cidla
uint16_t  int_rezerva_2;
uint16_t  int_rezerva_3;
uint16_t  int_rezerva_4;


uint8_t AUTOkom_export_pole[50];                        // sem do toho prostoru se poskladaji casti zaznamu, ktere se odesilaji v automatickem rezimu do nektere seriove linky
uint32_t AUTOkom_posledni;                              // adresa posledniho zaznamu, s merenim svetla, ktery se bude odesilat pri automatickem odesiani dat do seriove linky (ignoruji se TimeStampy, stopky a kalibrace) 
uint8_t AUTOkom;                                        // konfigurace automatickeho odesilani dat do seriovych linek
uint8_t AUTOkom_linka ;                                 // linka 1 (RS485), nebo 2 (USB) 
uint8_t AUTOkom_format;                                 // format odesilanych dat (0= pole dat; 1= text)
uint8_t AUTOkom_obsah;                                  // obsah odesilanych dat:
                                                        //     0bxxxx0000 - nejzakladnejsi data: datum a cas (bez casove zony, bez DvT) + jas mmag/arcsec2
                                                        //     0bxxxxxxx1 - pridat informace o pocasi (teplota, tlak, vlhkost)
                                                        //     0bxxxxxx1x - pridat detailni informace o jasu (infra / full / config / stabil)
                                                        //     0bxxxxx1xx - pridat detailni informace o naklonu a azimutu
                                                        //     0bxxxx1xxx - pridat detailni astro informace (azimut a elvace Slunce a Mesice + osvetleni)
                                                        //     0bxxxx1111 - odesle uplne cely zaznam (i informace, ktere nejsou pomoci jednotlivych bitu dostupne)



bool senzor_BME;                                        // BME280: cidlo teploty, tlaku a vlhkosti
bool modul_LSM303DLHC;                                  // naklonomer s kompasem LSM303DLHC
bool pouzivat_SD_kartu;                                 // povolene nebo zakazane pouzivani SD karty
bool pouzit_ds3231;                                     // kdyz neni pridavny RTC obvod DS3231 osazeny, blokuji se nektere funkce (I2C, menu, vypisy a zadavani budiku, testy)
bool pouzit_r30s;                                       // kdyz neni osazena extra EEPROM pro rezim 30s, blokuji se nektere funkce

uint16_t peribity_maska = 0b1111111111111111;           // bitova maska, pri ktere se nehlasi varovani na vypnute periferie
                                                        //'1' = ignorovat pripadne neshody, '0' = hlasit periferie, ktere nejsou v EEPROM v '1'
                                                        //          bit4=r30s; bit3=DS3231; bit2=SD karta; bit1=LSM303; bit0=BME
                                                         
uint32_t GPS_temp_time;                                 // pri automatickem mereni se zapnutou a zafixovanou GPS se nenastavuje RTC, ale do zaznamu se pouziva prijaty cas z GPS
bool GPS_RTC_flag;                                      // globalni promenna, ktera signaluzuje, ze se misto casu z RTC ma pouzit cas z GPS ('GPS_temp_time')
bool vnitrniGPS = true;                                 // typ pouzite GPS desky je od verze 2026-08-05 uz jen interni (externi byl zrusen a dale uz se nebude aktualizovat)

uint8_t test_prg_flag = 1;                              // jen pro testovaci ucely - SMAZAT !!--

uint8_t posledni_i2C_prikaz;                            // aby se zbytecne neustale neobnovoval stav LED v GPS modulu

uint8_t         znacka;                                 // znacka, co spustilo mereni (tlacitko, automat , seriova linka) + dalsi info (SLAVE adresa a stabilita svetla)

int16_t pamet_LED_svitilna = 1;                         // az do vypnuti napajeni se v teto promenne uchovavanastaveny jas cervene svitilny (0...zhasnuto az 5...sviti vsech 5 sedmisegmentovek)

// promenne pro pripadnou korekci vnitrniho RTC
uint32_t cas_minuleho_nastaveni;                        // cas predchoziho nastaveni casu v sekundach od 1.1.1970
uint32_t korekce;                                       // po jake dobe se ma pricist nebo odecist 1 sekunda

uint8_t rozhod_stab;                                    // rozhodovaci uroven pro stabilni jas

uint8_t D_pamet[5];                                     // V tomto poli se bitove uchovava aktualni stav vsech rozsvicenych segmentu
uint8_t D_pam_pred_int[5];
uint8_t pozice_tecky;                                   // Pocet desetinnych mist pro zobrazeni cisla (0 az 4) - na pozici 0 ale tecka nikdy nesviti
long posledni_n;                                        // Pri aktualizaci pozice desetinne tecky se znovu zobrazi posledni zadane cislo 

//uint8_t lat_scroll[20];                               // pole, do ktereho se uklada retezec k rotaci na displeji pri zobrazeni zemepisne sirky
//uint8_t lon_scroll[20];                               // pole, do ktereho se uklada retezec k rotaci na displeji pri zobrazeni zemepisne delky
//uint8_t alt_scroll[5];                                // pole, do ktereho se uklada retezec pri zobrazeni nadmorske vysky (tohle nerotuje, ale zachoval jsem podobne nazvy)
uint8_t pom_disp_scroll[30];

int16_t LOC_hod, LOC_den, LOC_mes, LOC_min, LOC_sek;    // promenne, ktere obsahuji aktualni cas v RTC (mistni cas)
uint16_t LOC_rok ;                                      // rok (od 1970)
uint8_t LOC_dvt;                                        // den v tydnu (po ... ne)
uint32_t rokmesden;                                     // rok mesic a den ve formatu yyyymmdd
uint16_t mesden;                                        // mesic a den ve formatu mmdd

bool RTC_SD_DEBUG;                                      // pokud je tato znacka aktivni, budou se pri kazdem nastaveni hodin pres GPS zapisovat do zvlastniho souboru informace o presnosti RTC

int16_t LOC_den_file, LOC_mes_file;                     // promenne, ktere obsahuji datum pro nazev slozky na SD karte
uint16_t LOC_rok_file ;                                 // rok (od 1970)

uint32_t dvouminutovy_bzuk=0;                           // pipani pri alarmu bude trvat maximalne 2 minuty. Sem se ulozi cas, ve kterem pipani zacalo

                  // definice znaku pro displej se spolencou anodou
                  //       0    ,       1    ,       2    ,       3    ,       4    ,       5    ,       6    ,       7    ,       8    ,       9    
uint8_t graf_def[10] = {0b00111111 , 0b00000110 , 0b01011011 , 0b01001111 , 0b01100110 , 0b01101101 , 0b01111101 , 0b00000111 , 0b01111111 , 0b01101111 };

uint8_t pole_citlivosti[4] = {0 , 16 , 32 , 48 };       // stupen citlivosti cidla
int16_t posledni_citlivost = 3;                         // posledni pouzity stupen citlivosti (pouziva se k uychleni mereni svetla pri vice merenich v rade)


uint32_t pole_baudrate[4] = {9600 , 19200 , 38400 , 115200 };      // prednastavene komunikacni rychlosti

// zmena jasu LED neni provadena linearne, ale logaritmicky.
//    (protoze je dobre znatelny rozdil v jasu mezi cisly 3 a 4, ale neni pozorovatelny zadny rozdil v jasech mezi cisly 250 a 251 )
//        stupen jasu             0,   1,   2,   3,   4,   5,   6,   7
const uint8_t logaritmy_jasu[] = {   0,   1,   3,   7,  16,  40, 102, 255};   // 0 = zhasnuto ; 255 = maximalni jas
uint32_t barva_LED = 0;


uint16_t bat_in, bat_3d;
float Vcc, napeti_9V, bat_3V, ref_in; 
int16_t bat_proc;
bool logbat = true;                                     // 5 sekund po zapnuti napajeni se loguje napeti 3V zalohovaci baterie
bool testbat_probehl;                                   // znacka se kazdou 0.8 sekundy nastavuje a kazdou 0.2 sekundy shazuje, aby test baterie probihal jen 1x za sekundu

uint8_t signal_LED;                                     // informace o tom, ktere veci ma signalizovat RGB LED
uint16_t signal_BEEP;                                   // informace o tom, ktere veci se maji signalizovat piskanim

uint8_t err_bit;                                        // globalne dostupna promenna s informacemi o chybach (predava se pak treba pres komunikaci)
                                                        // 0bxxxxxxx1 - chyba I2C
                                                        // 0bxxxxxx1x - chyba pri zapisu na SD kartu
                                                        // 0bxxxxx1xx - neni zasunuta SD karta
                                                        // 0bxxxx1xxx - chyba RTC
                                                        // 0bxxx1xxxx - chyba naklonomeru


bool menu_dis_led;                                      // touto promennou je mozne volit typ menu podle varianty SQM (rucni verze s displejem / trvale nainstalovana verze se signalizacni LED)

bool break_blik;                                        // moznost preruseni vyblikavani dlouheho cisla pomoci LED

uint8_t znacka_listu;                                   // pri vypisu svetla se jeste pred datumem vypise informace o typu zaznamu:
                                                        //   'c' = jeden z 10 kalibracnich vzorku
                                                        //   'C' = prumer vsech 10 kalibracnich vzorku
                                                        //   'u' = spusteno tlacitkem "Up"
                                                        //   'd' = spusteno tlacitkem "Down"
                                                        //   'o' = spusteno tlacitkem "Ok"
                                                        //   'A' = spusteno automatem
                                                        //   'M' = spusteno komunikaci


uint8_t znak_stupen = 32;

uint16_t kal_svetlo[20][2] ;                            // pole kalibracnich hodnot pro svetlo
uint16_t kal_teplota[10][2];                            // pole kalibracnich hodnot pro teplotu
uint16_t kal_serial[20][2] ;                            // pres seriovou linku se nejdriv ulozi prijata data do tohoto pole. Po jejich prekontrolovani se pak prepisou do jednoho z poli kal_teplota[], nebo kal_svetlo[]


//  index pole 100x                                                                                                            111111111111111111111111111111111111111111111111111111111111111111111111111111111111111111111111111122222222222222222222222222222222222222222222222222222222222222222222222222222222222222222222222222223
//  index pole 10x                   111111111122222222223333333333444444444455555555556666666666777777777788888888889999999999000000000011111111112222222222333333333344444444445555555555666666666677777777778888888888999999999900000000001111111111222222222233333333334444444444555555555566666666667777777777888888888899999999990
//  index pole 1x          0123456789012345678901234567890123456789012345678901234567890123456789012345678901234567890123456789012345678901234567890123456789012345678901234567890123456789012345678901234567890123456789012345678901234567890123456789012345678901234567890123456789012345678901234567890123456789012345678901234567890
//                         -------------------------------------------------------------------------------------------------------------------------------------------------------------------------------------------------------------------------------------------------------------------------------------------------------------   
char vystupni_retezec[] = "                                                                                                                                                                                                                                                                                               \0";
// priklad s rezervami    " 00018 ; 000823 ; 1609232363 ; 29.12.2020 ; 08:59:23 ; Ut ;  SEC ; 08881 ; 08,881 ; 01 ; 01 ; komun ;  STABIL  ; 17989 ; 48311 ; 600 ;  428x ; 07196 ; +21,96 ; 05151 ; 051,51 ; 093410 ; +49,457154 ; +120,457156 ; -1234 ; +165.8 ; 123 ;  -45 ;  -27 ;  58  ; 65535 ; 65535 ; 65535 ; 65535 \0";    

char DATCAS_retezec[] = "2022/01/24;18:45:00";          // pomocny globalni retezec pro predavani datumu a casu

uint32_t stisk_time;                                    // pro pocitani delky stisku tlacitka
bool stisk;                                             // pro pociteni delky stisku tlacitka
bool bude_save;                                         // pri opusteni menu tato promenna urcuje, jestli se ma nova hodnota ulozit do EEPROM/(RTC), nebo jestli se nic ukladat nebude 
uint8_t jas_displeje;                                   // globalni promenna pro nastaveni jasu displeje podle posledni zmerene hodnoty svetla

#define AUTOEXITMENU      300000UL                      //  po jake dobe necinnosti v [ms] se menu automaticky opusti (5 minut * 60 sekund * 1000 milisekund)
bool auto_exit_menu;                                    // pri 'true' se okamzite vypadne ze vsech vnorenych podprogramu jakoby se stiskavalo kratce tlacitko OK az do doby vypadnuti do hlavni smycky
uint32_t auto_exit_casovani;                            // po dobehnuti teto promenne na hodnotu udanou v definici AUTOEXITMENU se automaticky vypadne z menu

uint8_t spec_rezim = 0;                                 // podle pripojenych I2C periferii je mozne provozovat zarizeni v ruznych specialnich rezimech //!!(r30s)

uint32_t predchozi_zapis_afd;

bool pole_zobr_menu[33];                                // nastavuje, ktere polozky se budou zobrazovat v menu ([0]=List; [1]=Auto; [2]=zona .... [13]=GPS)
bool prvni_vstup_do_menu = true;                        // pri prvnim vstupu do menu po zapnuti napajeni se hleda nejnizsi zobrazitelna polozka v menu

uint8_t oddelovaci_bajt;                                // obsah EEPROM(9), ktery obsahuje informace o oddelovacich znaminkach pro CSV soubor na SD karte
bool des_carka;                                         // oddelovac desetinnych mist (tecka = false; carka = true)
bool uzavirat_uvozovky;                                 // uzavirat kazdou hodnotu na SD karte do uvozovek
bool vytvaret_hlavicku;                                 // Na zacatek kazdeho souboru na SD karte zapise (nebo nezapise) textovy popis sloupcu
uint8_t oddelovac_polozek;                              // Urcuje znak, kterym se budou oddelovat jednotlive polozky v CSV souboru (mezera, strednik, carka, tabulator)

char oddelovac;                                         // znak pro oddelovani polozek v zaznamech (strednik, carka, mezera, tabulator)
char uvozovky;                                          // znak pro uzavirani polozek do uvozovek (nebo mezera)
char desod;                                             // znak pro oddeleni desetinnych mist (carka, nebo tecka)

uint8_t pocet_bzuku;                                    // Vypinani akusticke signalizace chyby po 5 bzuknutich

int16_t styl_vodovahy;                                  // 0 ... elevace; 1 ... dvouosa vodovaha horizontalne nebo svisle (podle aktualniho uhlu naklonu)
int16_t astro_parametr;
bool stabilni_naklon;                                   // znacka, jesli posledni mereni naklonu vratilo stabilni hodnotu, nebo jestli bylo posledni mereni nestabilni

double GeoLon;                                          // souradnice pozorovaciho mista pro astro vypocty polohy Slunce a Mesice
double GeoLat;

int16_t    astro_UTC_min;
int16_t    astro_UTC_rok;
int16_t    astro_UTC_mes;
int16_t    astro_UTC_den;
int16_t    astro_UTC_hod;
int16_t    casova_zona;

// globalni promenne pro vypocty planet
double pla_i; 
double pla_o;
double pla_p; 
double pla_a; 
double pla_e; 
double pla_l; 
double rads = 1.74532925199433E-02;
double pla_tpi = 6.28318530717958;
double degs = 57.2957795130823;
double globra, globde, globvzd;
int16_t index_planety = 1;                              // po zapnuti se index prvni planety v menu nastavi na 1 (Merkur)
uint8_t elevace_soumrak;                                // jak hluboko musi byt Slunce pod horizontem (ve stupnich), aby se hlasil uzivatelsky nastavitelny soumrak


bool astro_simulace;                                    // pri zapnuti astro simulace v menu "AStro" se pri nastaveni datumu a casu pres menu nezapisuji zadane udaje do RTC
int16_t SIM_hod, SIM_den, SIM_mes, SIM_min;             // Casove promenne pro simulaci vychodu a zapadu planet
uint16_t SIM_rok ;                                    
int16_t SIM_start_hod, SIM_start_den, SIM_start_mes, SIM_start_min;       // Casove promenne pro zadani startu simulace
uint16_t SIM_start_rok ;                                    
bool SIM_leto;                                          // prepinani letni a zimni zony v menu pri zapnute simulaci
                                                        // promenne pouzivane pro simulaci slunecni soustavy a pro zobrazeni udaju pres menu "AStro"
int16_t SIM_azim;                                       // na jakem azimutu dojde k nasledujicimu vychodu / zapadu planety
uint8_t SIM_vyza;                                       //   0=planeta behem pristich 24 hodin nevyjde ani nezapadne, 1=pristi bude vychod, 2=pristi bude zapad
int16_t SIM_zamin;                                      // za kolik minut dojde k vychodu nebo zapadu planety
int16_t SIM_aktel;                                      // aktualni elevace planety
int16_t SIM_aktaz;                                      // aktualni azimut planety
int16_t SIM_aktvz;                                      // aktualni vzdalenost planety
int16_t SIM_cas_h;                                      // vypocteny cas udalosti (hodiny)
int16_t SIM_cas_m;                                      // vypocteny cas udalosti (minuty)
double SIM_aktvzd_presne;                               // vzdalenost Mesice nebo planety bez zaokrouhleni pro dalsi prepocet na procenta
int16_t SIM_osvit;                                      // aktualni osvetleni Mesice v %
double R_mag;                                           // magnituda saturnova prstence (nepresny vypocet)
double P_mag_SAT;                                       // magnituda samotne platety Saturn bez prstencu
bool SIM_break;                                         // pro moznost predcasne ukoncit simulaci Slunce a Mesice

uint32_t si_blik_timer;                                 // na casovani problikavani polozek "Datum", "Cas" a "Zona" jako signalizace zapnute simulace, pri ktere se nastavene hodnoty neukladaji do RTC
bool si_blik_stav;                                      // posledni zobrazena hodnota pri stridavem problikavani ("Si. on" nebo polozka v menu "dAtuM", "CAS", "ZonA")
uint16_t si_blik_cekej;                                 // dynamicka zmena casovani mezi problikavanim napisu "Si. on" a puvodnim nazvem polozky v menu "dAtuM", "CAS", "ZonA"

int16_t astro_noc_konec;                                // pro hledani casu, kdy nastane astronomicka noc (Slunce -18 stupnu pod horizontem)
int16_t astro_noc_zacatek;
int16_t astro_noc_trvani;

int16_t letni_posun;                                    // casovy posun mistni casove zony proti UTC v lete (SELC/CEST = 2) je ulozeny v EEPROM (489)
int16_t zimni_posun;                                    // casovy posun mistni casove zony proti UTC v zime ( SEC/CET  = 1) je ulozeny v EEPROM (490)

char char_zima[5];                                      // 4 uzivatelsky nastavene znaky pro oznaceni zimni casove zony + '\0'
char char_leto[5];                                      // 4 uzivatelsky nastavene znaky pro oznaceni zimni casove zony + '\0'
char char_Xzima[5];                                     // stejne jako char_zima, akorat prvni znak je nahrazen podtrzitkem
char char_Xleto[5];                                     // stejne jako char_leto, akorat prvni znak je nahrazen podtrzitkem

float  Mes_elevace;
float  Slu_elevace;
double Mes_osvit;
float  Mes_colong;
float  Mes_term;
float  Mes_azimut;
float  Slu_azimut;

double P_faze;                                          // po spusteni podprogramu "vypocty_elongace(y, m, d, h, n, index)" se do techto promennych ukladaji vysledky
double P_elongace; 
double P_vzdalenost;
double P_ra, P_de; 
double S_ra, S_de; 
uint8_t   P_east_elo;                                   // vychodni elongace vnitrni planety (Merkur nebo Venuse) = 1, zapadni elongace = 0, pro ostatni planety = 2 (nema vyznam)
double P_mag;                                           // pro Merkur a Venusi je mozne spocitat i magnitudu

double fazovy_uhel;

double dist_SP, dist_ZS;


int16_t zadana_rektascenze;
int16_t zadana_deklinace;
float obecna_elevace;
float obecny_azimut; 

float offset_kompasu;                                   // kvuli spatne nalepenemu kompasu je mozne v urcitem pasmu poopravit sever (-12,8 az 12,7 stupnu)


uint8_t velikost_pole_prumeru;                          // pocet zaznamu v poli azimutu, ktere se budou pouzivat k prumerovani (pri beznem mereni to bude stejna hodnota jako 'prumery')
uint16_t pole_teplot[20];                                // pole, do ktereho se budou ukladat teploty k prumerovani
uint16_t pole_azimutu[20];                               // pole, do ktereho se budou ukladat azimuty k prumerovani
uint16_t pole_naklonu[20];                               // pole, do ktereho se budou ukladat naklony k prumerovani
uint16_t pole_tlaku[20];                                 // pole, do ktereho se budou ukladat atmosfericke tlaky k prumerovani
uint16_t pole_vlhkosti[20];                              // pole, do ktereho se budou ukladat relativni vzdusne vlhkosti k prumerovani


int16_t povoleny_rozptyl_azimutu = 10;                  // hodnota ve stupnich. Konstanta pro vyhodnoceni stabilniho / nestabilniho mereni azimutu
int16_t povoleny_rozptyl_naklonu = 10;                  // hodnota v desetinach stupne. Konstanta pro vyhodnoceni stabilniho / nestabilniho mereni naklonu
bool problem_azimutu;                                   // pri mereni pres menu se v pripade nestabilnich hodnot signalizuje problem


int16_t lux_citlivost;                                  // pro automaticke urcovani citlivosti cidla v rezimu luxmetr
long lux_klouzak[6];                                    // pro klouzave prumerovani poslednich 5 mereni
uint8_t lux_index_klouzak;                              // ukazatel po pole klouzaku pro luxometr

uint8_t bortle_povoleno;

uint16_t index_naklonu;                                 // znacka, kam se v kazdem zaznamu uklada naklon
uint16_t index_azimutu;                                 // znacka, kam se v kazdem zaznamu uklada azimut

uint8_t casovani30;                                     //!! pro spec rezim (r30s) - casovaci interval
uint16_t adrsave30;                                     //!! pro spec rezim (r30s) - dalsi volna bunka v EEPROM
bool blokuj_znacku30 = false;                           //!! pro spec rezim (r30s) - pri zobrazenem menu nebo nejakych jinych informacich na displeji nezobrazuje znacku na prvni segmentovce
uint32_t posledni_zaznam30;                             //!! pro spec rezim (r30s) - cas posledniho zaznamu v milisekundach od zapnuti
bool pauza30;                                           //!! pro spec rezim (r30s) - docasne blokovani zaznamu
uint16_t max_EEPROM30;                                  //!! pro spec rezim (r30s) - kapacita osazene pameti

bool predchozi_data_RDY;                                // jen pro logovani zapnuti vypinace u GPS modulu

bool blokuj_err_i = true;                               // pro hlaseni az kazde druhe chyby I2C (k prvni neosetritelne chybe dochazi pri zapnuti GPS modulu)
uint32_t  cas_odblokovani_err_i;                        // pro zablokovani zobrazeni prvni chyby I2C po delsi dobe nez je 5 sekund bezchyleho provozu

char read_buffer[300];                                  // pro vypis souboru do seriove linky se sem bude nacitat obsah souboru a prubezne zpracovavat

char helpfile_name[] = "HELP/#_#.txt";                  // pro jmena souboru na SD karte s napovedami pro jednotlive funkce

#include <Adafruit_NeoPixel.h>                          // knihovna pro ovladani programovatelne RGB LED
// #doc#16
//Adafruit_NeoPixel strip = Adafruit_NeoPixel(1, pin_NEO, NEO_GRB + NEO_KHZ800);          // moznost prohozeni barev na RGB LED (WS2812D)
Adafruit_NeoPixel strip = Adafruit_NeoPixel(1, pin_NEO, NEO_RGB + NEO_KHZ800);            // moznost prohozeni barev na RGB LED ()


#define SD_CONFIG SdSpiConfig(pin_SD_CS, DEDICATED_SPI, SD_SCK_MHZ(1))
#include "SdFat.h"                                      // nova knihovna pro praci s SD kartou
//#include "sdios.h"
SdFat sd;                                               // pro SD kartu
SdFile soubor;
SdFile log_soubor;

uint32_t posledni_SD_free;                              // kazde dve hodiny se aktualizuje informace o volnem prostoru na SD karte


bool sd_out_err = true;                                 // chyba vysunute SD karty "No-Sd" se hlasi jenom 1x pri startu 
uint16_t SD_volno = 0;                                  // volny prostor na SD karte v [MB]. Aktualizace po kazdem zapnuti, nebo vypisu sys_info().
uint16_t SDkapacita = 0;                                // celkova kapacita SD karty v [MB]. Aktualizace po kazdem zapnuti, nebo vypisu sys_info().

bool aktual_odp;                                        // jen kvuli prubezne 5-sekundove aktualizaci odpoctu pri zobrazenem menu "Alarm" a polozce "Odpocet"

uint8_t vyckavaci_kolecko = 1;                          // pri casove narocnych operacich (uvodni zapis do kalibracni tabulky svetla a teploty) zobrazuje na prostredni segmentovce rotujici kolecko

uint8_t index_kodu = 0;                                 // pri odesilani vsech ovladacich kodu pres seriovou linku (prikaz *f) se na zacatek radky zapisuje jeste ciselny index
char    ovladaci_znak = ' ';                            //  pri odesilani vsech ovladacich kodu pres seriovou linku (prikaz *f) se pred kod zapisuje jeste kod pro sadu znaku ('#','@','*','%')

uint16_t RTC_alarm[7] = {0,1440,1440,1440,1440,1440, 1440}; // az 6 pripravenych casu budiku pro pridavne RTC (v minutach od pulnoci - maximalne 23:59 predem) index [0] se nepocita, index 6 je pro odpocet
uint32_t posledni_time_synchro;                         // cas v DS3231 se 1 za hodinu synchroniizuje podle RTC v STM32F411. V teto promenne je ulozeny cas,kdy k posledni synchronizaci doslo.
uint8_t ds_min;
uint8_t ds_hod;
uint8_t ds_den;
uint8_t ds_mes;
uint8_t ds_rok;
uint8_t ds_sek;

bool blokuj_3231 = false;                               // Pro pripad nejake poruchy DS3231 by se mohla pres I2C neustale ziskavat informace o nahozenem AF.
                                                        //    To by zpusobilo nemoznost ovladani SQM, protoze by se stale hlasil ALARM.
                                                        //    Stiskem vsech 3 tlacitek najednou pri probihajicim alarmu se az do dalsiho resetu bude Alarm Flag ignorovat.

bool kalibruje_se = false;                              // pri kalibraci je mozne okamzite prerusit mereni svetla (nemusi se cekat na uvolneni tlacitek)

bool trackuj = false;                                   // znacka pro spousteni GPS trasovani. Na konci setupu se nastavuje na posledni stav podle EEPROM
uint16_t track_interval;                                // interval v sekundach pro zaznamenavani tracku se bere z EEPROM, ale neni bezne uzivatelsky nastavitelny
uint32_t posledni_zaznam_tracku;                        // cas posledniho zaznamu tracku (pro odpocet nastaveneho intervalu)
bool track_blik_LED;                                    // kdyz je zapnute trasovani, prepina se pri kazdem interruptu stav signalizacni LED
char GPS_track_cesta[] = "TRCK/trck1234.gpx";           // retezec pro vytvoreni cesty k trasovacimu souboru (cislo se pri kazdem spusteni trasovani zvetsuje a zaznamenava do EEPROM)

char cesta[] = "CALB/123-1025.csv";                     // retezec pro konstrukci cele cesty k souboru pro funkce kalibratoru    



//-----------------  globalni promenne pro urcovani viditelnosti DSO objektu
int16_t   DSO_index_podmenu = 0;                        // pamatovak pro posledni pouzitou polozku podmenu DSO, aby bylo kam se vracet kratkym stiskem OK (po resetu 0=Messierovky)

uint16_t  DSO_posledni_messier = 1;                     // pro funkci menu "DSO": pamet pro posledni zvoleny index DSO z katalogu Messierovek (nula neni pouzita)
uint16_t  DSO_posledni_ngc = 0;                         // pro funkci menu "DSO": pamet pro posledni zvoleny index DSO z katalogu NGC
uint16_t  DSO_posledni_ic  = 0;                         // pro funkci menu "DSO": pamet pro posledni zvoleny index DSO z katalogu IC
uint8_t   DSO_index_prumeru;                            // pro funkci menu "DSO": nastaveni indexu prumeru objektivu (odkaz do tabulky 'DSO_pole_prumery_dalekohledu[]') - uklada se do EEPROM
uint8_t   DSO_index_ohniska_dalekohledu;                // pro funkci menu "DSO": nastaveni indexu delky hlavniho ohniska (odkaz do tabulky 'DSO_pole_delky_dalekohledu[]') - uklada se do EEPROM
uint8_t   DSO_index_ohniska_okularu = 0;                // pro funkci menu "DSO": nastaveni ohniska okularu  (odkaz do tabulky 'DSO_pole_ohniska_okularu[]') - startuje se vzdycky prvnim typem (index 0) - neuklada se do EEPROM

uint16_t  DSO_pole_prumery_dalekohledu[3];              // prevodni tabulka mezi indexem prumeru dalekohledu [0] az [2] a skutecnym prumerem v [mm]
uint16_t  DSO_pole_delky_dalekohledu[3];                // prevodni tabulka mezi indexem hlavni ohniskove vzdalenosti dalekohledu [0] az [2] a skutecnou vzdalenosti v [mm]
uint8_t   DSO_pole_ohniska_okularu[5];                  // prevodni tabulka mezi indexem ohnoskove vzdalenosti okularu [0] az [5] a skutecnym ohnoskem v [mm]

float     DSO_zornice_mm = 7.0;                         // konstanta pro vypocet dalekohledu - zornice oka v mm (typicky 7 mm ve tme)
float     DSO_zvetseni = 0.0;                           // Vypocty pro dalekohled: zvetseni (pomer ohniska dalekohledu a okularu)
float     DSO_vystupni_pupila = 0.0;                    // Vypocty pro dalekohled: vystupni pupila
float     DSO_delta_SB = 0.0;                           // Vypocty pro dalekohled: zmena povrchove jasnosti v mag/arcsec^2 pro nastavene parametry dalekohledu

uint16_t  DSO_prumer_dalekohledu;                       // Posledni zvoleny prumer dalekohledu v mm
uint16_t  DSO_delka_dalekohledu;                        // Posledni zvolena ohniskova delka dalekohledu v mm
uint8_t   DSO_delka_okularu;                            // Posledni zvolena ohniskova delka okularu v mm
uint8_t   DSO_schopnosti;                               // Nastaveni stupne schopnosti pozorovatele - uklada se do EEPROM
float     DSO_pozorovatel;                              // stupen schopnosti pozorovatele prevedeny na pokles nebo prirustek magnitudy: DSO_pozorovatel = (DSO_schopnosti - 3) * 0.3
uint16_t  DSO_index_DB = 0;                             // index zvoleneho DSO objektu z celkove databaze DSO objektu 'pole_DSO[]'
uint16_t  DSO_MSA;                                      // zmerena hodnota jasu pozadi ve funkci zjistovani viditelnosti DSO v tisicinach mag/arcsek2

uint8_t   DSO_excentricita;                             // setiny excentricity. ani po zaokrouhleni nesmi byt kvuli zobrazeni na displeji vetsi nez 99
uint8_t   DSO_stupen_plochy;                            // plocha objektu (pocitano jako elipsa s velkou a malou osou z databaze) prevedena na 1 z 5 stupnu (1=mala plocha az 5=velka plocha)

float     DSO_individualni_korekce;                     // priprava na drobne doladeni viditelnosti hvezdokup pro pripad, ze se nachazi na hustem hvezdnem pozadi

uint8_t   DSO_viditelnost;                              // vysledna hodnota vypoctene viditelnosti DSO objektu (0 az 6) na zaklade parametru dalekohledu, jasu pozadi, schopnosti pozorovatele a jasu objektu
                                                        //  0 = neviditelny DSO z duvodu velkeho jasu pozadi, 6 = neviditelny DSO z duvodu jeho polohy pod horizontem
uint8_t   DSO_normal;                                   // normalovy jas oblohy pro urcovani viditelnosti otevrenych hvezdokup v desetinach mag/arcsek2 (217 = 21.7 mag/arcsek2)

float     DSO_extinkce;                                 // zjednoduseny prevod elevace objektu na tloustku atmosfery
float     DSO_plocha;                                   // plocha elipsoviteho DSO objektu spoctena pomoci hlavni a vedlejsi osy [uhlove minuty]

//-----------------
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
void loop(void)
  {

    test_baterie();

    if(digitalRead(pin_TEST_HW) == HIGH and osazeno_uref == true)    // jen testy A/D prevodniku pro vyhodnoceni stavu baterie - bez pripojene komunikace
      {
        zobraz_text(34);                                 // "rEF_U"
        delay(3800);        
        zobraz_cislo(analogRead(pin_refu),0);
        delay(2500);

        zobraz_text(35);                                 // "U_bAt"
        delay(3800);        
        zobraz_cislo(analogRead(pin_AD_BAT),0);
        delay(2500);    
      }
      
    if (digitalRead(pin_DATA_RDY) != predchozi_data_RDY) // kdyz dojde k prepnuti stavu pinu 'pin_DATA_RDY' (zapnuti / vypnuti GPS)
      {
        predchozi_data_RDY = digitalRead(pin_DATA_RDY);  // zaloguje se tento stav
        delay(100);
        SD_log(997,predchozi_data_RDY);
      }

    if (afd < 255)                                                               // Alarm for Darkness je aktivni
      {
        if (afd_nabito == false and (millis() - predchozi_cas_afd) > 10000)      // pokud od minuleho mereni svetla ubehlo alespon 10 sekund
          {
            test_AFD(false);                                                     // provede se jen nastartovani mereni, ktere pak ale v cidle trva neco pres sekundu
            predchozi_cas_afd = millis();
            afd_nabito = true;
          }
    
        if (afd_nabito == true and (millis() - predchozi_cas_afd) > 2000)        // pokud od nastartovani mereni AFD ubehly alespon 2 sekundy
          {
            uint32_t zmerene_AFD = test_AFD(true);                               // provede se cteni registru svetla a jejich zpracovani
            if (millis() - predchozi_zapis_afd > 60000UL)                        // zapis na SD kartu 1x za minutu
              {
                predchozi_zapis_afd = millis();
                logafd(zmerene_AFD);                                             // loguje se ve 32-bitech
              }

            if ((zmerene_AFD % 100) >= 50)                                       // zaokrouleni (priklad mag = 15.278; zmerene_AFD = 15278)
              {
                zmerene_AFD = zmerene_AFD + 100;                                 // po pricteni 100: (zmerene_AFD = 15378)
              }
            zmerene_AFD = zmerene_AFD / 100;                                     // prevod na bajt:  (zmerene_AFD = 153)
            afd_desetiny = zmerene_AFD;                                          // nastaveni globalni promenne pro pripadne logovani do syslogu

            if (zmerene_AFD > afd)                                               // obloha je tmavsi, nez nastavena hodnota
              {
                status_afd = true;
                MODdata[31] = MODdata[31] | 0b1000000000000000;
                digitalWrite(pin_bok_out, HIGH);
              }
            else                                                                 // obloha je svetlejsi, nez nastavena hodnota
              {
                status_afd = false;
                MODdata[31] = MODdata[31] & 0b0111111111111111;
                digitalWrite(pin_bok_out, LOW);
              }

            predchozi_cas_afd = millis();                                        // blokovani dalsiho mereni AFD na dalsich 10 sekund
            afd_nabito = false;
          }        
      }
    else                                                                         // AFD je vypnute (nastavene na 25,5 mag/arcsec2)
      {
        status_afd = false;
        MODdata[31] = MODdata[31] & 0b0111111111111111;
        digitalWrite(pin_bok_out, LOW);
      }

    if (bitRead(signal_LED,4) == true and status_afd == true)                        // kdyz je blikani povolene a zaroven je AFD aktivni
      {
        if (millis() - posledni_blik_afd > 500)                                      // LED pro AFD blika 2x za sekundu
          {
            LED_W(true);
            delay(50);
            LED_W(false);
            posledni_blik_afd = millis();
          }      
      }



    interrupty();                                        // odskoceni na test, jestli neni nejaky pozadavek o komunikaci, nebo jestli neni cas spustit automaticke mereni
    auto_exit_menu = false;                              // v hlavni smycce se rusi pozadavek na automaticke ukonceni menu

    index_posledniho_zaznamu = 1 + (adr_posl_zaznamu - eeaddr_MIN_EEPROM) / delka_zaznamu;

    if (afd_bzuk == true and status_afd == true)         // kdyz je povolene zobrazeni hlaseni "-AFD-" a AFD opravdu nastal
      {
        while (digitalRead(pin_tl_up) == LOW or digitalRead(pin_tl_dn) == LOW or digitalRead(pin_tl_ok) == LOW)  // libovolnym tlacitkem [OK] [NAHORU] [DOLU]
          {
            if (afd_bzuk == true)
              {
                SD_log(992,0);                           // logovani vypnuti alarmoveho displeje tlacitkem
              }
            delay(50);
            afd_bzuk = false;                            // se bzukani trvale vypina (az do dalsiho otevreni polozky menu "AFD" nebo prenastaveni urovne AFD pres seriovou linku)
          }
      }


    if (digitalRead(pin_tl_up) == LOW)                   // zaznam hodnoty s tlacitkem "NAHORU"
      {
        delay(20);
        mereni(1);                                       // parametr je znacka tlacitka, ktera se uklada do zaznamu
        while (digitalRead(pin_tl_up) == LOW) delay(20); // cekani na uvolneni tlacitka
        delay (20);                                      // odruseni zakmitu pri uvolneni tlacitka "NAHORU"
      }


    if (digitalRead(pin_tl_dn) == LOW)                   // zaznam hodnoty s tlacitkem "DOLU"
      {
        delay(20);
        mereni(2);                                       // parametr je znacka tlacitka, ktera se uklada do zaznamu
        while (digitalRead(pin_tl_dn) == LOW) delay(20); // cekani na uvolneni tlacitka
        delay (20);                                      // odruseni zakmitu pri uvolneni tlacitka "NAHORU"
      }


    if (digitalRead(pin_tl_ok) == LOW)                   // stisk tlacitka OK (tady se rozlisuje kratky a dlouhy stisk)
      {
        delay(50);                                       // odruseni zakmitu pri stisku tlacitka
        stisk_time = millis();
        stisk = true;
        uint32_t trvani = 0;
        while (digitalRead(pin_tl_ok) == LOW)
          {
            delay(20);                                   // cekani na uvolneni tlacitka
            trvani = millis() - stisk_time;
            if (trvani >= 500)                           // dlouhy stisk = vstup do menu
              {
                if (menu_dis_led == true)   menu_1();    // vstup do menu se zobrazenim polozek na nekolika 7-segmentovych displejich
                else                        menu_LED();  // vstup do LED menu (jen zakladni polozky, ktere jsou signalizovany blikanim LED )
              }
            if (digitalRead(pin_tl_ok) == HIGH) delay(50); // kdyz se behem drzeni tlacitka OK objevi kratky vypadek kontaktu, tak se odignoruje        
          }
        if (trvani < 500 and trvani > 100)               // kratky stisk = mereni (stisk ale musi trvat alespon 0,1 sekundy)
          {
            mereni(3);                                   // pro tlacitko OK se provadi mereni az pri uvolneni
          }       
    
        stisk=false;
      }

    msleep(100);

  }
//======================================================================================================================



//------------------------------------------
// systemove informace
void sys_info(void)
  {
    uint16_t pomprom;
    
    Serial.print("SW ver.: ");                                 //             verze software
    Serial.println(verzeSW);                                   //             (datum nebo jiny text nadefinovany na zacatku programu)
    Serial.println(' ');                                       //             prazdna radka


    zobraz_RTC(true,true);                                     //             zobrazeni aktualniho zkorigovaneho casu

    pomprom = EEPROM_read(eeaddr_oddelovace);
    Serial.println(lng112);                                    //             Serial.println("\r\nOddelovace:");
    
    Serial.print(lng113);                                      //             Serial.print(" Polozky v souboru: ");
    if ((pomprom & 0b11) ==     0 )  Serial.println(lng078);   //             Serial.println("mezera");
    if ((pomprom & 0b11) ==     1 )  Serial.println(lng079);   //             Serial.println("carka");
    if ((pomprom & 0b11) ==     2 )  Serial.println(lng080);   //             Serial.println("strednik");
    if ((pomprom & 0b11) ==     3 )  Serial.println(lng081);   //             Serial.println("tabulator");

    Serial.print(lng114);                                      //             Serial.print(" Desetinny oddelovac: ");
    if ((pomprom & 0b100) ==    4 )  Serial.println(lng079);   //             Serial.println("carka");
    else                             Serial.println(lng083);   //             Serial.println("tecka");

    if ((pomprom & 0b1000) ==   8 )  Serial.println(lng115);   //             Serial.println(" Uzavirat polozky do uvozovek");
    else                             Serial.println(lng116);   //             Serial.println(" Neuzavirat polozky do uvozovek");

    if ((pomprom & 0b10000) == 16 )  Serial.println(lng117);   //             Serial.println(" Do souboru vkladat hlavicky");
    else                             Serial.println(lng118);   //             Serial.println(" Hlavicky do souboru nevkladat");

    Serial.print(lng119);                                      //             Serial.println("\r\nAutomat:");        
    pomprom = EEPROM_read(eeaddr_automat);
    if (pomprom == 0)                Serial.println(lng120);   //             Serial.println(" Bez automatickeho mereni");
    else
      {
                                     Serial.print(lng121);     //             Serial.print("  Spoustet mereni kazdych ");
                                     Serial.print(pomprom);
                                     Serial.println(lng122);   //             Serial.println(" minut");
      }

    pomprom = EEPROM_read(eeaddr_prumerovani);
    Serial.print(lng123);                                      //             Serial.print("\r\nPrumerovat ");
    Serial.print(pomprom);
    Serial.println(lng124);                                    //             Serial.println(" mereni plosneho jasu");

    pomprom = (EEPROM_read(eeaddr_CRC_tset_lock) & 0b00000001);//             informace o CRC je v bitu 0

    if (pouzit_modbus == false)
      {
        if (pomprom == 0)  Serial.println(lng125);             //             Serial.println("Kontrolni bajt se pri komunikaci pres RS485 nevyhodnocuje.");
        else               Serial.println(lng126);             //             Serial.println("Pri komunikaci pres RS485 je nutne odesilat spravny kontrolni bajt.");    
      }

    AUTOdata_tabulka();                                        //             Informace o automatickem odesilani dat (Master rezim)


    if (pouzit_modbus == false) Serial.println(lng280);        //             Serial.println("MODBUS vypnuty");
    else                        Serial.println(lng279);        //             Serial.println("MODBUS zapnuty");
    
    pomprom = EEPROM_read(eeaddr_stab);
    Serial.print(lng127);                                      //             Serial.print("Rozhodovaci rozdil pro stabilni/nestabilni jas je ");
    Serial.print(pomprom/10.0,1);
    Serial.println(" %");

    pomprom = EEPROM_read(eeaddr_uroven_EEPROM);
    if (pomprom > 0)
      {
        Serial.print(lng128);                                  //             Serial.print("Do EEPROM se ukladaji zaznamy s plosnym jasem nad (tmavsi nez) ");
        Serial.print(pomprom/10.0);
        Serial.println(" mag/arcsec2");
      }
    else
      {
        Serial.println(lng207);                                //             Serial.print("Do EEPROM se ukladaji vsechny zaznamy");        
      }
    if (afd < 255)
      {
        Serial.print(lng303);                                  //             Serial.print("AfD nastaven na ");
        Serial.print(afd / 10.0);
        Serial.println(" mag/arcsec2");
      }
    else
      {
        Serial.println(lng304);                                //             Serial.println("AfD vypnuty");
      }


   
    Serial.print(lng129);                                      //             Serial.print("Unikatni identifikace: ");
    Serial.print(" 0x");
    Serial.println(ID_char);

    pomprom = (0b00001111 & EEPROM_read(eeaddr_SLAVE_baud));
    Serial.print(lng019);                                      //             Serial.print("SLAVE adresa: ");
    Serial.println(pomprom);

    Serial.println(lng130);                                    //             Serial.println("\r\nHardware:");

    Serial.print(lng131);                                      //             Serial.println(" Procesor: ");
    uint32_t idcode = DBGMCU->IDCODE & 0xFFF;
    bool znamy_proc = false;
    switch (idcode)
      {
        case 0x433:
          Serial.print("STM32F401CEU...");
          znamy_proc = true;
          break;

        case 0x431:
          Serial.print("STM32F411CEU...");
          znamy_proc = true;
          break;

        default:
          Serial.println("Unknown");
      }

    if (znamy_proc == true)
      {
        Serial.print(" (FLASH: ");
        Serial.print(VELIKOST_FLASH);
        Serial.println(" kb) - BlackPill");
      }

    if (menu_dis_led == true)
      {
        Serial.println(lng296);                                //             Serial.println(" Displejova verze SQM");      
        Serial.println(lng140);                                //             Serial.println(" Displej: 5x7 segmentu (TM1637)");
      }
    else
      {
        Serial.println(lng297);                                //             Serial.println(" LED verze SQM");    
      }
    
    Serial.println(lng132);                                    //             Serial.println(" Cidlo jasu: TSL2591");    
    if (senzor_BME == true)
      {
        Serial.println(lng135);                                //             Serial.println(" Cidlo vlhkosti, teploty a tlaku: BME280");
      }

    if (modul_LSM303DLHC == true)
      {
        Serial.println(lng265);                                //             Serial.println(" Kompas / naklon LSM303DLHC");    
      }

    Serial.print(lng136);                                      //             Serial.print(" SD karta: ");
    if (pouzivat_SD_kartu == true)
      {
        if (digitalRead(pin_karta_IN) == LOW)
          {
            Serial.print(lng137);                              //             Serial.println("zasunuta");
            SD_volno = SDfree(sd)>>20;                         // prevod z bajtu na MB
            Serial.print(" (Free: ");
            if (SD_volno > 0)                                  // nejaky volny prostor v [MB] na karte jeste existuje
              {
                Serial.print(SD_volno);
                Serial.print('/');
                Serial.print(SDkapacita);
                Serial.println(" [MB])");
              }
            else                                               // nejaka chyba pri zjistovani volneho prostoru z MBR, Boot, nebo FSinfo sektoru
              {
                Serial.print("??");                            // kompilator hlasi problem pri pokusu o tisk tri otazniku v rade, proto musi byt retezes rozdelen
                Serial.println("?)");
              }
          }
        else
          {
            Serial.println(lng138);                            //             Serial.println("vysunuta");        
          }
      }
    else
      {
        Serial.println(lng139);                                //             Serial.println("nepouziva se");
      }
    

    RGB_LED_info();
    BEEP_info();

    if (pocet_cidel_svetla > 1)                                // kdyz neni nastavena expanzni deska pro cidla svetla, nema cenu vypisovat hlaseni o dostupnych vstupech
      {
        Serial.print(lng142);                                  //             Serial.print(" Pocet vstupu rozsirujici desky: ");
        Serial.println(pocet_cidel_svetla);
        Serial.print(lng143);                                  //             Serial.print(" Aktualne aktivni cidlo jasu:    ");
        Serial.println(index_cidla_svetla);
      }


    Serial.println(lng144);                                    //             Serial.println("\r\nEEPROM:");
    Serial.print(lng145);                                      //             Serial.print(" Zacatek oblasti pro data: ");
    dopln_mezery(eeaddr_MIN_EEPROM,6);
    Serial.println(eeaddr_MIN_EEPROM);
    
    Serial.print(lng146);                                      //             Serial.print(" Konec oblasti pro data:   ");
    dopln_mezery(max_zaznam_EEPROM + delka_zaznamu - 1 ,6);
    Serial.println(max_zaznam_EEPROM + delka_zaznamu - 1);

    Serial.print(lng147);                                      //             Serial.print(" Pristi zaznam se ulozi na adresu: ");
    Serial.println(adr_dalsiho_zaznamu);


    Serial.print(lng148);                                      //             Serial.print(" Jeden zaznam v EEPROM je dlouhy: ");
    Serial.print(delka_zaznamu);
    Serial.println(lng149);                                    //             Serial.println (" bajtu");

    Serial.println(lng150);                                    //             Serial.println(" obsahuje tyto polozky: ");
    Serial.println(lng151);                                    //             Serial.println("  - plosny jas           ANO");

    Serial.print(lng152);                                      //             Serial.print  ("  - teplota              ");
#ifdef ukladat_teplotu
    Serial.println(lng153);                                    //             Serial.println("ANO");
#else
    Serial.println(lng154);                                    //             Serial.println("NE");
#endif

    Serial.print(lng155);                                      //             Serial.print  ("  - tlak                 ");
#ifdef ukladat_tlak
    Serial.println(lng153);                                    //             Serial.println("ANO");
#else
    Serial.println(lng154);                                    //             Serial.println("NE");
#endif

    Serial.print(lng156);                                      //             Serial.print  ("  - vlhkost              ");
#ifdef ukladat_vlhkost
    Serial.println(lng153);                                    //             Serial.println("ANO");
#else
    Serial.println(lng154);                                    //             Serial.println("NE");
#endif

    Serial.print(lng157);                                      //             Serial.print  ("  - infra slozka svetla  ");
#ifdef ukladat_infra
    Serial.println(lng153);                                    //             Serial.println("ANO");
#else
    Serial.println(lng154);                                    //             Serial.println("NE");
#endif

    Serial.print(lng158);                                      //             Serial.print  ("  - full svetlo          ");
#ifdef ukladat_full
    Serial.println(lng153);                                    //             Serial.println("ANO");
#else
    Serial.println(lng154);                                    //             Serial.println("NE");
#endif

    Serial.print(lng159);                                      //             Serial.print  ("  - ctrl registr TSL2591 ");        
#ifdef ukladat_contr_reg
    Serial.println(lng153);                                    //             Serial.println("ANO");
#else
    Serial.println(lng154);                                    //             Serial.println("NE");
#endif

    Serial.print(lng206);                                      //             Serial.print  ("  - GPS souradnice       ");        
#ifdef ukladat_GPS
    Serial.println(lng153);                                    //             Serial.println("ANO");
#else
    Serial.println(lng154);                                    //             Serial.println("NE");
#endif

    Serial.print(lng228);                                      //             Serial.print  ("  - aktualni naklon      ");        
#ifdef ukladat_naklon
    Serial.println(lng153);                                    //             Serial.println("ANO");
#else
    Serial.println(lng154);                                    //             Serial.println("NE");
#endif

    Serial.print(lng264);                                      //             Serial.print  ("  - azimut               ");        
#ifdef ukladat_azimut
    Serial.println(lng153);                                    //             Serial.println("ANO");
#else
    Serial.println(lng154);                                    //             Serial.println("NE");
#endif


    Serial.print(lng236);                                      //             Serial.print  ("  - poloha Slun. a Mes.  ");        
#ifdef ukladat_astro
    Serial.println(lng153);                                    //             Serial.println("ANO");
#else
    Serial.println(lng154);                                    //             Serial.println("NE");
#endif

    if (zobraz_rezervy >= 1)
      {
        Serial.print(lng305);                                  //             Serial.print  ("  - rezerva 1            ");        
#ifdef ukladat_rezerva_1
        Serial.println(lng153);                                //             Serial.println("ANO");
#else
        Serial.println(lng154);                                //             Serial.println("NE");
#endif    
      }

    if (zobraz_rezervy >= 2)
      {
        Serial.print(lng306);                                  //             Serial.print  ("  - rezerva 2            ");        
#ifdef ukladat_rezerva_1
        Serial.println(lng153);                                //             Serial.println("ANO");
#else
        Serial.println(lng154);                                //             Serial.println("NE");
#endif    
      }

    if (zobraz_rezervy >= 3)
      {
        Serial.print(lng307);                                  //             Serial.print  ("  - rezerva 3            ");        
#ifdef ukladat_rezerva_1
        Serial.println(lng153);                                //             Serial.println("ANO");
#else
        Serial.println(lng154);                                //             Serial.println("NE");
#endif    
      }

    if (zobraz_rezervy >= 4)
      {
        Serial.print(lng308);                                  //             Serial.print  ("  - rezerva 4            ");        
#ifdef ukladat_rezerva_1
        Serial.println(lng153);                                //             Serial.println("ANO");
#else
        Serial.println(lng154);                                //             Serial.println("NE");
#endif    
      }


    Serial.print(lng237);                                      //             Serial.print("Aktualni souradnice pro astro vypocty (delka / sirka): ")
    if(GeoLon >= 0)  Serial.print("[E] ");
    else             Serial.print("[W] ");
    Serial.print(GeoLon,1);
    Serial.print(" / ");
    if(GeoLat >= 0)  Serial.print("[N] ");
    else             Serial.print("[S] ");   
    Serial.println(GeoLat,1);

    if (trackuj == true)
      {
        Serial.print(lng356);                                    //             Serial.print("Trasovani do souboru 'trck")
        Serial.print(GPS_track_cesta[9]);                        //                 (GPS_track_cesta[] = "TRCK/trck1234.gpx")
        Serial.print(GPS_track_cesta[10]);
        Serial.print(GPS_track_cesta[11]);
        Serial.print(GPS_track_cesta[12]);
        Serial.println(lng357);                                  //             Serial.print(".gpx' ZAPNUTO.")
      }
    else
      {
        Serial.println(lng358);                                  //             Serial.print("Trasovani do GPX souboru vypnuto.")        
      }

                                                               //  vypis napajecich napeti
    cti_napajeni();

    Serial.println(' ');

    Serial.print(lng273);                                      // "Posledni merene napeti zdroje (5V-30V): "
    uint16_t RTC_9V = (RTC->BKP1R);                            //  posledni ulozene napajeci napeti pred zapnutim USB
    Serial.print(RTC_9V / 10.0);
    Serial.println(lng384);                                    // "[V] (nyni na USB)"
    
    Serial.print(lng274);                                      // "Napeti zalohovaci baterie (3V): "
    Serial.print(bat_3V);
    Serial.print("[V] (");
    Serial.print(bat_proc);
    Serial.println("%)");
    if (osazeno_uref == true)                                  // referencni napeti se zobrazuje jen kdyz je reference skutecne osazena
      {
        Serial.print(lng275);                                  // "Reference (1V8): "
        Serial.print(ref_in);
        Serial.println("[V]");    
      }

    Serial.print(lng276);                                      // "Napeti procesoru (3V3): "
    Serial.print(Vcc);
    Serial.println("[V]");

    Serial.println(' ');
    vypis_budiku(2);                                           // vypise budiky pro DS3231 (neaktivni budiky vynechava)

   
    Serial.println(lng160);                                    //             Serial.println("\r\nKalibrace cidla teploty");
    Serial.println(lng161);                                    //             Serial.println("index ; merena  ; skutecna");
    Serial.println("-----------------------------");
    for (uint8_t i = 0 ; i < 7 ; i++)
      {
        pomprom = EEPROM_read_int((i*4)+eeaddr_teplotni_kalibrace);
        Serial.print(i+1);
        Serial.print(" ; ");
        dopln_mezery(citelna_teplota(pomprom),5);
        Serial.print( citelna_teplota(pomprom),2);             // (citelna merena teplota)
        Serial.print(" 'C ; ");

        pomprom = EEPROM_read_int((i*4)+eeaddr_teplotni_kalibrace + 2);
        dopln_mezery(citelna_teplota(pomprom),5);
        Serial.print( citelna_teplota(pomprom),2);             // (citelna zobrazovana teplota)
        Serial.println(" 'C");        
      }


    Serial.print(lng162);                                      //             Serial.print("\r\nKalibrace cidla plosneho jasu [");
    Serial.print(index_cidla_svetla);
    Serial.println("]");
    Serial.println(lng163);                                    //             Serial.println("index ; merene ; skutecne");
    Serial.println("--------------------------");
    uint16_t posun = ((index_cidla_svetla-1) * 60) + eeaddr_svetelna_kalibrace; 
    for (uint8_t i = 0 ; i < 15 ; i++)
      {
        if( i < 9)   Serial.print(' ');                        // jen zarovnani cisel polozek
        Serial.print(i+1);
        Serial.print(" ; ");
        pomprom = EEPROM_read_int(posun + (i*4));
        dopln_mezery(citelne_svetlo(pomprom),5);
        Serial.print(citelne_svetlo(pomprom),3);
        Serial.print(" ; ");
        pomprom = EEPROM_read_int(posun + (i*4) + 2);
        dopln_mezery(citelne_svetlo(pomprom),5);
        Serial.println(citelne_svetlo(pomprom),3);
      }    
  
  }
//----------------------------------------------



//---------------------------------------------------------------------
// formatovani vypisu kalibracnich konstant
//   cislo se hned na zacatku oseka o desetinne casti
//  'pocet_mist' udava, na jak dlouhy retezec se doplni cela cast cisla
//   priklady parametru:    15.354 , 4     prida pred retezec 2 mezery
//                          1.078  , 4     prida pred retezec 3 mezery
//                         -24.11  , 3     neprida zadnou mezeru
void dopln_mezery(int16_t cislo, uint8_t pocet_mist)
  {
    uint8_t delka_cisla = 5;
    if (cislo <     0)   delka_cisla ++;                       // zaporne cislo pridava jeden znak pro znamenko
    cislo = abs(cislo);
    if (cislo < 10000)   delka_cisla --;
    if (cislo <  1000)   delka_cisla --;
    if (cislo <   100)   delka_cisla --;
    if (cislo <    10)   delka_cisla --;

    while (delka_cisla < pocet_mist)
      {
        delka_cisla ++;
        Serial.print(' ');
      }
    
  }
//----------------------------------------------


//----------------------------------------------
// vypis aktualniho nastaveni funkci pro RGB LED
void RGB_LED_info(void)
  {
    Serial.println(lng290);                                                 // " Funkce RGB LED:"
    Serial.print(lng286);                                                   // "   LED baterie:         "
    if (bitRead(signal_LED,0) == true) Serial.println(lng153);              // "ANO"
    else                               Serial.println(lng154);              // "NE"

    Serial.print(lng287);                                                   // "   LED pri mereni:      "
    if (bitRead(signal_LED,1) == true) Serial.println(lng153);              // "ANO"
    else                               Serial.println(lng154);              // "NE
  
    Serial.print(lng288);                                                   // "   LED pri chybe:       "
    if (bitRead(signal_LED,2) == true) Serial.println(lng153);              // "ANO"
    else                               Serial.println(lng154);              // "NE

    Serial.print(lng289);                                                   // "   LED pri komunikaci: "
    if (bitRead(signal_LED,3) == true) Serial.println(lng153);              // "ANO"
    else                               Serial.println(lng154);              // "NE

    Serial.print(lng300);                                                   // "   LED pri AfD:        "
    if (bitRead(signal_LED,4) == true) Serial.println(lng153);              // "ANO"
    else                               Serial.println(lng154);              // "NE

    Serial.print(lng355);                                                   // "   LED pri GPS tracku  "
    if (bitRead(signal_LED,5) == true) Serial.println(lng153);              // "ANO"
    else                               Serial.println(lng154);              // "NE

  
  }


//----------------------------------------------
// vypis aktualniho nastaveni funkci pro signalizaci pipanim
void BEEP_info(void)
  {
    Serial.println(lng330);                                                 // " Signalizace piskaku:"
    Serial.print(lng331);                                                   // "   baterie:                "
    if (bitRead(signal_BEEP,0) == true) Serial.println(lng153);             // "ANO"
    else                                Serial.println(lng154);             // "NE"

    Serial.print(lng332);                                                   // "   mereni:                 "
    if (bitRead(signal_BEEP,1) == true) Serial.println(lng153);             // "ANO"
    else                                Serial.println(lng154);             // "NE
  
    Serial.print(lng333);                                                   // "   budik a odpocet:        "
    if (bitRead(signal_BEEP,2) == true) Serial.println(lng153);             // "ANO"
    else                                Serial.println(lng154);             // "NE

    Serial.print(lng334);                                                   // "   HW problemy:            "
    if (bitRead(signal_BEEP,3) == true) Serial.println(lng153);             // "ANO"
    else                                Serial.println(lng154);             // "NE

    Serial.print(lng335);                                                   // "   operace s TS tlacitkem: "
    if (bitRead(signal_BEEP,4) == true) Serial.println(lng153);             // "ANO"
    else                                Serial.println(lng154);             // "NE

    Serial.print(lng336);                                                   // "   priblizovani k Ra-Dec:  "
    if (bitRead(signal_BEEP,5) == true) Serial.println(lng153);             // "ANO"
    else                                Serial.println(lng154);             // "NE

    Serial.print(lng337);                                                   // "   dalsi vystrahy:         "
    if (bitRead(signal_BEEP,6) == true) Serial.println(lng153);             // "ANO"
    else                                Serial.println(lng154);             // "NE

    Serial.print(lng338);                                                   // "   stopky:                 "
    if (bitRead(signal_BEEP,7) == true) Serial.println(lng153);             // "ANO"
    else                                Serial.println(lng154);             // "NE

    Serial.print(lng353);                                                   // "   zapnuti [Z]:            "
    if (bitRead(signal_BEEP,8) == true) Serial.println(lng153);             // "ANO"
    else                                Serial.println(lng154);             // "NE


    
  }



//----------------------------------------------
void default_kalibrace_svetla(void)
  {

    for (uint8_t i = 1; i < 8 ; i++)
      {
        kolecko();                                             // vyckavaci kolecko na prostredni sedmisegmentovce
        // v EEPROM se nachazi 7 bloku kalibracnich dat (pro 7 cidel na rozsirujici desce), kazdy blok ma 15 bodu, kazdy bod ma 2 + 2 bajty (merena a skutecna hodnota) = 60 bajtu na blok
        //               bloky zacinaji na adrese 50 (za kalibracni tabulkou teplot)
        // Nasledujici zapis nulovych hodnot by se dal udelat jednoduchou smyckou, ale pro pripad, ze by se ukazalo, ze je lepsi zapisovat nejake jine hodnoty jsem to nechal oddelene
        
        uint16_t posun = ((i-1) * 60) + eeaddr_svetelna_kalibrace;   
        EEPROM_write_int( 0 + posun   ,     0);                //  1. kalibracni bod pro svetlo -  index[0]
        EEPROM_write_int( 2 + posun   ,     0);
    
        EEPROM_write_int( 4 + posun   ,     0);                //  2. kalibracni bod pro svetlo -  index[1]
        EEPROM_write_int( 6 + posun   ,     0);
    
        EEPROM_write_int( 8 + posun   ,     0);                //  3. kalibracni bod pro svetlo -  index[2]
        EEPROM_write_int(10 + posun   ,     0);
    
        EEPROM_write_int(12 + posun   ,     0);                //  4. kalibracni bod pro svetlo -  index[3]
        EEPROM_write_int(14 + posun   ,     0);   
    
        EEPROM_write_int(16 + posun   ,     0);                //  5. kalibracni bod pro svetlo -  index[4]
        EEPROM_write_int(18 + posun   ,     0);
    
        EEPROM_write_int(20 + posun   ,     0);                //  6. kalibracni bod pro svetlo -  index[5]
        EEPROM_write_int(22 + posun   ,     0);
    
        EEPROM_write_int(24 + posun   ,     0);                //  7. kalibracni bod pro svetlo -  index[6]
        EEPROM_write_int(26 + posun   ,     0);
    
        EEPROM_write_int(28 + posun   ,     0);                //  8. kalibracni bod pro svetlo -  index[7]
        EEPROM_write_int(30 + posun   ,     0);

        kolecko();                                             // vyckavaci kolecko na prostredni sedmisegmentovce    
    
        EEPROM_write_int(32 + posun   ,     0);                //  9. kalibracni bod pro svetlo -  index[8]
        EEPROM_write_int(34 + posun   ,     0);
    
        EEPROM_write_int(36 + posun   ,     0);                // 10. kalibracni bod pro svetlo -  index[9]
        EEPROM_write_int(38 + posun   ,     0);
    
        EEPROM_write_int(40 + posun   ,     0);                // 11. kalibracni bod pro svetlo -  index[10]
        EEPROM_write_int(42 + posun   ,     0);
    
        EEPROM_write_int(44 + posun   ,     0);                // 12. kalibracni bod pro svetlo -  index[11]
        EEPROM_write_int(46 + posun   ,     0);
    
        EEPROM_write_int(48 + posun   ,     0);                // 13. kalibracni bod pro svetlo -  index[12]
        EEPROM_write_int(50 + posun   ,     0);
        
        EEPROM_write_int(52 + posun   ,     0);                // 14. kalibracni bod pro svetlo -  index[13]
        EEPROM_write_int(54 + posun   ,     0);
    
        EEPROM_write_int(56 + posun   ,     0);                // 15. kalibracni bod pro svetlo -  index[14]
        EEPROM_write_int(58 + posun   ,     0);
        
      }
  }
//----------------------------------------------



//----------------------------------------------
void default_kalibrace_teploty(void)
  {
    kolecko();                                             // vyckavaci kolecko na prostredni sedmisegmentovce
    // Nasledujici zapis hodnot 0 by se dal udelat jednoduchou smyckou, ale pro pripad, ze by se ukazalo, ze je lepsi zapisovat nejake jine hodnoty jsem to nechal oddelene
    EEPROM_write_int(eeaddr_teplotni_kalibrace       ,  0);                               // 1. kalibracni bod pro teplotu -  index[0]   
    EEPROM_write_int(eeaddr_teplotni_kalibrace + 2   ,  0);

    EEPROM_write_int(eeaddr_teplotni_kalibrace + 4   ,  0);                               // 2. kalibracni bod pro teplotu -  index[1]   
    EEPROM_write_int(eeaddr_teplotni_kalibrace + 6   ,  0);

    EEPROM_write_int(eeaddr_teplotni_kalibrace + 8   ,  0);                               // 3. kalibracni bod pro teplotu -  index[2]   
    EEPROM_write_int(eeaddr_teplotni_kalibrace +10   ,  0);

    EEPROM_write_int(eeaddr_teplotni_kalibrace +12   ,  0);                               // 4. kalibracni bod pro teplotu -  index[3]   
    EEPROM_write_int(eeaddr_teplotni_kalibrace +14   ,  0);

    kolecko();                                             // vyckavaci kolecko na prostredni sedmisegmentovce    

    EEPROM_write_int(eeaddr_teplotni_kalibrace +16   ,  0);                               // 5. kalibracni bod pro teplotu -  index[4]   
    EEPROM_write_int(eeaddr_teplotni_kalibrace +18   ,  0);

    EEPROM_write_int(eeaddr_teplotni_kalibrace +20   ,  0);                               // 6. kalibracni bod pro teplotu -  index[5]   
    EEPROM_write_int(eeaddr_teplotni_kalibrace +22   ,  0); 

    EEPROM_write_int(eeaddr_teplotni_kalibrace +24   ,  0);                               // 7. kalibracni bod pro teplotu -  index[6]   
    EEPROM_write_int(eeaddr_teplotni_kalibrace +26   ,  0); 
  }

// #doc#12
void default_parametry(void)
  {
    kolecko();                                             // vyckavaci kolecko na prostredni sedmisegmentovce    
    EEPROM_write_long(    eeaddr_RTC_set       ,            0);                 // cas posledniho serizeni = 1.1.1970 0:00:00
    EEPROM_write_long(    eeaddr_RTC_korekce   , 0x7FFFFFFFUL);                 // sekunda se pricita jednou za 68 let
    EEPROM_write(         eeaddr_leto_zima     ,            0);                 // SEC
    EEPROM_write(         eeaddr_oddelovace    ,   0b00010110);                 // des. oddelovac carka, oddelovac polozek strednik, hlavicku vkladat, nezavirat do uvozovek
    EEPROM_write(         eeaddr_automat       ,            0);                 // automaticke spousteni vypnute
    EEPROM_write(         eeaddr_prumerovani   ,            3);                 // 3x prumerovani
    if (osazeno_DISPLEJ == true)
      {
        EEPROM_write(     eeaddr_modbus_LED    ,   0b00000011);                 // osazeny displej = displejova verze SQM; modbus pres RS485 je defaultne zapnuty    
      }
    else
      {
        EEPROM_write(     eeaddr_modbus_LED    ,   0b00000001);                 // neosazeny displej = LED verze SQM; modbus pres RS485 je defaultne zapnuty    
      }
      
    EEPROM_write(         eeaddr_LED           ,            0);                 // RGB LED je defaultne vypnuta pro vsechny operace (zapina se pres @L_)
    kolecko();                                             // vyckavaci kolecko na prostredni sedmisegmentovce    
    EEPROM_write_int(     eeaddr_beep_bity     ,  0b111111111);                 // veskere pipani je povolene (zatim pouzito 9 spodnich bitu)
    EEPROM_write(         eeaddr_elevace_soumrak  ,        10);                 // uzivatlsky nastavitalna elevace Slunce pro soumrak
    EEPROM_write(         eeaddr_SLAVE_baud    ,            1);                 // komunikacni rychlost 9600; SLAVE adresa = 1
    EEPROM_write(         eeaddr_CRC_tset_lock ,   0b00000001);                 // testuje kontrolni bajt pri komunikaci pres RS485; tlacitko TS je odemknute, RTC_set.csv zakazan
    EEPROM_write(         eeaddr_stab          ,           20);                 // nestabilni jas je hlaseny pri rozdilu dvou sousednich mereni nad 2 %
    EEPROM_write(         eeaddr_pocet_cidel   ,            1);                 // pocet cidel na expanzni desce
    EEPROM_write(         eeaddr_10kB_znacka   ,            0);                 // zachytny bod hledani (po kazdem 100. zaznamu se aktualizuje kvuli rychlejsimu hledani volneho mista v EEPROM)
    EEPROM_write(         eeaddr_uroven_EEPROM ,            0);                 // hranice plosneho jasu pro ukladani do EEPROM a na kartu v desetinach mag/arcsec2) (0 az 25,5 mag/arcsec2)
    EEPROM_write_int(     eeaddr_GEO_lat       ,          500);                 // domaci zemepisna sirka pro astro vypocty na 50.0 stupnu
    EEPROM_write_int(     eeaddr_GEO_lon       ,          150);                 // domaci zemepisna delka pro astro vypocty na 15.0 stupnu
    EEPROM_write(         eeaddr_zima_hod      ,          101);                 // posun casu proti UTC v zime = +1 hodina (SEC)      (hodnota je zvetsena o 100, takze -5 hodin by se zapsalo jako 95)
    kolecko();                                             // vyckavaci kolecko na prostredni sedmisegmentovce    
    EEPROM_write(         eeaddr_leto_hod      ,          102);                 // posun casu proti UTC v lete = +2 hodiny (SELC)
    EEPROM_write_long(    eeaddr_menu_bity     , 0xFFFFFFFFUL);                 // defaultne jsou vsechny polozky v menu povolene
    EEPROM_write_int(     eeaddr_perif_bity    ,       0x001F);                 // defaultne je vsech 5 periferii zapnutych (neosazene periferie se pak vypinaji automaticky)
    EEPROM_write(         eeaddr_AfD           ,          255);                 // Alam for Darkness vypnuty (nastaveny na tak vysokou hodnotu, ktera nemuze nastat - 25,5 mag/arcsec2)
    EEPROM_write(         eeaddr_txt_zony      ,          ' ');                 // 4 ASCII znaky pro 'zimni' casovou zonu
    EEPROM_write(         eeaddr_txt_zony + 1  ,          'S');                 // 
    EEPROM_write(         eeaddr_txt_zony + 2  ,          'E');                 // 
    EEPROM_write(         eeaddr_txt_zony + 3  ,          'C');                 // 
    EEPROM_write(         eeaddr_txt_zony + 4  ,          'S');                 // 4 ASCII znaky pro letni casovou zonu
    EEPROM_write(         eeaddr_txt_zony + 5  ,          'E');                 // 
    EEPROM_write(         eeaddr_txt_zony + 6  ,          'L');                 // 
    EEPROM_write(         eeaddr_txt_zony + 7  ,          'C');                 // 
    kolecko();                                             // vyckavaci kolecko na prostredni sedmisegmentovce    
    EEPROM_write_int(     eeaddr_luxmetr       ,          250);                 // parametr 'a' pro kalibraci luxmetru (*0.01)   (s ulozenym cislem 250 se bude pocitat jako s 2.5)
    EEPROM_write_int(     eeaddr_luxmetr + 2   ,            0);                 // parametr 'b' pro kalibraci luxmetru (*0.01)  zaporna cisla se ukladaji jako binarni doplnek (-10.55 = 64481)
    EEPROM_write_int(     eeaddr_luxmetr + 4   ,            0);                 // parametr 'c' pro kalibraci luxmetru (*0.000 000 1) ulozene cislo 16 by se pocitalo jako 0.000 001 6
    EEPROM_write(         eeaddr_kompas_offset ,          127);                 // doladeni kompasu (127 = pootoceni o 0 stupnu)
    EEPROM_write_int(     eeaddr_alarmy        ,         1440);                 // prvni  budik vypnout
    EEPROM_write_int(     eeaddr_alarmy +  2   ,         1440);                 // druhy  budik vypnout
    kolecko();                                             // vyckavaci kolecko na prostredni sedmisegmentovce    
    EEPROM_write_int(     eeaddr_alarmy +  4   ,         1440);                 // treti  budik vypnout
    EEPROM_write_int(     eeaddr_alarmy +  6   ,         1440);                 // ctvrty budik vypnout
    EEPROM_write_int(     eeaddr_alarmy +  8   ,         1440);                 // paty   budik vypnout
    EEPROM_write_int(     eeaddr_alarmy + 10   ,         1440);                 // odpocet (sesty budik) vypnout
    EEPROM_update(        eeaddr_TEST_alarm    ,            0);                 // znacka testovaciho alarmu se maze
    EEPROM_write_int(     eeaddr_GPS_track_id  ,            0);                 // cislovani trasovacich souboru od nuly a zastavit trasovani
    EEPROM_write(         eeaddr_GPS_track_interval ,      20);                 // defaultne se trackuje po 20 sekundach
    EEPROM_write(         eeaddr_AUTOkom       ,            0);                 // defaultne se hodnoty do seriovych linek neodesilaji (rezim "master" je VYPNUTY)
    EEPROM_write(         eeaddr_MOD_autoupdate,            0);                 // defaultne se modbusove registry 30001 az 30031 po kazdem mereni neaktualizuji (musi se vyzadat prikazem 2)
    EEPROM_write(         eeaddr_bortle        ,            0);                 // defaultni zobrazeni Bortleho stupne v menu zakazano
    EEPROM_write_int(     eeaddr_DSO_setup     ,       0x0003);                 // nastaveni paramnetru funkce pro urcovani viditelnosti DSO (schopnosti=3, ostatni parametry 0, 0)
    EEPROM_write(         eeaddr_DSO_normal_MSA,          210);                 // normalovy jas oblohy pro urcovani viditelnosti otevrenych hvezdokup
    EEPROM_write(         eeaddr_AFD_styl      ,            0);                 // AFD po zapnuti napajeni nebude signalizovat, ale bude logovat
    EEPROM_write(         eeaddr_autokalibrator,            0);                 // Testovani pridavneho kalibratoru je defaultne vypnute, aby nezdrzovalo start

    EEPROM_write(         eeaddr_servis        ,            0);                 // adresa pro vyvoj (testovani novych funkci je ve verejnych verzich programu vypnute)
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
